sean618/MakerTiles/hardware/Boards/Extra/USBPower/v0.5/USBPower.kicad_pcb

## KiCad design hardware/Boards/Extra/USBPower/v0.5/USBPower.kicad_pcb (2026-06-21)

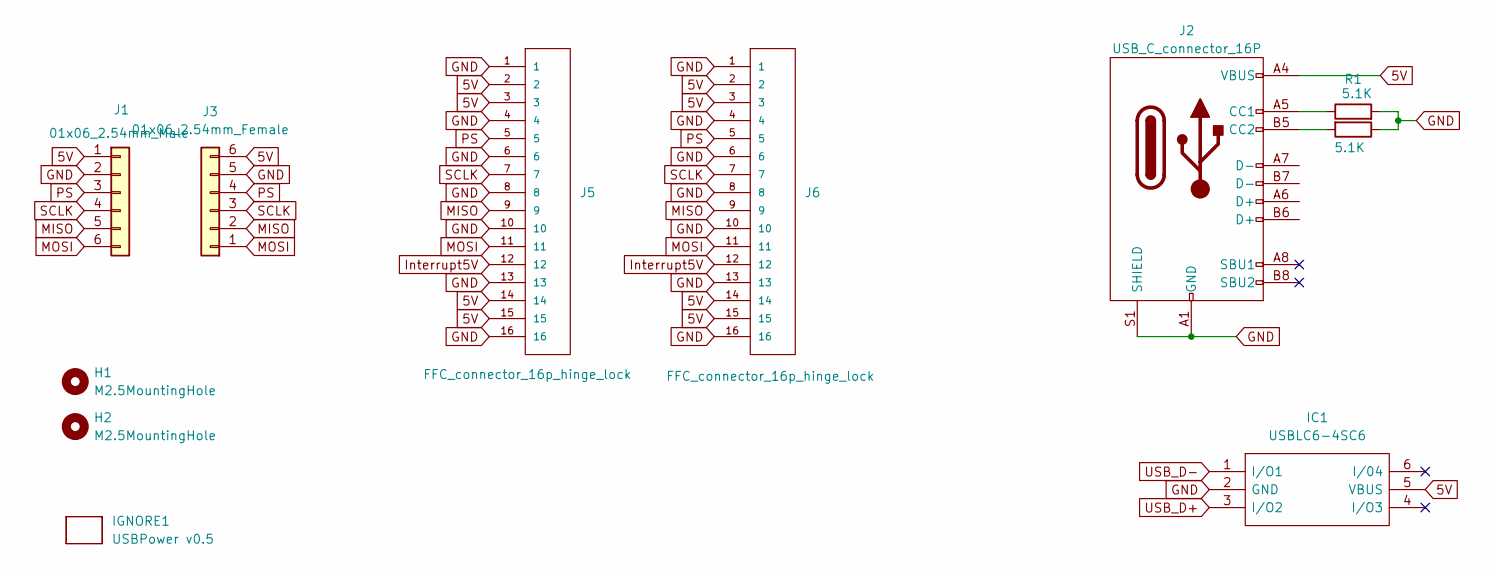
[picture p28: schematic USBPower.kicad_sch]

Parts:
H1, H2: M2.5MountingHole; MountingHole_2.7mm_M2.5_ISO7380
IC1: USBLC6-4SC6; SOT-23-6; Manufacturer_Part_Number USBLC6-2P6
IGNORE1: USBPower v0.5; BoardText
J1: 01x06_2.54mm_Male
J2: USB_C_connector_16P; USB_C_Receptacle_16P
J3: 01x06_2.54mm_Female
J5, J6: FFC_connector_16p_hinge_lock
R1, R2: 5.1K; R_0402_1005Metric

Connections:
5V: IC1.5 (VBUS), J1.1, J2.A4 (VBUS), J2.A9 (VBUS), J2.B4 (VBUS), J2.B9 (VBUS), J3.6, J5.2, J5.3, J5.14, J5.15, J6.2, J6.3, J6.14, J6.15
GND: IC1.2 (GND), J1.2, J2.A1 (GND), J2.A12 (GND), J2.B1 (GND), J2.B12 (GND), J2.S1 (SHIELD), J3.5, J5.1, J5.4, J5.6, J5.8, J5.10, J5.13, J5.16, J6.1, J6.4, J6.6, J6.8, J6.10, J6.13, J6.16, R1.2, R2.1
Interrupt5V: J5.12, J6.12
MISO: J1.5, J3.2, J5.9, J6.9
MOSI: J1.6, J3.1, J5.11, J6.11
unnamed: J2.A5 (CC1), R1.1
unnamed: J2.B5 (CC2), R2.2
PS: J1.3, J3.4, J5.5, J6.5
SCLK: J1.4, J3.3, J5.7, J6.7
USB_D+: IC1.3 (I/O2)
USB_D-: IC1.1 (I/O1)

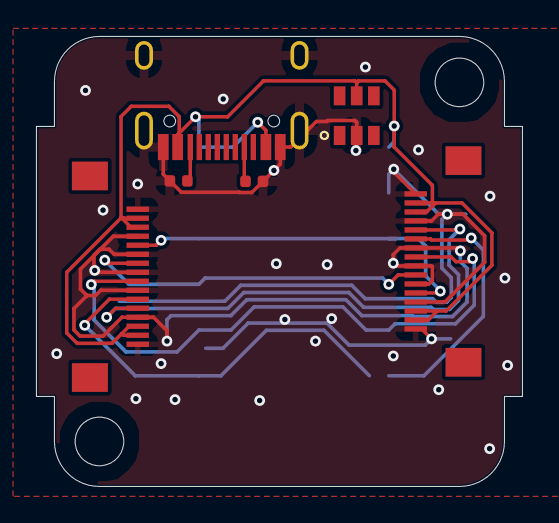
[picture p29: board USBPower.kicad_pcb from above]

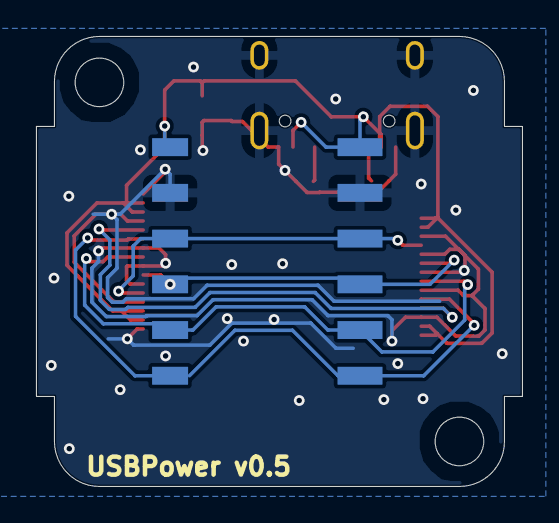
[picture p30: board USBPower.kicad_pcb from below]

Board: 4 copper layers, 27.0 x 25.0 mm, 11 parts (2 on the bottom side), 9 nets.
