sean618/MakerTiles/hardware/Boards/LedMatrix/v0.2/LedMatrix.kicad_pcb

## KiCad design hardware/Boards/LedMatrix/v0.2/LedMatrix.kicad_pcb (2026-06-21, an earlier design)

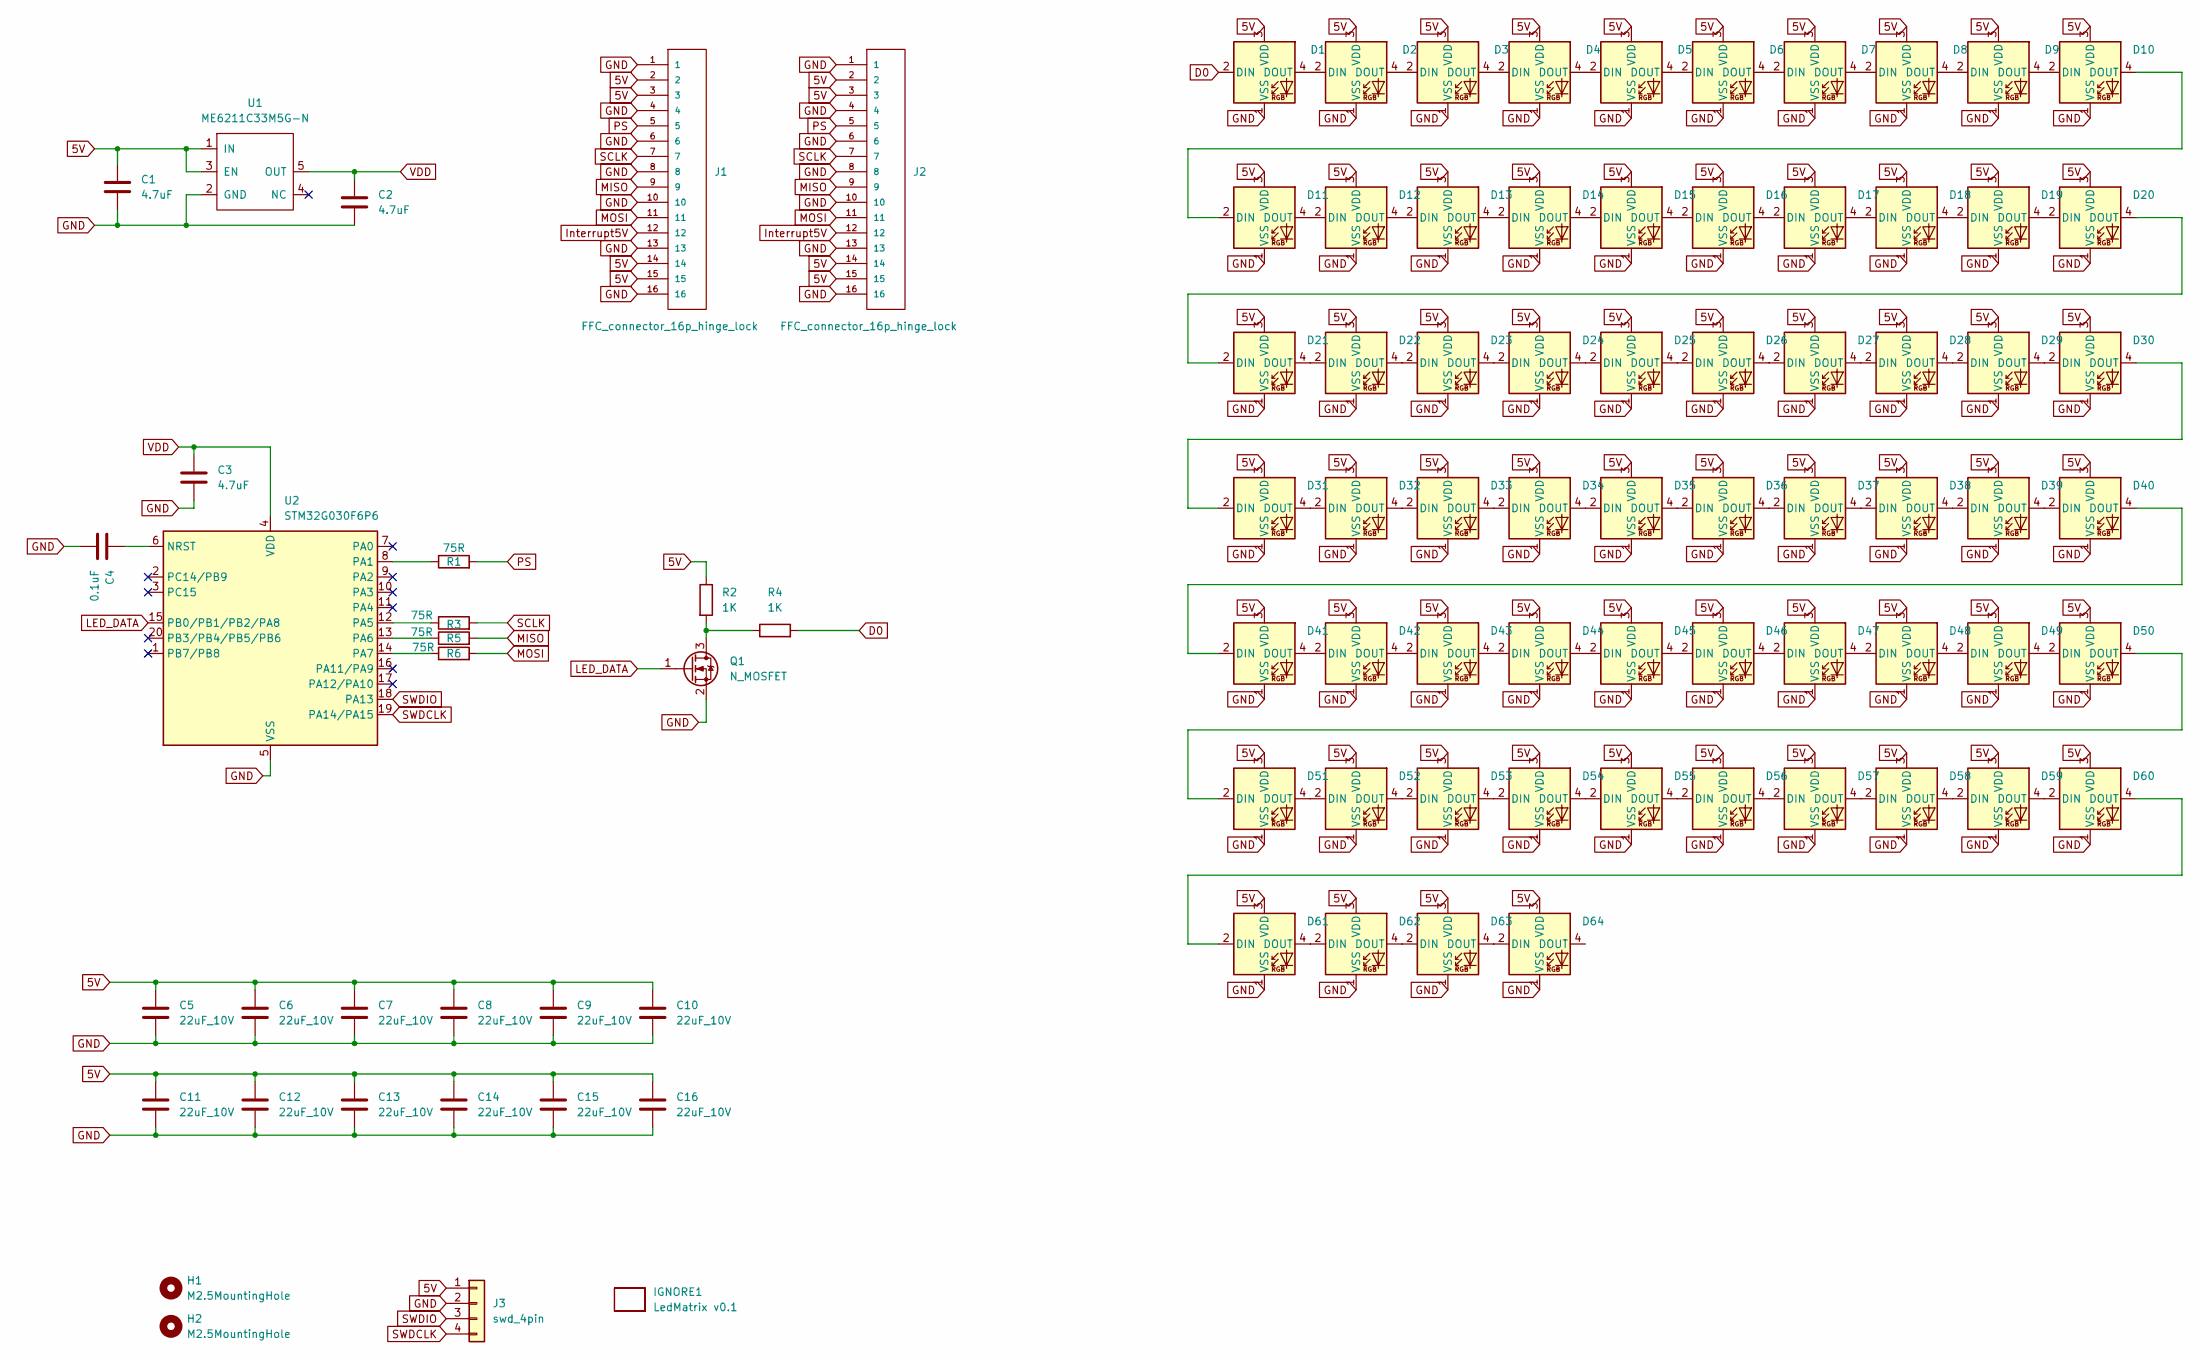
[picture p31: schematic LedMatrix.kicad_sch]

Parts:
C1, C2, C3: 4.7uF; C_0402_1005Metric
C4: 0.1uF; C_0402_1005Metric
C5, C6, C7, C8, C9, C10, C11, C12, C13, C14, C15, C16: 22uF_10V; C_0603_1608Metric
D1, D2, D3, D4, D5, D6, D7, D8, D9, D10, D11, D12, D13, D14, D15, D16, D17, D18, D19, D20, D21, D22, D23, D24, D25, D26, D27, D28, D29, D30, D31, D32, D33, D34, D35, D36, D37, D38, D39, D40, D41, D42, D43, D44, D45, D46, D47, D48, D49, D50, D51, D52, D53, D54, D55, D56, D57, D58, D59, D60, D61, D62, D63, D64: xl_ws2812b_small
H1, H2: M2.5MountingHole; MountingHole_2.7mm_M2.5_ISO7380
IGNORE1: LedMatrix v0.1; BoardText
J1, J2: FFC_connector_16p_hinge_lock
J3: swd_4pin; swd_header
Q1: N_MOSFET; SOT-23
R1, R3, R5, R6: 75R; R_0402_1005Metric
R2, R4: 1K; R_0402_1005Metric
U1: ME6211C33M5G-N; SOT-23-5
U2: STM32G030F6P6; TSSOP-20_4.4x6.5mm_P0.65mm

Connections:
5V: C1.1, C5.1, C6.1, C7.1, C8.1, C9.1, C10.1, C11.1, C12.1, C13.1, C14.1, C15.1, C16.1, D1.3 (VDD), D2.3 (VDD), D3.3 (VDD), D4.3 (VDD), D5.3 (VDD), D6.3 (VDD), D7.3 (VDD), D8.3 (VDD), D9.3 (VDD), D10.3 (VDD), D11.3 (VDD), D12.3 (VDD), D13.3 (VDD), D14.3 (VDD), D15.3 (VDD), D16.3 (VDD), D17.3 (VDD), D18.3 (VDD), D19.3 (VDD), D20.3 (VDD), D21.3 (VDD), D22.3 (VDD), D23.3 (VDD), D24.3 (VDD), D25.3 (VDD), D26.3 (VDD), D27.3 (VDD), D28.3 (VDD), D29.3 (VDD), D30.3 (VDD), D31.3 (VDD), D32.3 (VDD), D33.3 (VDD), D34.3 (VDD), D35.3 (VDD), D36.3 (VDD), D37.3 (VDD), D38.3 (VDD), D39.3 (VDD), D40.3 (VDD), D41.3 (VDD), D42.3 (VDD), D43.3 (VDD), D44.3 (VDD), D45.3 (VDD), D46.3 (VDD), D47.3 (VDD), D48.3 (VDD), D49.3 (VDD), D50.3 (VDD), D51.3 (VDD), D52.3 (VDD), D53.3 (VDD), D54.3 (VDD), D55.3 (VDD), D56.3 (VDD), D57.3 (VDD), D58.3 (VDD), D59.3 (VDD), D60.3 (VDD), D61.3 (VDD), D62.3 (VDD), D63.3 (VDD), D64.3 (VDD), J1.2, J1.3, J1.14, J1.15, J2.2, J2.3, J2.14, J2.15, J3.1, R2.1, U1.1 (IN), U1.3 (EN)
D0: D1.2 (DIN), R4.2
GND: C1.2, C2.2, C3.2, C4.2, C5.2, C6.2, C7.2, C8.2, C9.2, C10.2, C11.2, C12.2, C13.2, C14.2, C15.2, C16.2, D1.1 (VSS), D2.1 (VSS), D3.1 (VSS), D4.1 (VSS), D5.1 (VSS), D6.1 (VSS), D7.1 (VSS), D8.1 (VSS), D9.1 (VSS), D10.1 (VSS), D11.1 (VSS), D12.1 (VSS), D13.1 (VSS), D14.1 (VSS), D15.1 (VSS), D16.1 (VSS), D17.1 (VSS), D18.1 (VSS), D19.1 (VSS), D20.1 (VSS), D21.1 (VSS), D22.1 (VSS), D23.1 (VSS), D24.1 (VSS), D25.1 (VSS), D26.1 (VSS), D27.1 (VSS), D28.1 (VSS), D29.1 (VSS), D30.1 (VSS), D31.1 (VSS), D32.1 (VSS), D33.1 (VSS), D34.1 (VSS), D35.1 (VSS), D36.1 (VSS), D37.1 (VSS), D38.1 (VSS), D39.1 (VSS), D40.1 (VSS), D41.1 (VSS), D42.1 (VSS), D43.1 (VSS), D44.1 (VSS), D45.1 (VSS), D46.1 (VSS), D47.1 (VSS), D48.1 (VSS), D49.1 (VSS), D50.1 (VSS), D51.1 (VSS), D52.1 (VSS), D53.1 (VSS), D54.1 (VSS), D55.1 (VSS), D56.1 (VSS), D57.1 (VSS), D58.1 (VSS), D59.1 (VSS), D60.1 (VSS), D61.1 (VSS), D62.1 (VSS), D63.1 (VSS), D64.1 (VSS), J1.1, J1.4, J1.6, J1.8, J1.10, J1.13, J1.16, J2.1, J2.4, J2.6, J2.8, J2.10, J2.13, J2.16, J3.2, Q1.2 (S), U1.2 (GND), U2.5 (VSS)
Interrupt5V: J1.12, J2.12
LED_DATA: Q1.1 (G), U2.15 (PB0/PB1/PB2/PA8)
MISO: J1.9, J2.9, R5.2
MOSI: J1.11, J2.11, R6.2
unnamed: D1.4 (DOUT), D2.2 (DIN)
unnamed: D2.4 (DOUT), D3.2 (DIN)
unnamed: D3.4 (DOUT), D4.2 (DIN)
unnamed: D4.4 (DOUT), D5.2 (DIN)
unnamed: D5.4 (DOUT), D6.2 (DIN)
unnamed: D6.4 (DOUT), D7.2 (DIN)
unnamed: D7.4 (DOUT), D8.2 (DIN)
unnamed: D8.4 (DOUT), D9.2 (DIN)
unnamed: D9.4 (DOUT), D10.2 (DIN)
unnamed: D10.4 (DOUT), D11.2 (DIN)
unnamed: D11.4 (DOUT), D12.2 (DIN)
unnamed: D12.4 (DOUT), D13.2 (DIN)
unnamed: D13.4 (DOUT), D14.2 (DIN)
unnamed: D14.4 (DOUT), D15.2 (DIN)
unnamed: D15.4 (DOUT), D16.2 (DIN)
unnamed: D16.4 (DOUT), D17.2 (DIN)
unnamed: D17.4 (DOUT), D18.2 (DIN)
unnamed: D18.4 (DOUT), D19.2 (DIN)
unnamed: D19.4 (DOUT), D20.2 (DIN)
unnamed: D20.4 (DOUT), D21.2 (DIN)
unnamed: D21.4 (DOUT), D22.2 (DIN)
unnamed: D22.4 (DOUT), D23.2 (DIN)
unnamed: D23.4 (DOUT), D24.2 (DIN)
unnamed: D24.4 (DOUT), D25.2 (DIN)
unnamed: D25.4 (DOUT), D26.2 (DIN)
unnamed: D26.4 (DOUT), D27.2 (DIN)
unnamed: D27.4 (DOUT), D28.2 (DIN)
unnamed: D28.4 (DOUT), D29.2 (DIN)
unnamed: D29.4 (DOUT), D30.2 (DIN)
unnamed: D30.4 (DOUT), D31.2 (DIN)
unnamed: D31.4 (DOUT), D32.2 (DIN)
unnamed: D32.4 (DOUT), D33.2 (DIN)
unnamed: D33.4 (DOUT), D34.2 (DIN)
unnamed: D34.4 (DOUT), D35.2 (DIN)
unnamed: D35.4 (DOUT), D36.2 (DIN)
unnamed: D36.4 (DOUT), D37.2 (DIN)
unnamed: D37.4 (DOUT), D38.2 (DIN)
unnamed: D38.4 (DOUT), D39.2 (DIN)
unnamed: D39.4 (DOUT), D40.2 (DIN)
unnamed: D40.4 (DOUT), D41.2 (DIN)
unnamed: D41.4 (DOUT), D42.2 (DIN)
unnamed: D42.4 (DOUT), D43.2 (DIN)
unnamed: D43.4 (DOUT), D44.2 (DIN)
unnamed: D44.4 (DOUT), D45.2 (DIN)
unnamed: D45.4 (DOUT), D46.2 (DIN)
unnamed: D46.4 (DOUT), D47.2 (DIN)
unnamed: D47.4 (DOUT), D48.2 (DIN)
unnamed: D48.4 (DOUT), D49.2 (DIN)
unnamed: D49.4 (DOUT), D50.2 (DIN)
unnamed: D50.4 (DOUT), D51.2 (DIN)
unnamed: D51.4 (DOUT), D52.2 (DIN)
unnamed: D52.4 (DOUT), D53.2 (DIN)
unnamed: D53.4 (DOUT), D54.2 (DIN)
unnamed: D54.4 (DOUT), D55.2 (DIN)
unnamed: D55.4 (DOUT), D56.2 (DIN)
unnamed: D56.4 (DOUT), D57.2 (DIN)
unnamed: D57.4 (DOUT), D58.2 (DIN)
unnamed: D58.4 (DOUT), D59.2 (DIN)
unnamed: D59.4 (DOUT), D60.2 (DIN)
unnamed: D60.4 (DOUT), D61.2 (DIN)
unnamed: D61.4 (DOUT), D62.2 (DIN)
unnamed: D62.4 (DOUT), D63.2 (DIN)
unnamed: D63.4 (DOUT), D64.2 (DIN)
unnamed: Q1.3 (D), R2.2, R4.1
unnamed: C4.1, U2.6 (NRST)
unnamed: R1.1, U2.8 (PA1)
unnamed: R3.1, U2.12 (PA5)
unnamed: R5.1, U2.13 (PA6)
unnamed: R6.1, U2.14 (PA7)
PS: J1.5, J2.5, R1.2
SCLK: J1.7, J2.7, R3.2
SWDCLK: J3.4, U2.19 (PA14/PA15)
SWDIO: J3.3, U2.18 (PA13)
VDD: C2.1, C3.1, U1.5 (OUT), U2.4 (VDD)

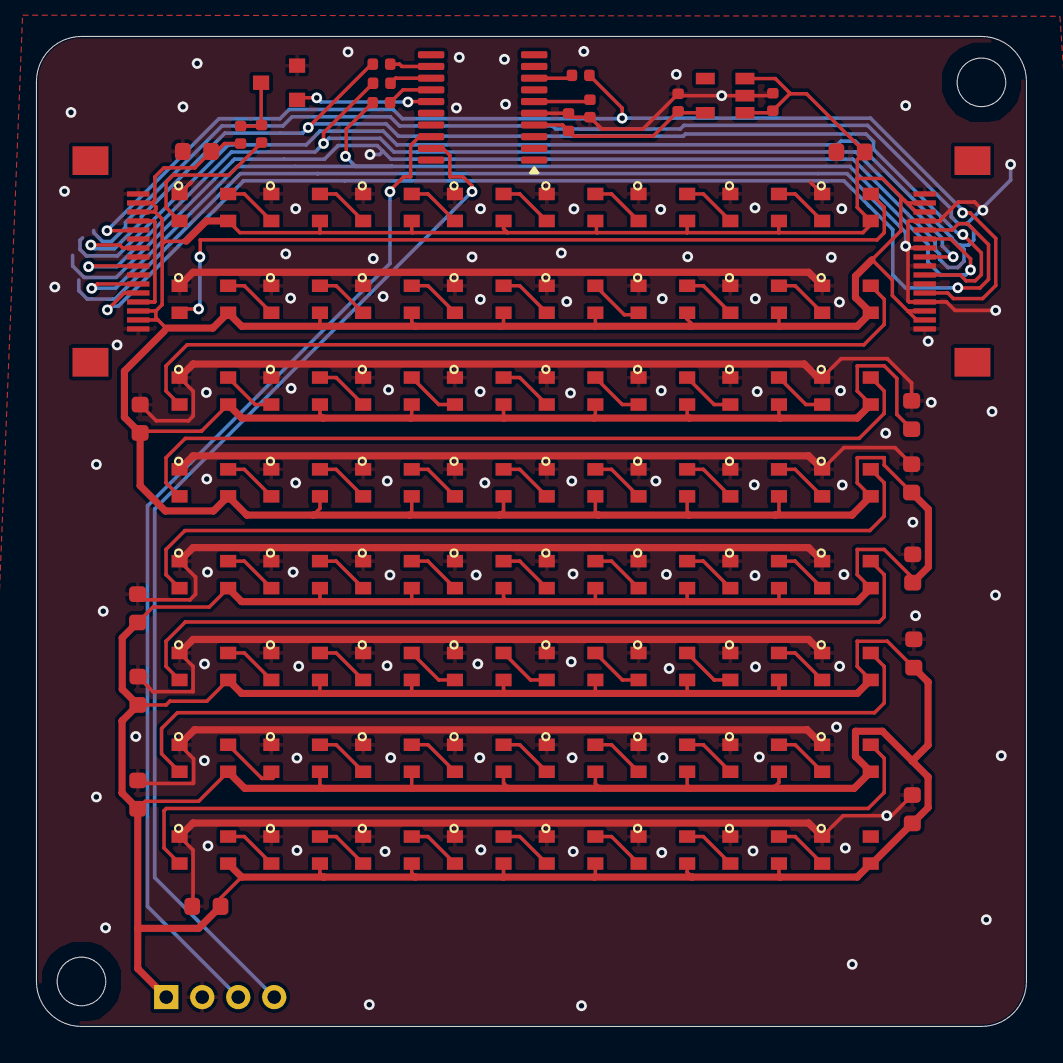
[picture p32: board hardware/Boards/LedMatrix/v0.2/LedMatrix.kicad_pcb from above]

Board: 4 copper layers, 55.0 x 55.0 mm, 95 parts (0 on the bottom side), 81 nets.
