sean618/MakerTiles/hardware/Boards/LedMatrix/v0.1/LedMatrix.kicad_pcb

## KiCad design hardware/Boards/LedMatrix/v0.1/LedMatrix.kicad_pcb (2026-06-21, an earlier design)

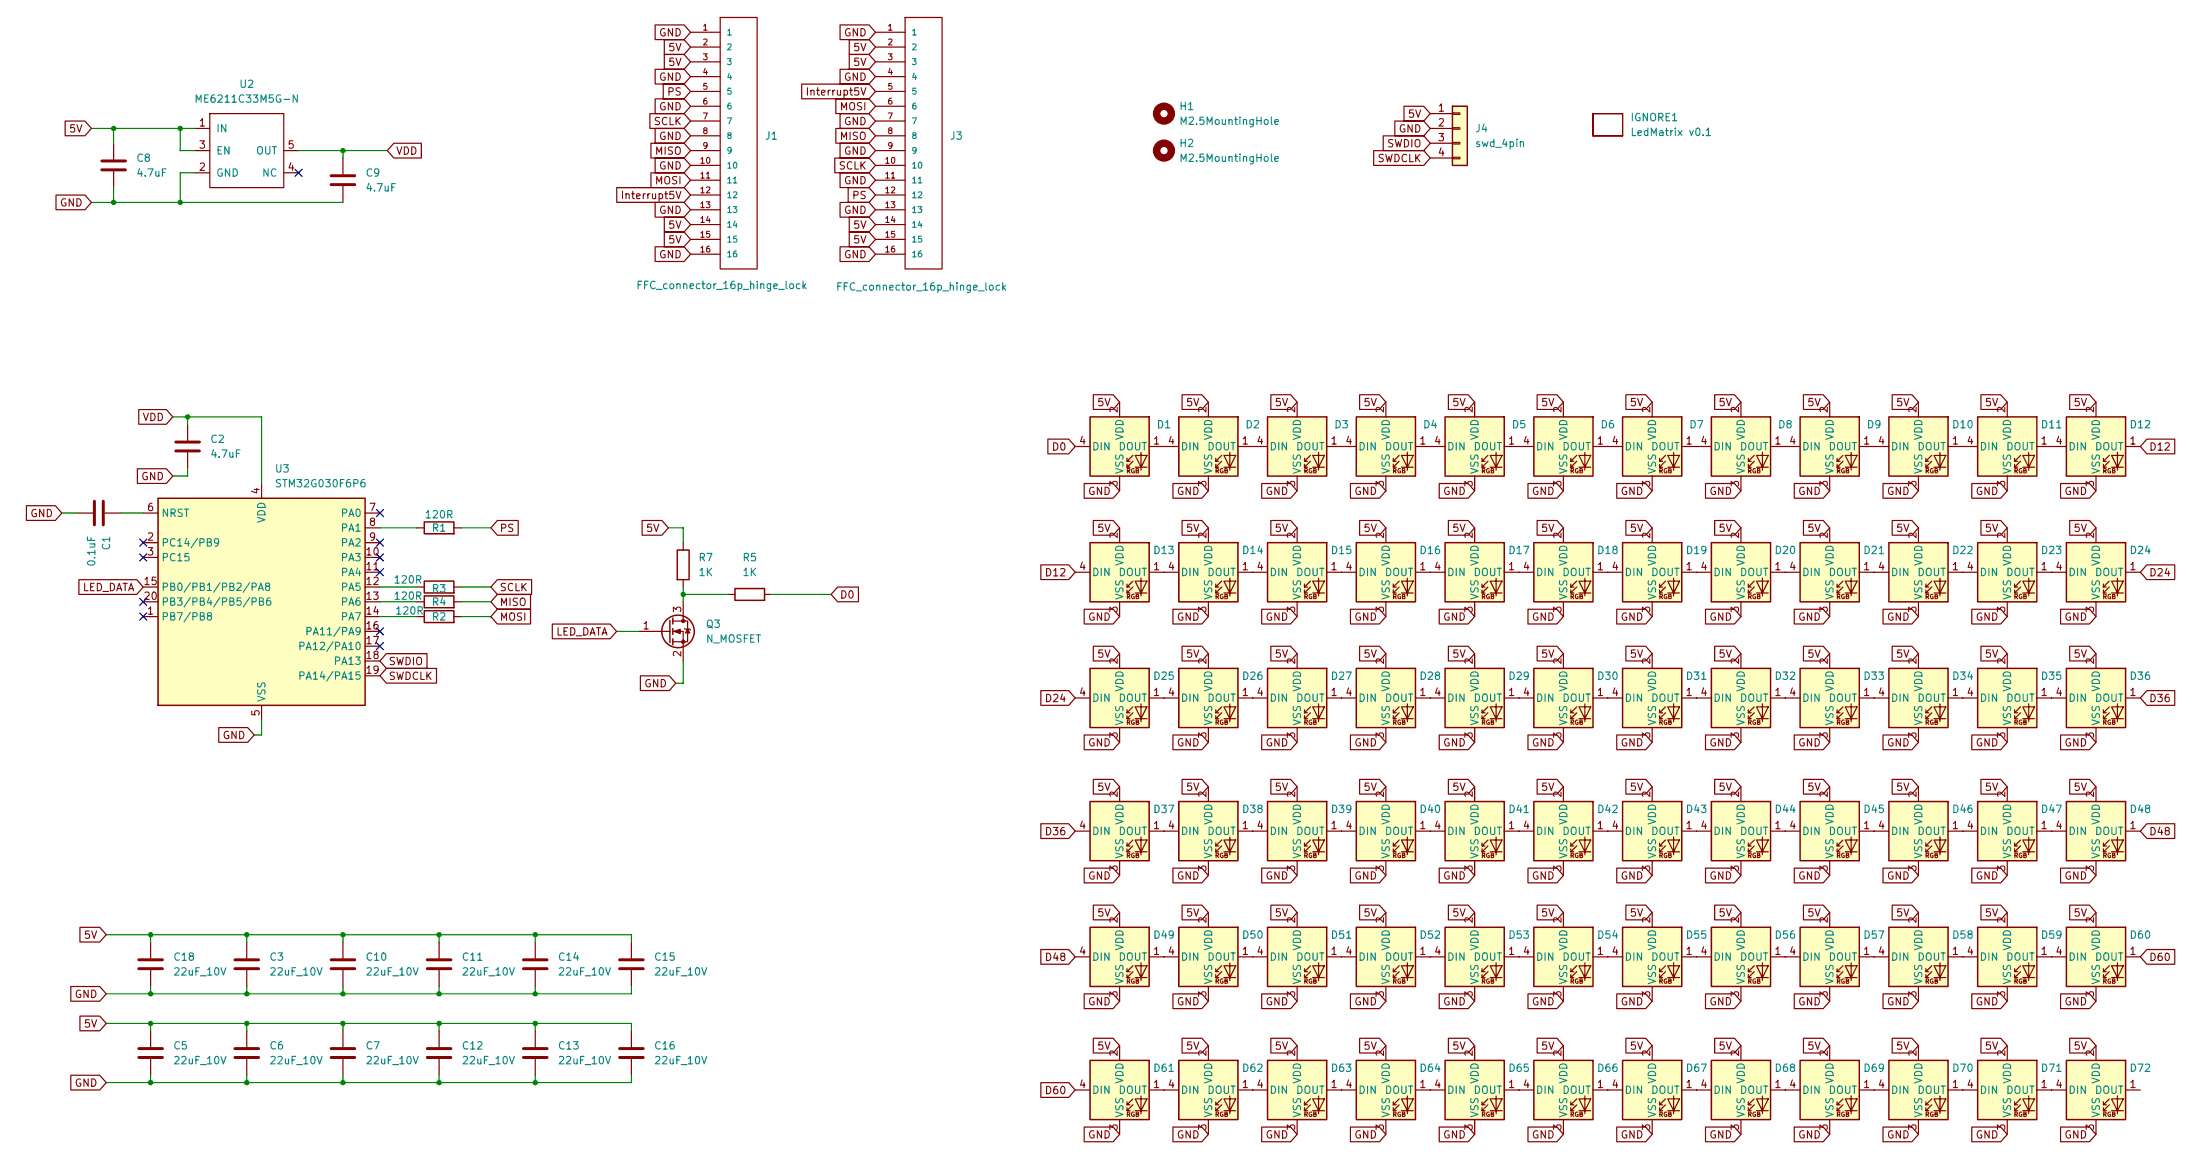
[picture p33: schematic LedMatrix.kicad_sch]

Parts:
C1: 0.1uF; C_0402_1005Metric
C2, C8, C9: 4.7uF; C_0402_1005Metric
C3, C5, C6, C7, C10, C11, C12, C13, C14, C15, C16, C18: 22uF_10V; C_0603_1608Metric
D1, D2, D3, D4, D5, D6, D7, D8, D9, D10, D11, D12, D13, D14, D15, D16, D17, D18, D19, D20, D21, D22, D23, D24, D25, D26, D27, D28, D29, D30, D31, D32, D33, D34, D35, D36, D37, D38, D39, D40, D41, D42, D43, D44, D45, D46, D47, D48, D49, D50, D51, D52, D53, D54, D55, D56, D57, D58, D59, D60, D61, D62, D63, D64, D65, D66, D67, D68, D69, D70, D71, D72: ws2812b_1615; WS2812B_1615
H1, H2: M2.5MountingHole; MountingHole_2.7mm_M2.5_ISO7380
IGNORE1: LedMatrix v0.1; BoardText
J1, J3: FFC_connector_16p_hinge_lock
J4: swd_4pin; swd_header
Q3: N_MOSFET; SOT-23
R1, R2, R3, R4: 120R; R_0402_1005Metric
R5, R7: 1K; R_0402_1005Metric
U2: ME6211C33M5G-N; SOT-23-5
U3: STM32G030F6P6; TSSOP-20_4.4x6.5mm_P0.65mm

Connections:
5V: C3.1, C5.1, C6.1, C7.1, C8.1, C10.1, C11.1, C12.1, C13.1, C14.1, C15.1, C16.1, C18.1, D1.2 (VDD), D2.2 (VDD), D3.2 (VDD), D4.2 (VDD), D5.2 (VDD), D6.2 (VDD), D7.2 (VDD), D8.2 (VDD), D9.2 (VDD), D10.2 (VDD), D11.2 (VDD), D12.2 (VDD), D13.2 (VDD), D14.2 (VDD), D15.2 (VDD), D16.2 (VDD), D17.2 (VDD), D18.2 (VDD), D19.2 (VDD), D20.2 (VDD), D21.2 (VDD), D22.2 (VDD), D23.2 (VDD), D24.2 (VDD), D25.2 (VDD), D26.2 (VDD), D27.2 (VDD), D28.2 (VDD), D29.2 (VDD), D30.2 (VDD), D31.2 (VDD), D32.2 (VDD), D33.2 (VDD), D34.2 (VDD), D35.2 (VDD), D36.2 (VDD), D37.2 (VDD), D38.2 (VDD), D39.2 (VDD), D40.2 (VDD), D41.2 (VDD), D42.2 (VDD), D43.2 (VDD), D44.2 (VDD), D45.2 (VDD), D46.2 (VDD), D47.2 (VDD), D48.2 (VDD), D49.2 (VDD), D50.2 (VDD), D51.2 (VDD), D52.2 (VDD), D53.2 (VDD), D54.2 (VDD), D55.2 (VDD), D56.2 (VDD), D57.2 (VDD), D58.2 (VDD), D59.2 (VDD), D60.2 (VDD), D61.2 (VDD), D62.2 (VDD), D63.2 (VDD), D64.2 (VDD), D65.2 (VDD), D66.2 (VDD), D67.2 (VDD), D68.2 (VDD), D69.2 (VDD), D70.2 (VDD), D71.2 (VDD), D72.2 (VDD), J1.2, J1.3, J1.14, J1.15, J3.2, J3.3, J3.14, J3.15, J4.1, R7.1, U2.1 (IN), U2.3 (EN)
D0: D1.4 (DIN), R5.2
D12: D12.1 (DOUT), D13.4 (DIN)
D24: D24.1 (DOUT), D25.4 (DIN)
D36: D36.1 (DOUT), D37.4 (DIN)
D48: D48.1 (DOUT), D49.4 (DIN)
D60: D60.1 (DOUT), D61.4 (DIN)
GND: C1.2, C2.2, C3.2, C5.2, C6.2, C7.2, C8.2, C9.2, C10.2, C11.2, C12.2, C13.2, C14.2, C15.2, C16.2, C18.2, D1.3 (VSS), D2.3 (VSS), D3.3 (VSS), D4.3 (VSS), D5.3 (VSS), D6.3 (VSS), D7.3 (VSS), D8.3 (VSS), D9.3 (VSS), D10.3 (VSS), D11.3 (VSS), D12.3 (VSS), D13.3 (VSS), D14.3 (VSS), D15.3 (VSS), D16.3 (VSS), D17.3 (VSS), D18.3 (VSS), D19.3 (VSS), D20.3 (VSS), D21.3 (VSS), D22.3 (VSS), D23.3 (VSS), D24.3 (VSS), D25.3 (VSS), D26.3 (VSS), D27.3 (VSS), D28.3 (VSS), D29.3 (VSS), D30.3 (VSS), D31.3 (VSS), D32.3 (VSS), D33.3 (VSS), D34.3 (VSS), D35.3 (VSS), D36.3 (VSS), D37.3 (VSS), D38.3 (VSS), D39.3 (VSS), D40.3 (VSS), D41.3 (VSS), D42.3 (VSS), D43.3 (VSS), D44.3 (VSS), D45.3 (VSS), D46.3 (VSS), D47.3 (VSS), D48.3 (VSS), D49.3 (VSS), D50.3 (VSS), D51.3 (VSS), D52.3 (VSS), D53.3 (VSS), D54.3 (VSS), D55.3 (VSS), D56.3 (VSS), D57.3 (VSS), D58.3 (VSS), D59.3 (VSS), D60.3 (VSS), D61.3 (VSS), D62.3 (VSS), D63.3 (VSS), D64.3 (VSS), D65.3 (VSS), D66.3 (VSS), D67.3 (VSS), D68.3 (VSS), D69.3 (VSS), D70.3 (VSS), D71.3 (VSS), D72.3 (VSS), J1.1, J1.4, J1.6, J1.8, J1.10, J1.13, J1.16, J3.1, J3.4, J3.7, J3.9, J3.11, J3.13, J3.16, J4.2, Q3.2 (S), U2.2 (GND), U3.5 (VSS)
Interrupt5V: J1.12, J3.5
LED_DATA: Q3.1 (G), U3.15 (PB0/PB1/PB2/PA8)
MISO: J1.9, J3.8, R4.2
MOSI: J1.11, J3.6, R2.2
unnamed: D1.1 (DOUT), D2.4 (DIN)
unnamed: D2.1 (DOUT), D3.4 (DIN)
unnamed: D3.1 (DOUT), D4.4 (DIN)
unnamed: D4.1 (DOUT), D5.4 (DIN)
unnamed: D5.1 (DOUT), D6.4 (DIN)
unnamed: D6.1 (DOUT), D7.4 (DIN)
unnamed: D7.1 (DOUT), D8.4 (DIN)
unnamed: D8.1 (DOUT), D9.4 (DIN)
unnamed: D9.1 (DOUT), D10.4 (DIN)
unnamed: D10.1 (DOUT), D11.4 (DIN)
unnamed: D11.1 (DOUT), D12.4 (DIN)
unnamed: D13.1 (DOUT), D14.4 (DIN)
unnamed: D14.1 (DOUT), D15.4 (DIN)
unnamed: D15.1 (DOUT), D16.4 (DIN)
unnamed: D16.1 (DOUT), D17.4 (DIN)
unnamed: D17.1 (DOUT), D18.4 (DIN)
unnamed: D18.1 (DOUT), D19.4 (DIN)
unnamed: D19.1 (DOUT), D20.4 (DIN)
unnamed: D20.1 (DOUT), D21.4 (DIN)
unnamed: D21.1 (DOUT), D22.4 (DIN)
unnamed: D22.1 (DOUT), D23.4 (DIN)
unnamed: D23.1 (DOUT), D24.4 (DIN)
unnamed: D25.1 (DOUT), D26.4 (DIN)
unnamed: D26.1 (DOUT), D27.4 (DIN)
unnamed: D27.1 (DOUT), D28.4 (DIN)
unnamed: D28.1 (DOUT), D29.4 (DIN)
unnamed: D29.1 (DOUT), D30.4 (DIN)
unnamed: D30.1 (DOUT), D31.4 (DIN)
unnamed: D31.1 (DOUT), D32.4 (DIN)
unnamed: D32.1 (DOUT), D33.4 (DIN)
unnamed: D33.1 (DOUT), D34.4 (DIN)
unnamed: D34.1 (DOUT), D35.4 (DIN)
unnamed: D35.1 (DOUT), D36.4 (DIN)
unnamed: D37.1 (DOUT), D38.4 (DIN)
unnamed: D38.1 (DOUT), D39.4 (DIN)
unnamed: D39.1 (DOUT), D40.4 (DIN)
unnamed: D40.1 (DOUT), D41.4 (DIN)
unnamed: D41.1 (DOUT), D42.4 (DIN)
unnamed: D42.1 (DOUT), D43.4 (DIN)
unnamed: D43.1 (DOUT), D44.4 (DIN)
unnamed: D44.1 (DOUT), D45.4 (DIN)
unnamed: D45.1 (DOUT), D46.4 (DIN)
unnamed: D46.1 (DOUT), D47.4 (DIN)
unnamed: D47.1 (DOUT), D48.4 (DIN)
unnamed: D49.1 (DOUT), D50.4 (DIN)
unnamed: D50.1 (DOUT), D51.4 (DIN)
unnamed: D51.1 (DOUT), D52.4 (DIN)
unnamed: D52.1 (DOUT), D53.4 (DIN)
unnamed: D53.1 (DOUT), D54.4 (DIN)
unnamed: D54.1 (DOUT), D55.4 (DIN)
unnamed: D55.1 (DOUT), D56.4 (DIN)
unnamed: D56.1 (DOUT), D57.4 (DIN)
unnamed: D57.1 (DOUT), D58.4 (DIN)
unnamed: D58.1 (DOUT), D59.4 (DIN)
unnamed: D59.1 (DOUT), D60.4 (DIN)
unnamed: D61.1 (DOUT), D62.4 (DIN)
unnamed: D62.1 (DOUT), D63.4 (DIN)
unnamed: D63.1 (DOUT), D64.4 (DIN)
unnamed: D64.1 (DOUT), D65.4 (DIN)
unnamed: D65.1 (DOUT), D66.4 (DIN)
unnamed: D66.1 (DOUT), D67.4 (DIN)
unnamed: D67.1 (DOUT), D68.4 (DIN)
unnamed: D68.1 (DOUT), D69.4 (DIN)
unnamed: D69.1 (DOUT), D70.4 (DIN)
unnamed: D70.1 (DOUT), D71.4 (DIN)
unnamed: D71.1 (DOUT), D72.4 (DIN)
unnamed: Q3.3 (D), R5.1, R7.2
unnamed: C1.1, U3.6 (NRST)
unnamed: R1.1, U3.8 (PA1)
unnamed: R3.1, U3.12 (PA5)
unnamed: R4.1, U3.13 (PA6)
unnamed: R2.1, U3.14 (PA7)
PS: J1.5, J3.12, R1.2
SCLK: J1.7, J3.10, R3.2
SWDCLK: J4.4, U3.19 (PA14/PA15)
SWDIO: J4.3, U3.18 (PA13)
VDD: C2.1, C9.1, U2.5 (OUT), U3.4 (VDD)

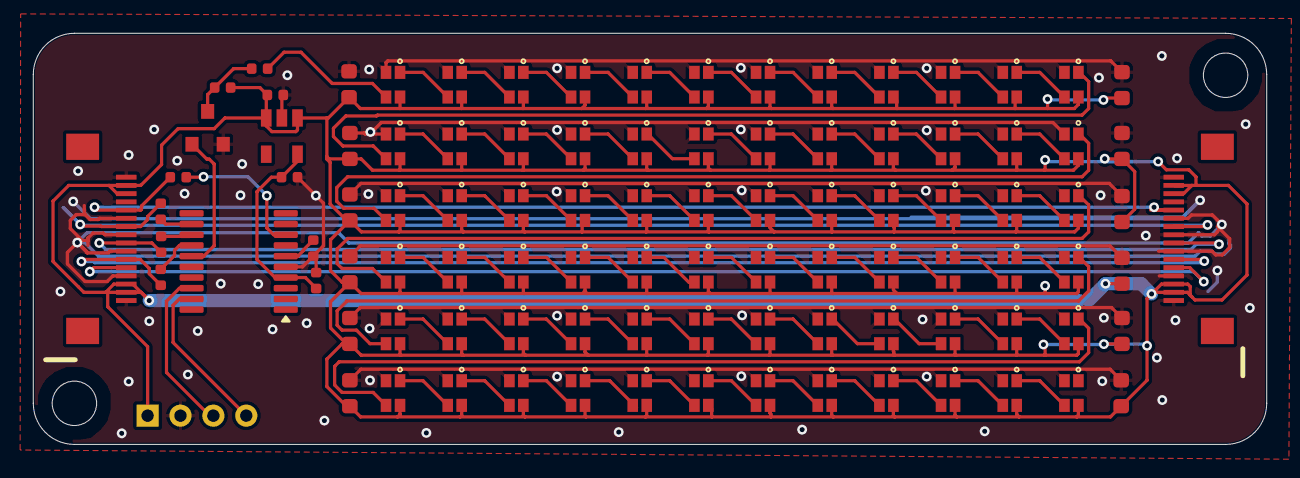
[picture p34: board hardware/Boards/LedMatrix/v0.1/LedMatrix.kicad_pcb from above]

Board: 4 copper layers, 75.0 x 25.0 mm, 103 parts (0 on the bottom side), 89 nets.
