sean618/MakerTiles/hardware/Boards/Motor/v0.7/Motor.kicad_pcb

## KiCad design hardware/Boards/Motor/v0.7/Motor.kicad_pcb (2026-06-21, an earlier design)

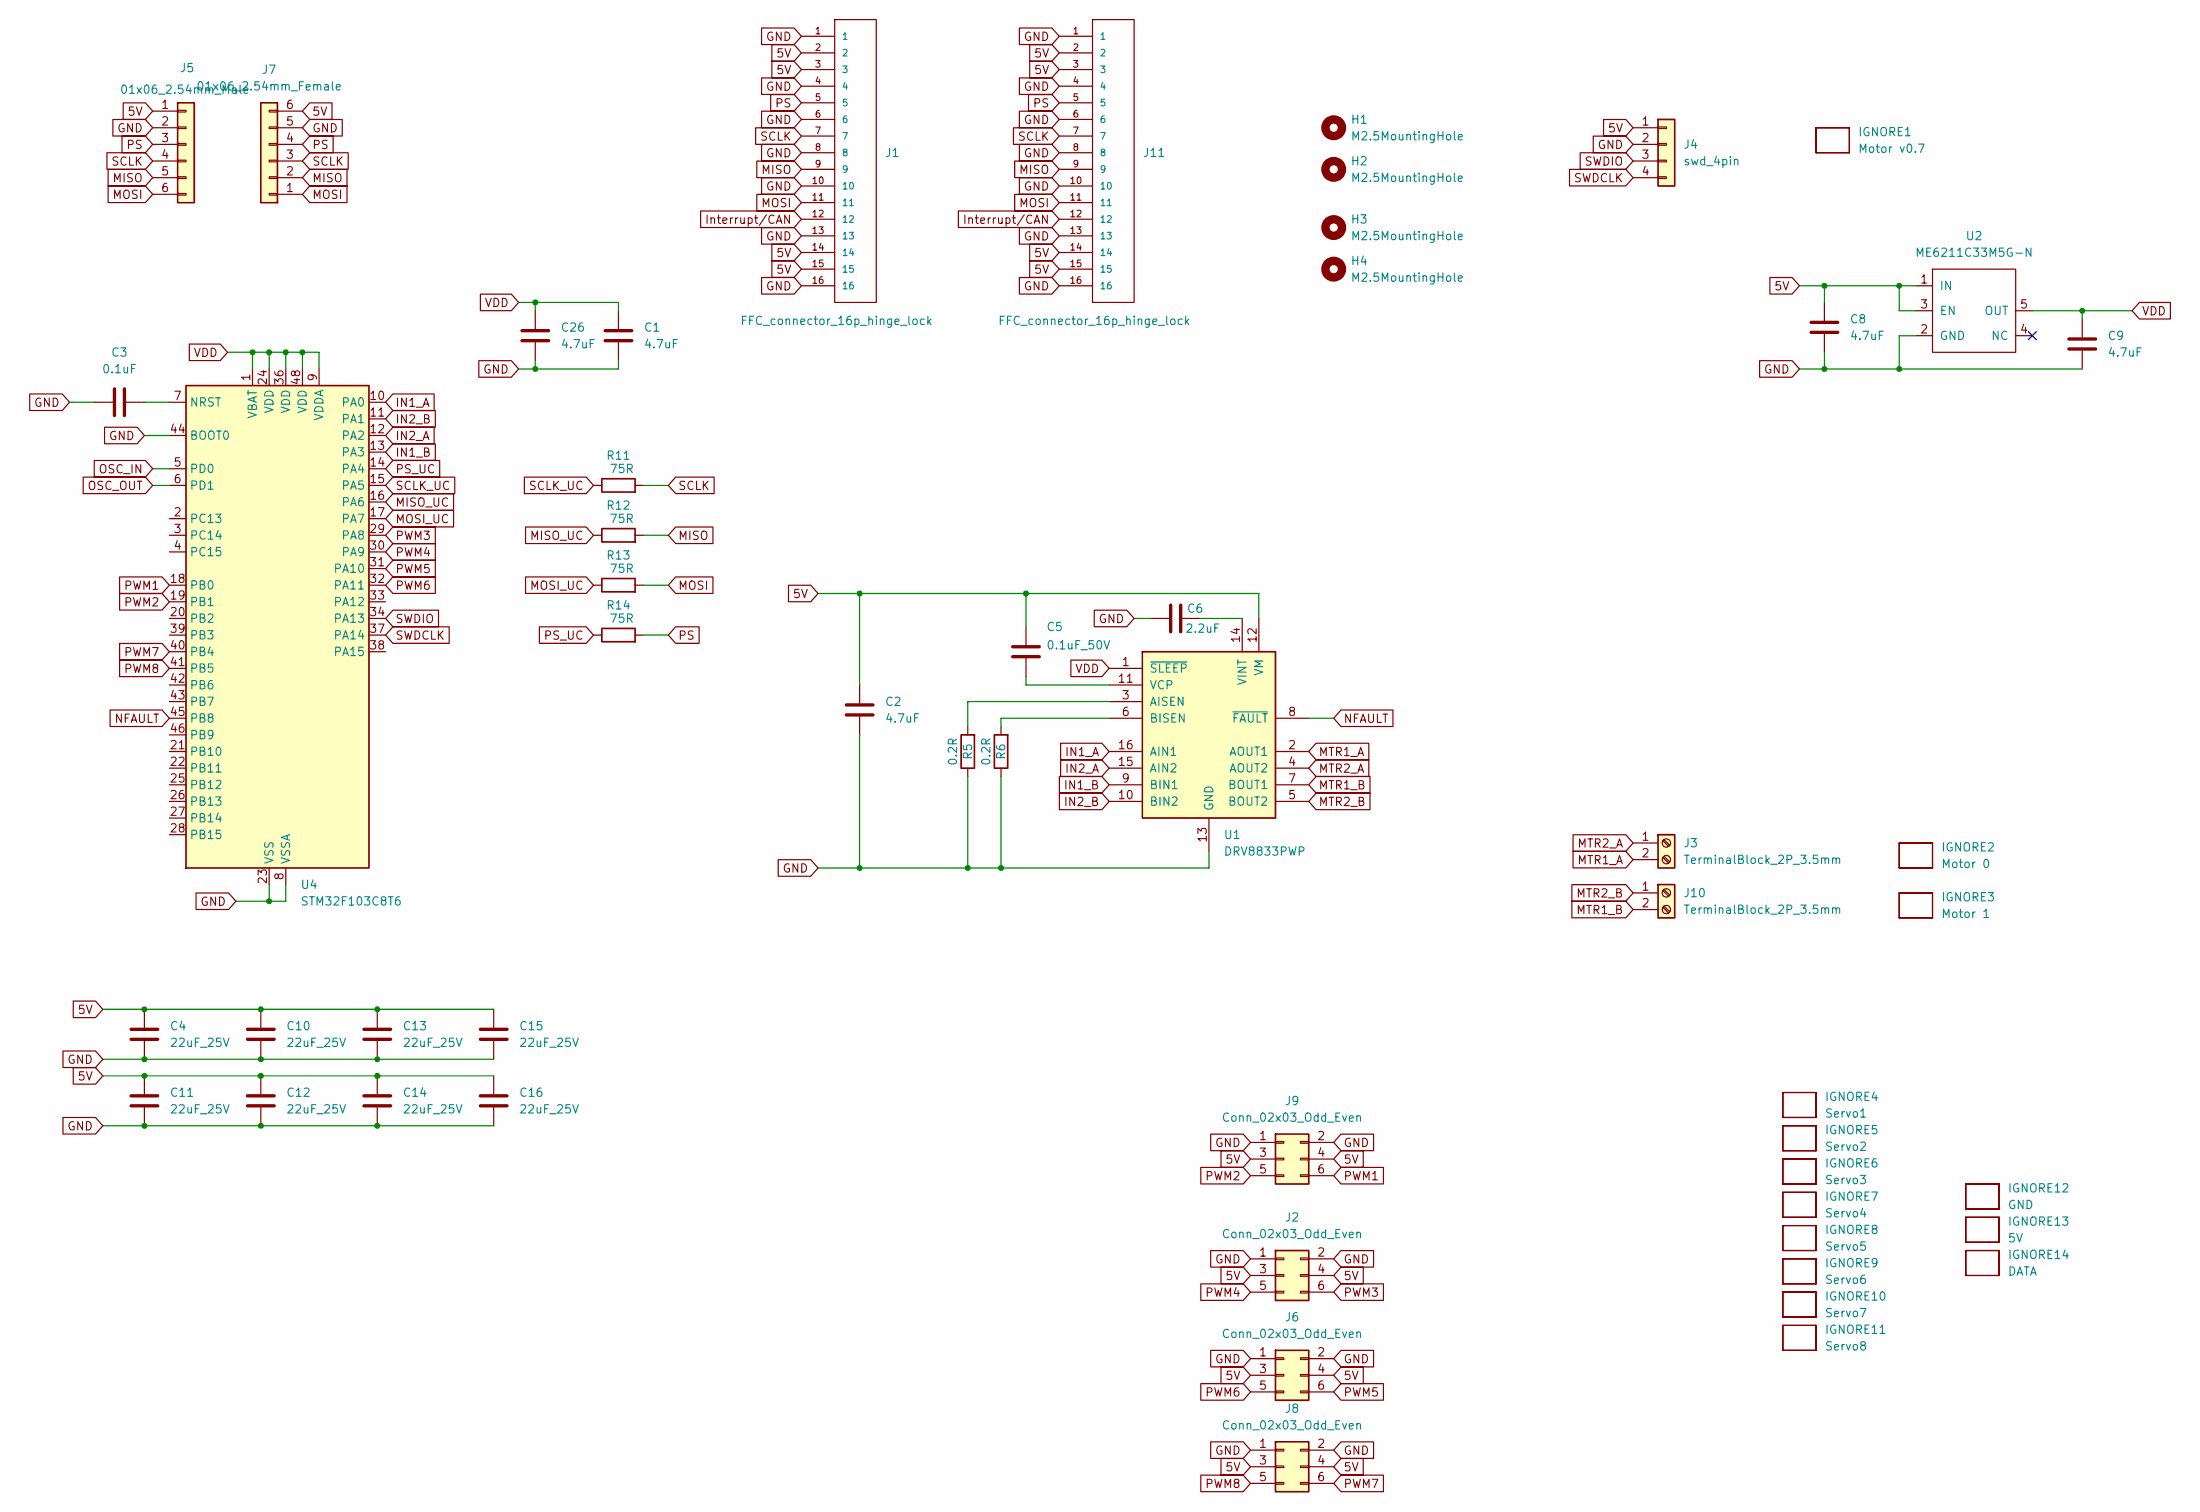
[picture p35: schematic Motor.kicad_sch]

Parts:
C1, C2, C8, C9, C26: 4.7uF; C_0402_1005Metric
C3: 0.1uF; C_0402_1005Metric
C4, C10, C11, C12, C13, C14, C15, C16: 22uF_25V; C_0805_2012Metric
C5: 0.1uF_50V; C_0402_1005Metric
C6: 2.2uF; C_0402_1005Metric
H1, H2, H3, H4: M2.5MountingHole; MountingHole_2.7mm_M2.5_ISO7380
IGNORE1: Motor v0.7; BoardText
IGNORE2: Motor 0; BoardText
IGNORE3: Motor 1; BoardText
IGNORE4: Servo1; BoardText
IGNORE5: Servo2; BoardText
IGNORE6: Servo3; BoardText
IGNORE7: Servo4; BoardText
IGNORE8: Servo5; BoardText
IGNORE9: Servo6; BoardText
IGNORE10: Servo7; BoardText
IGNORE11: Servo8; BoardText
IGNORE12: GND; BoardText
IGNORE13: 5V; BoardText
IGNORE14: DATA; BoardText
J1, J11: FFC_connector_16p_hinge_lock
J2, J6, J8, J9: Conn_02x03_Odd_Even; PinHeader_2x03_P2.54mm_Vertical_SMD
J3, J10: TerminalBlock_2P_3.5mm
J4: swd_4pin; swd_header
J5: 01x06_2.54mm_Male
J7: 01x06_2.54mm_Female
R5, R6: 0.2R; R_1210_3225Metric
R11, R12, R13, R14: 75R; R_0402_1005Metric
U1: DRV8833PWP; HTSSOP-16-1EP_4.4x5mm_P0.65mm_EP3.4x5mm_Mask2.46x2.31mm_The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
U2: ME6211C33M5G-N; SOT-23-5
U4: STM32F103C8T6; LQFP-48_7x7mm_P0.5mm

Connections:
5V: C2.1, C4.1, C5.1, C8.1, C10.1, C11.1, C12.1, C13.1, C14.1, C15.1, C16.1, J1.2, J1.3, J1.14, J1.15, J2.3, J2.4, J4.1, J5.1, J6.3, J6.4, J7.6, J8.3, J8.4, J9.3, J9.4, J11.2, J11.3, J11.14, J11.15, U1.12 (VM), U2.1 (IN), U2.3 (EN)
GND: C1.2, C2.2, C3.1, C4.2, C6.1, C8.2, C9.2, C10.2, C11.2, C12.2, C13.2, C14.2, C15.2, C16.2, C26.2, J1.1, J1.4, J1.6, J1.8, J1.10, J1.13, J1.16, J2.1, J2.2, J4.2, J5.2, J6.1, J6.2, J7.5, J8.1, J8.2, J9.1, J9.2, J11.1, J11.4, J11.6, J11.8, J11.10, J11.13, J11.16, R5.1, R6.1, U1.13 (GND), U1.17 (GND), U2.2 (GND), U4.8 (VSSA), U4.23 (VSS), U4.35 (VSS), U4.44 (BOOT0), U4.47 (VSS)
IN1_A: U1.16 (AIN1), U4.10 (PA0)
IN1_B: U1.9 (BIN1), U4.13 (PA3)
IN2_A: U1.15 (AIN2), U4.12 (PA2)
IN2_B: U1.10 (BIN2), U4.11 (PA1)
Interrupt/CAN: J1.12, J11.12
MISO: J1.9, J5.5, J7.2, J11.9, R12.2
MISO_UC: R12.1, U4.16 (PA6)
MOSI: J1.11, J5.6, J7.1, J11.11, R13.2
MOSI_UC: R13.1, U4.17 (PA7)
MTR1_A: J3.2, U1.2 (AOUT1)
MTR1_B: J10.2, U1.7 (BOUT1)
MTR2_A: J3.1, U1.4 (AOUT2)
MTR2_B: J10.1, U1.5 (BOUT2)
NFAULT: U1.8 (~FAULT), U4.45 (PB8)
unnamed: R5.2, U1.3 (AISEN)
unnamed: R6.2, U1.6 (BISEN)
unnamed: C5.2, U1.11 (VCP)
unnamed: C6.2, U1.14 (VINT)
unnamed: C3.2, U4.7 (NRST)
OSC_IN: U4.5 (PD0)
OSC_OUT: U4.6 (PD1)
PS: J1.5, J5.3, J7.4, J11.5, R14.2
PS_UC: R14.1, U4.14 (PA4)
PWM1: J9.6, U4.18 (PB0)
PWM2: J9.5, U4.19 (PB1)
PWM3: J2.6, U4.29 (PA8)
PWM4: J2.5, U4.30 (PA9)
PWM5: J6.6, U4.31 (PA10)
PWM6: J6.5, U4.32 (PA11)
PWM7: J8.6, U4.40 (PB4)
PWM8: J8.5, U4.41 (PB5)
SCLK: J1.7, J5.4, J7.3, J11.7, R11.2
SCLK_UC: R11.1, U4.15 (PA5)
SWDCLK: J4.4, U4.37 (PA14)
SWDIO: J4.3, U4.34 (PA13)
VDD: C1.1, C9.1, C26.1, U1.1 (~SLEEP), U2.5 (OUT), U4.1 (VBAT), U4.9 (VDDA), U4.24 (VDD), U4.36 (VDD), U4.48 (VDD)

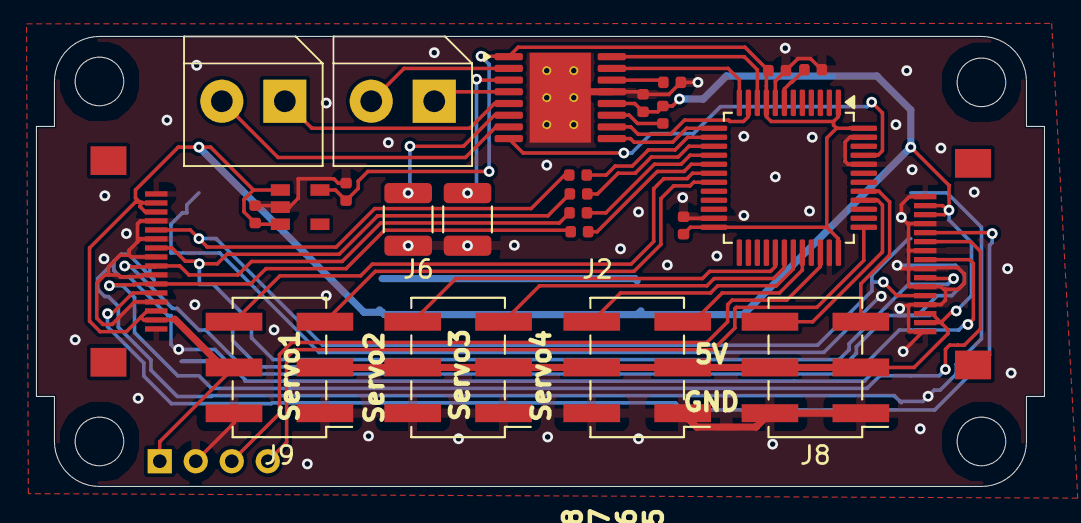
[picture p36: board Motor.kicad_pcb from above]

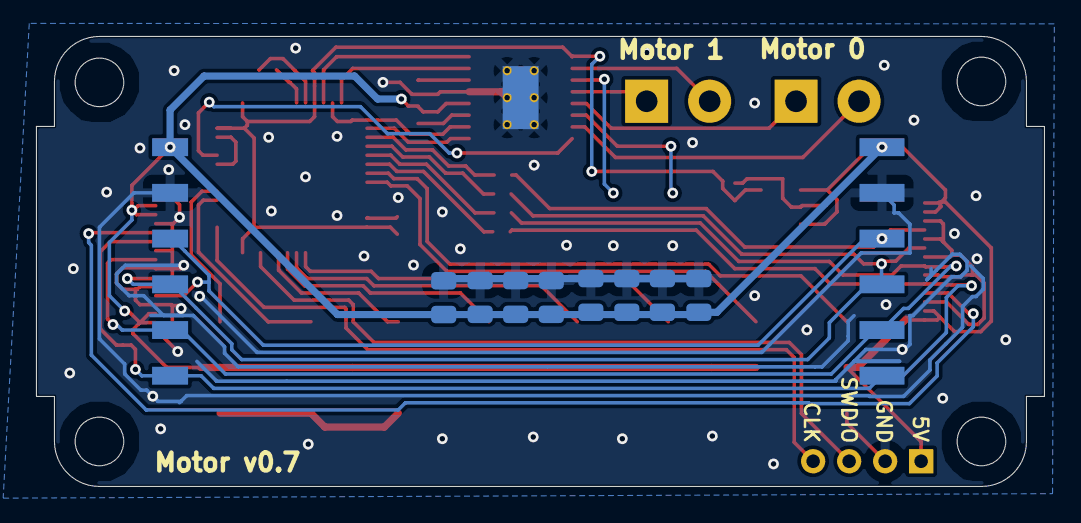
[picture p37: board Motor.kicad_pcb from below]

Board: 2 copper layers, 56.0 x 25.0 mm, 54 parts (21 on the bottom side), 36 nets.
