sean618/MakerTiles/hardware/Boards/Sense/v0.7/LightSound.kicad_pcb

## KiCad design hardware/Boards/Sense/v0.7/LightSound.kicad_pcb (2026-06-21, an earlier design)

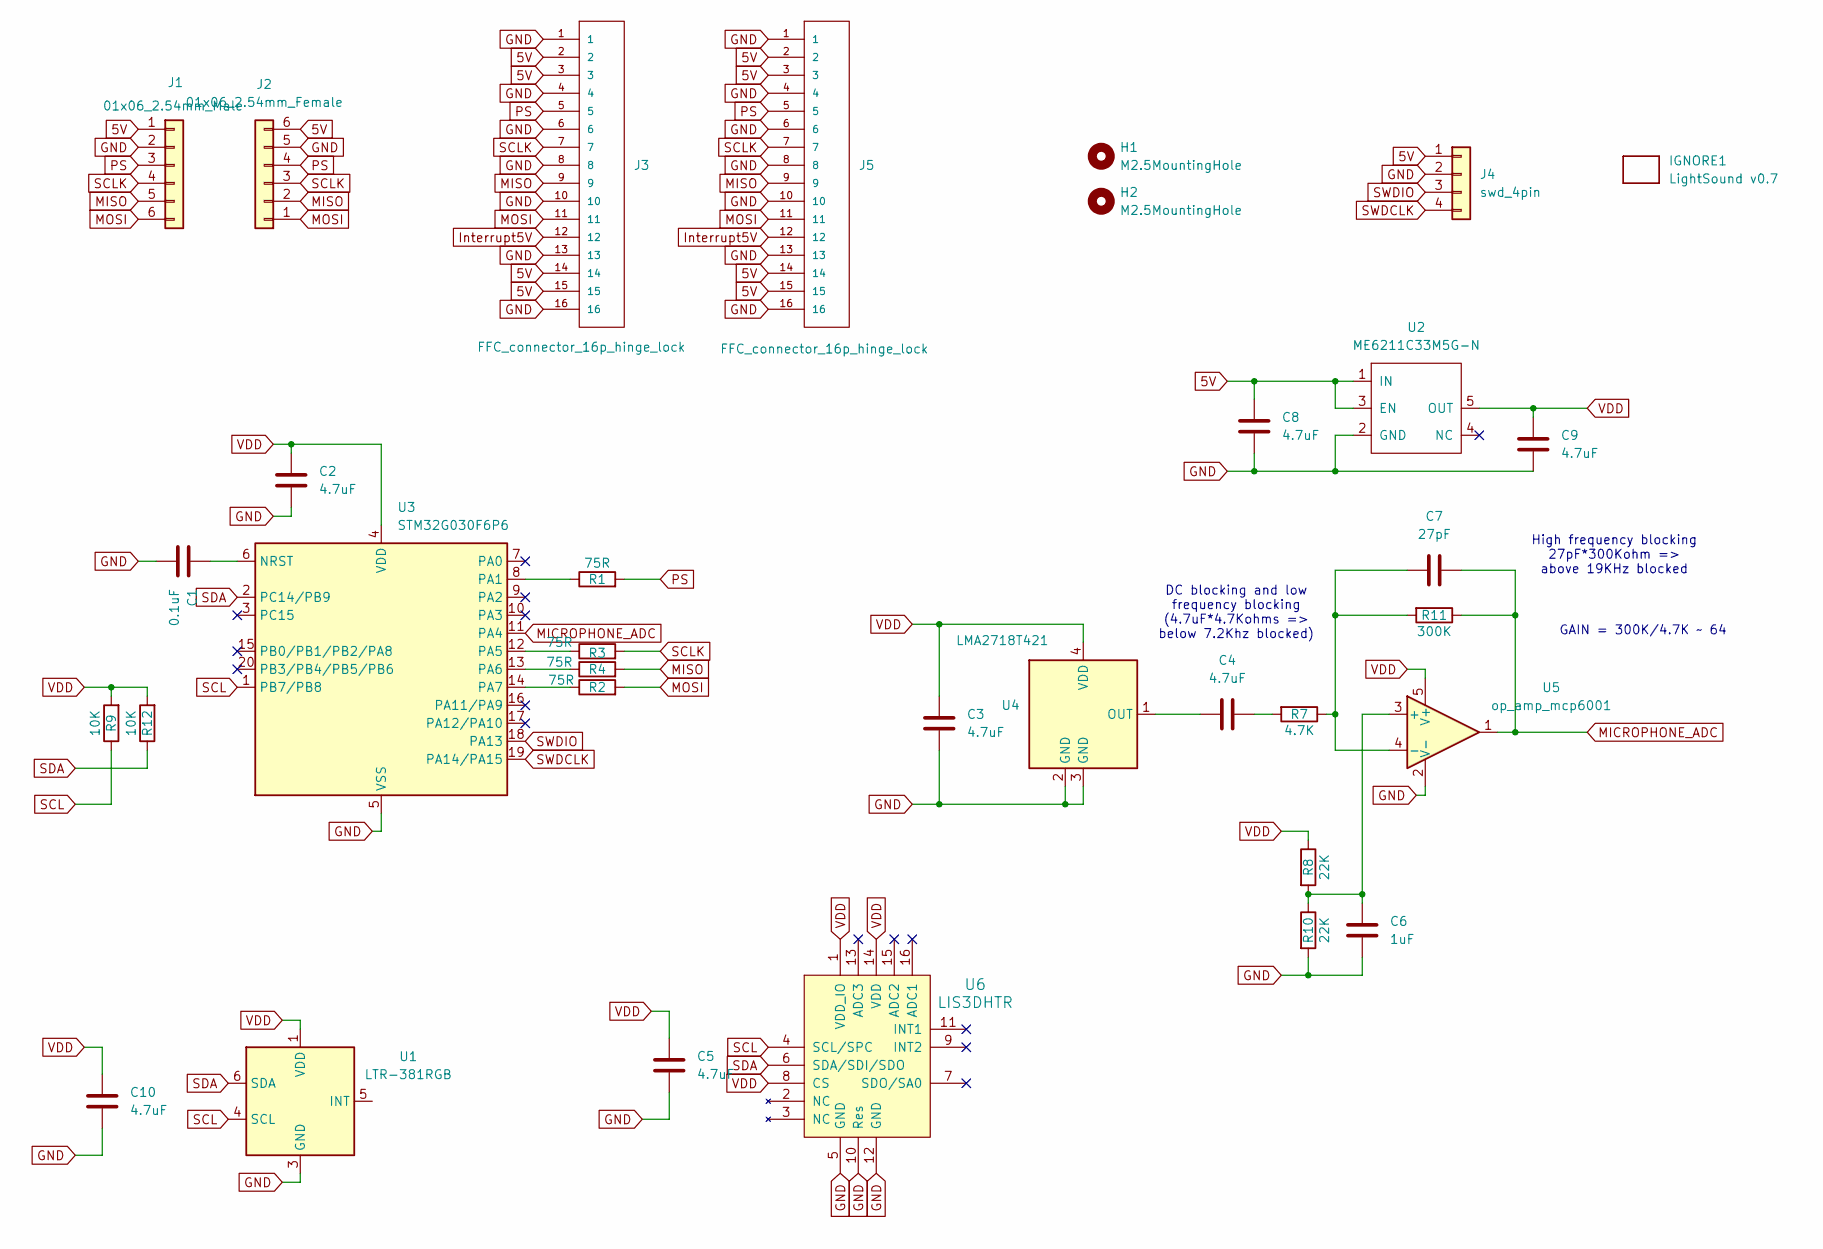
[picture p38: schematic LightSound.kicad_sch]

Parts:
C1: 0.1uF; C_0402_1005Metric
C2, C3, C4, C5, C8, C9, C10: 4.7uF; C_0402_1005Metric
C6: 1uF; C_0402_1005Metric
C7: 27pF; C_0402_1005Metric
H1, H2: M2.5MountingHole; MountingHole_2.7mm_M2.5_ISO7380
IGNORE1: LightSound v0.7; BoardText
J1: 01x06_2.54mm_Male
J2: 01x06_2.54mm_Female
J3, J5: FFC_connector_16p_hinge_lock
J4: swd_4pin; swd_header
R1, R2, R3, R4: 75R; R_0402_1005Metric
R7: 4.7K; R_0402_1005Metric
R8, R10: 22K; R_0402_1005Metric
R9, R12: 10K; R_0402_1005Metric
R11: 300K; R_0402_1005Metric
U1: LTR-381RGB
U2: ME6211C33M5G-N; SOT-23-5
U3: STM32G030F6P6; TSSOP-20_4.4x6.5mm_P0.65mm
U4: LMA2718T421; SMD-4P-2.8x1.9mm
U5: op_amp_mcp6001; SOT-23-5
U6: LIS3DHTR; LGA-16_3x3mm_P0.5mm_LayoutBorder3x5y; Manufacturer_Part_Number LIS3DHTR

Connections:
5V: C8.1, J1.1, J2.6, J3.2, J3.3, J3.14, J3.15, J4.1, J5.2, J5.3, J5.14, J5.15, U2.1 (IN), U2.3 (EN)
GND: C1.2, C2.2, C3.2, C5.2, C6.1, C8.2, C9.2, C10.2, J1.2, J2.5, J3.1, J3.4, J3.6, J3.8, J3.10, J3.13, J3.16, J4.2, J5.1, J5.4, J5.6, J5.8, J5.10, J5.13, J5.16, R10.2, U1.3 (GND), U2.2 (GND), U3.5 (VSS), U4.2 (GND), U4.3 (GND), U5.2 (V-), U6.5 (GND), U6.10 (Res), U6.12 (GND)
Interrupt5V: J3.12, J5.12
MICROPHONE_ADC: C7.2, R11.1, U3.11 (PA4), U5.1
MISO: J1.5, J2.2, J3.9, J5.9, R4.2
MOSI: J1.6, J2.1, J3.11, J5.11, R2.2
unnamed: C4.2, R7.2
unnamed: C1.1, U3.6 (NRST)
unnamed: R1.1, U3.8 (PA1)
unnamed: R3.1, U3.12 (PA5)
unnamed: R4.1, U3.13 (PA6)
unnamed: R2.1, U3.14 (PA7)
unnamed: C4.1, U4.1 (OUT)
unnamed: C6.2, R8.2, R10.1, U5.3 (+)
unnamed: C7.1, R7.1, R11.2, U5.4 (-)
PS: J1.3, J2.4, J3.5, J5.5, R1.2
SCL: R9.1, U1.4 (SCL), U3.1 (PB7/PB8), U6.4 (SCL/SPC)
SCLK: J1.4, J2.3, J3.7, J5.7, R3.2
SDA: R12.1, U1.6 (SDA), U3.2 (PC14/PB9), U6.6 (SDA/SDI/SDO)
SWDCLK: J4.4, U3.19 (PA14/PA15)
SWDIO: J4.3, U3.18 (PA13)
VDD: C2.1, C3.1, C5.1, C9.1, C10.1, R8.1, R9.2, R12.2, U1.1 (VDD), U2.5 (OUT), U3.4 (VDD), U4.4 (VDD), U5.5 (V+), U6.1 (VDD_IO), U6.8 (CS), U6.14 (VDD)

Notes on the sheet:
GAIN = 300K/4.7K ~ 64
High frequency blocking 27pF*300Kohm => above 19KHz blocked
DC blocking and low frequency blocking (4.7uF*4.7Kohms => below 7.2Khz blocked)

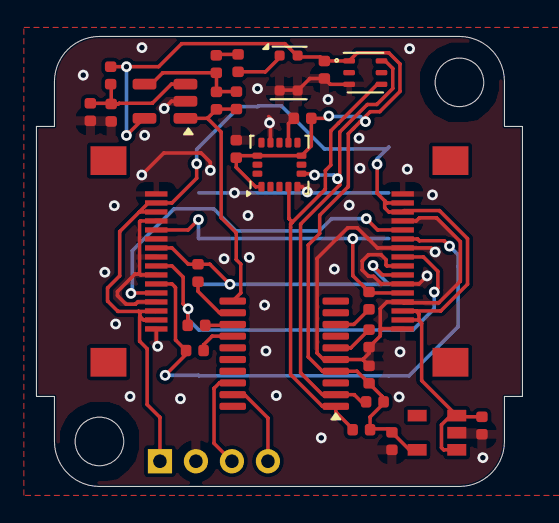
[picture p39: board LightSound.kicad_pcb from above]

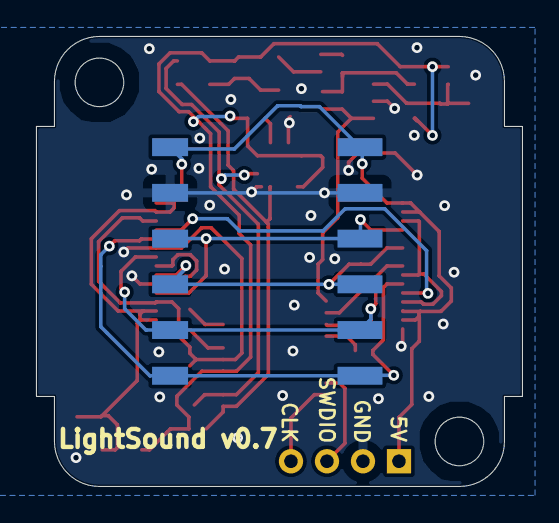
[picture p40: board LightSound.kicad_pcb from below]

Board: 2 copper layers, 27.0 x 25.0 mm, 34 parts (2 on the bottom side), 22 nets.
