sean618/MakerTiles/hardware/Boards/Extra/Wireless/v0.2 (Copy)/Wireless.kicad_pcb

## KiCad design hardware/Boards/Extra/Wireless/v0.2 (Copy)/Wireless.kicad_pcb (2026-06-21)

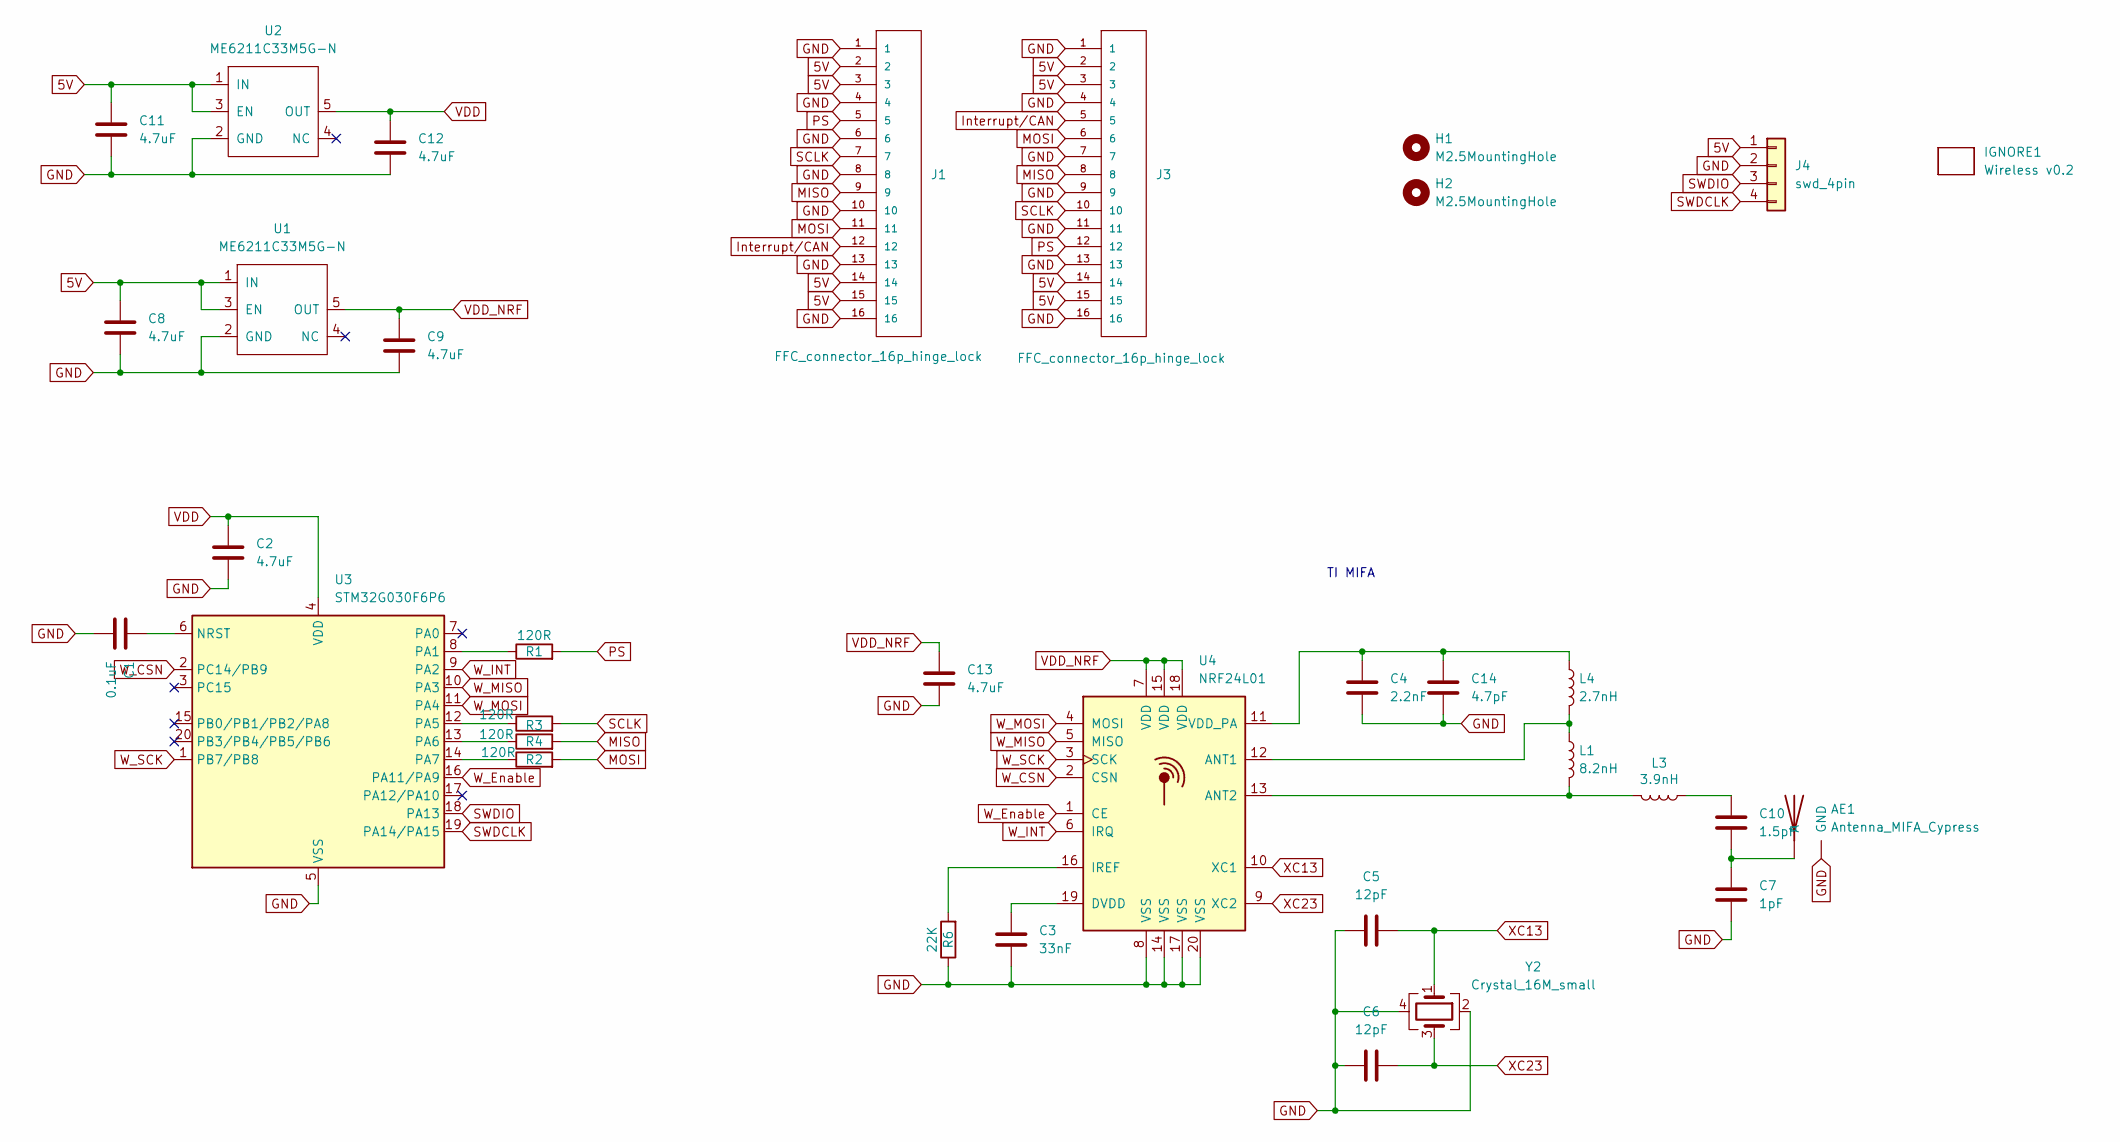
[picture p41: schematic Wireless.kicad_sch]

Parts:
AE1: Antenna_MIFA_Cypress; Antenna_cypress_MIFA
C1: 0.1uF; C_0402_1005Metric
C2, C8, C9, C11, C12, C13: 4.7uF; C_0402_1005Metric
C3: 33nF; C_0402_1005Metric
C4: 2.2nF; C_0402_1005Metric
C5, C6: 12pF; C_0402_1005Metric
C7: 1pF; C_0402_1005Metric
C10: 1.5pF; C_0402_1005Metric
C14: 4.7pF; C_0402_1005Metric
H1, H2: M2.5MountingHole; MountingHole_2.7mm_M2.5_ISO7380
IGNORE1: Wireless v0.2; BoardText
J1, J3: FFC_connector_16p_hinge_lock
J4: swd_4pin; swd_header
L1: 8.2nH; C_0402_1005Metric
L3: 3.9nH; C_0402_1005Metric
L4: 2.7nH; C_0402_1005Metric
R1, R2, R3, R4: 120R; R_0402_1005Metric
R6: 22K; R_0402_1005Metric
U1, U2: ME6211C33M5G-N; SOT-23-5
U3: STM32G030F6P6; TSSOP-20_4.4x6.5mm_P0.65mm
U4: NRF24L01; QFN-20-1EP_4x4mm_P0.5mm_EP2.5x2.5mm
Y2: Crystal_16M_small; Crystal_SMD_2016-4Pin_2.0x1.6mm

Connections:
5V: C8.1, C11.1, J1.2, J1.3, J1.14, J1.15, J3.2, J3.3, J3.14, J3.15, J4.1, U1.1 (IN), U1.3 (EN), U2.1 (IN), U2.3 (EN)
GND: AE1.2 (GND), C1.2, C2.2, C3.2, C4.2, C5.2, C6.2, C7.2, C8.2, C9.2, C11.2, C12.2, C13.2, C14.2, J1.1, J1.4, J1.6, J1.8, J1.10, J1.13, J1.16, J3.1, J3.4, J3.7, J3.9, J3.11, J3.13, J3.16, J4.2, R6.1, U1.2 (GND), U2.2 (GND), U3.5 (VSS), U4.8 (VSS), U4.14 (VSS), U4.17 (VSS), U4.20 (VSS), U4.21 (VSS), Y2.2 (GND), Y2.4 (GND)
MISO: J1.9, J3.8, R4.2
MOSI: J1.11, J3.6, R2.2
unnamed: AE1.1 (A), C7.1, C10.2
unnamed: C10.1, L3.1
unnamed: J1.12, J3.5
unnamed: C1.1, U3.6 (NRST)
unnamed: R1.1, U3.8 (PA1)
unnamed: R3.1, U3.12 (PA5)
unnamed: R4.1, U3.13 (PA6)
unnamed: R2.1, U3.14 (PA7)
unnamed: L1.1, L4.2, U4.12 (ANT1)
unnamed: L1.2, L3.2, U4.13 (ANT2)
unnamed: C3.1, U4.19 (DVDD)
unnamed: R6.2, U4.16 (IREF)
unnamed: C4.1, C14.1, L4.1, U4.11 (VDD_PA)
PS: J1.5, J3.12, R1.2
SCLK: J1.7, J3.10, R3.2
SWDCLK: J4.4, U3.19 (PA14/PA15)
SWDIO: J4.3, U3.18 (PA13)
VDD: C2.1, C12.1, U2.5 (OUT), U3.4 (VDD)
VDD_NRF: C9.1, C13.1, U1.5 (OUT), U4.7 (VDD), U4.15 (VDD), U4.18 (VDD)
W_CSN: U3.2 (PC14/PB9), U4.2 (CSN)
W_Enable: U3.16 (PA11/PA9), U4.1 (CE)
W_INT: U3.9 (PA2), U4.6 (IRQ)
W_MISO: U3.10 (PA3), U4.5 (MISO)
W_MOSI: U3.11 (PA4), U4.4 (MOSI)
W_SCK: U3.1 (PB7/PB8), U4.3 (SCK)
XC13: C5.1, U4.10 (XC1), Y2.1
XC23: C6.1, U4.9 (XC2), Y2.3

Notes on the sheet:
TI MIFA

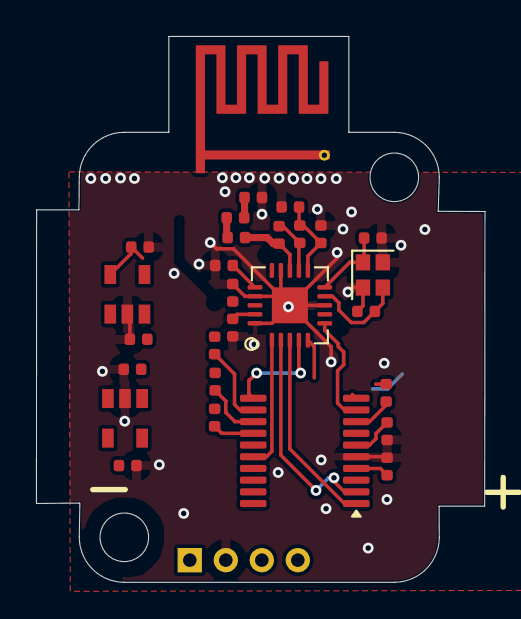
[picture p42: board Wireless.kicad_pcb from above]

Board: 4 copper layers, 24.9 x 30.3 mm, 32 parts (0 on the bottom side), 26 nets.
