sean618/MakerTiles/hardware/Boards/Battery/v0.10/Battery.kicad_pcb

## KiCad design hardware/Boards/Battery/v0.10/Battery.kicad_pcb (2026-06-21)

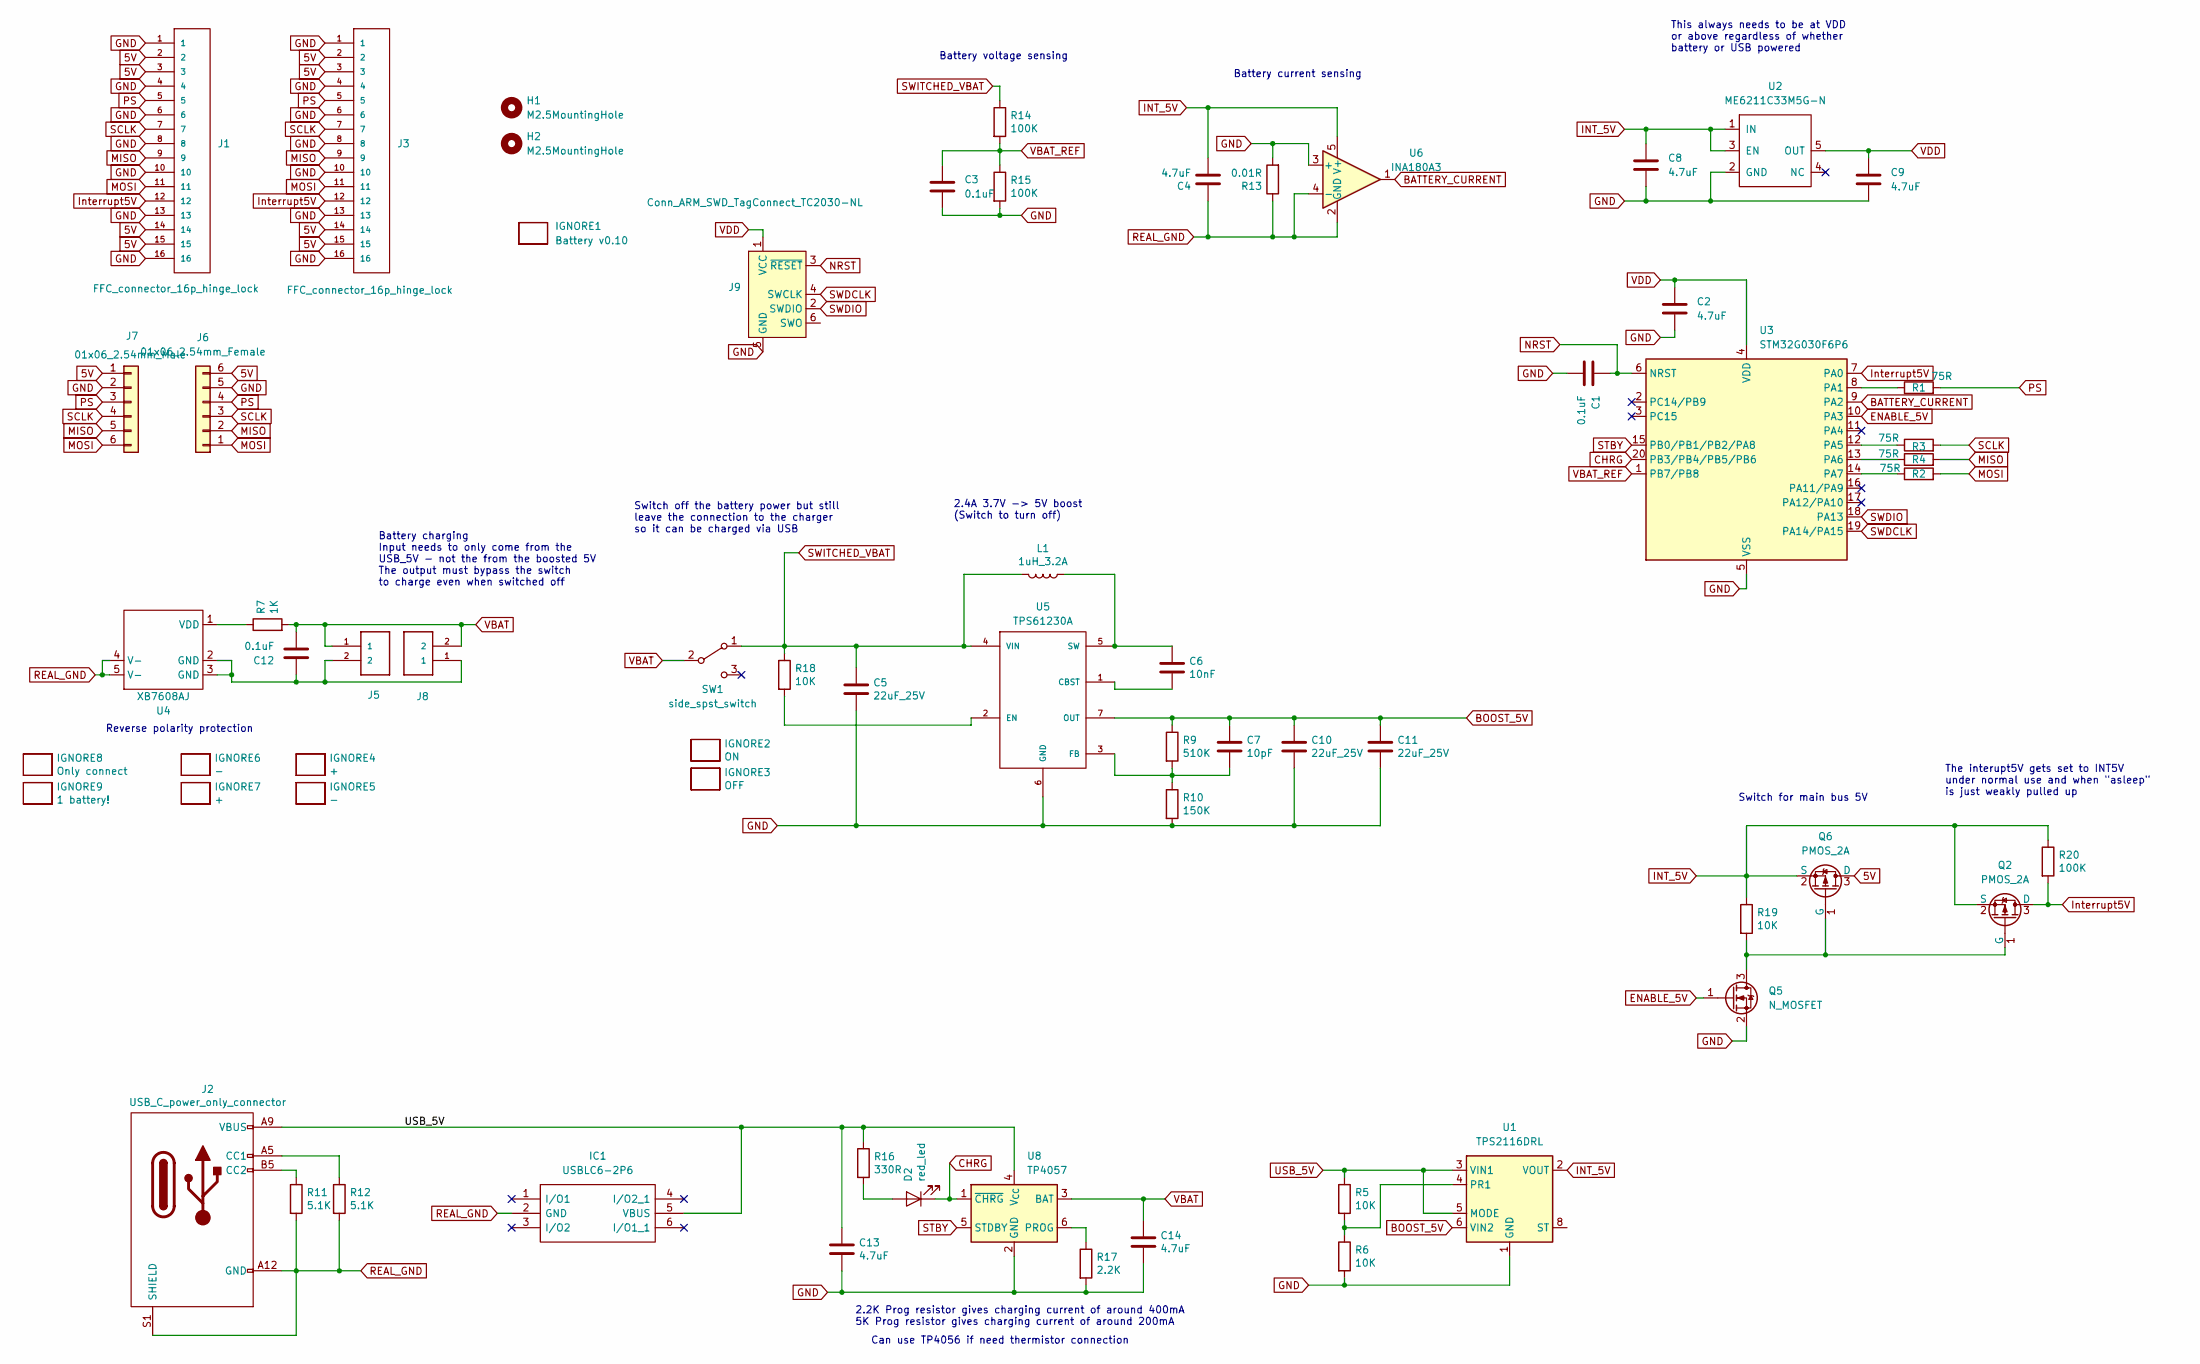
[picture p43: schematic Battery.kicad_sch]

Parts:
C1, C3, C12: 0.1uF; C_0402_1005Metric
C2, C4, C8, C9, C13, C14: 4.7uF; C_0402_1005Metric
C5, C10, C11: 22uF_25V; C_0805_2012Metric
C6: 10nF; C_0402_1005Metric
C7: 10pF; C_0402_1005Metric
D2: red_led; LED_SML-D12D1WT86; Manufacturer_Part_Number SML-D12D1WT86
H1, H2: M2.5MountingHole; MountingHole_2.7mm_M2.5_ISO7380
IC1: USBLC6-2P6; Manufacturer_Part_Number USBLC6-2P6
IGNORE1: Battery v0.10; BoardText
IGNORE2: ON; BoardText
IGNORE3: OFF; BoardText
IGNORE4, IGNORE7: +; BoardText
IGNORE5, IGNORE6: -; BoardText
IGNORE8: Only connect; BoardText
IGNORE9: 1 battery!; BoardText
J1, J3: FFC_connector_16p_hinge_lock
J2: USB_C_power_only_connector; USB_C_Receptacle_power_only_6P
J5, J8: ConnBattery_JST_S2B-PH-K-S; JST_PH_S2B-PH-K_1x02_P2.00mm_Horizontal; Manufacturer_Part_Number S2B-PH-K-S
J6: 01x06_2.54mm_Female
J7: 01x06_2.54mm_Male
J9: Conn_ARM_SWD_TagConnect_TC2030-NL; Tag-Connect_TC2030-IDC-NL_2x03_P1.27mm_Vertical
L1: 1uH_3.2A; L_1008_2520Metric
Q2, Q6: PMOS_2A; SOT-23
Q5: N_MOSFET; SOT-23
R1, R2, R3, R4: 75R; R_0402_1005Metric
R5, R6, R18, R19: 10K; R_0402_1005Metric
R7: 1K; R_0402_1005Metric
R9: 510K; R_0402_1005Metric
R10: 150K; R_0402_1005Metric
R11, R12: 5.1K; R_0402_1005Metric
R13: 0.01R; R_0805_2012Metric
R14, R15, R20: 100K; R_0402_1005Metric
R16: 330R; R_0402_1005Metric
R17: 2.2K; R_0402_1005Metric
SW1: side_spst_switch
U1: TPS2116DRL; SOT-583-8
U2: ME6211C33M5G-N; SOT-23-5
U3: STM32G030F6P6; TSSOP-20_4.4x6.5mm_P0.65mm
U4: XB7608AJ
U5: TPS61230A
U6: INA180A3; SOT-23-5
U8: TP4057; SOT-23-6

Connections:
5V: J1.2, J1.3, J1.14, J1.15, J3.2, J3.3, J3.14, J3.15, J6.6, J7.1, Q6.3 (D)
BATTERY_CURRENT: U3.9 (PA2), U6.1
BOOST_5V: C7.1, C10.1, C11.1, R9.1, U1.6 (VIN2), U5.7 (OUT)
CHRG: D2.1 (K), U3.20 (PB3/PB4/PB5/PB6), U8.1 (~CHRG)
ENABLE_5V: Q5.1 (G), U3.10 (PA3)
GND: C1.2, C2.2, C3.2, C5.2, C8.2, C9.2, C10.2, C11.2, C13.2, C14.2, J1.1, J1.4, J1.6, J1.8, J1.10, J1.13, J1.16, J3.1, J3.4, J3.6, J3.8, J3.10, J3.13, J3.16, J6.5, J7.2, J9.5 (GND), Q5.2 (S), R6.2, R10.2, R13.2, R15.2, R17.2, U1.1 (GND), U2.2 (GND), U3.5 (VSS), U5.6 (GND), U6.3 (+), U8.2 (GND); also elsewhere on the board
INT_5V: C4.2, C8.1, Q2.2 (S), Q6.2 (S), R19.1, R20.1, U1.2 (VOUT), U1.7 (VOUT), U2.1 (IN), U2.3 (EN), U6.5 (V+); also elsewhere on the board
Interrupt5V: J1.12, J3.12, Q2.3 (D), R20.2, U3.7 (PA0)
MISO: J1.9, J3.9, J6.2, J7.5, R4.2
MOSI: J1.11, J3.11, J6.1, J7.6, R2.2
unnamed: C12.1, J5.2, J8.1, U4.2 (GND), U4.3 (GND)
unnamed: D2.2 (A), R16.2
unnamed: J2.A5 (CC1), R12.1
unnamed: J2.B5 (CC2), R11.1
unnamed: Q2.1 (G), Q5.3 (D), Q6.1 (G), R19.2
unnamed: R5.2, R6.1, U1.4 (PR1)
unnamed: C1.1, J9.3 (~RESET), U3.6 (NRST)
unnamed: R1.1, U3.8 (PA1)
unnamed: R3.1, U3.12 (PA5)
unnamed: R4.1, U3.13 (PA6)
unnamed: R2.1, U3.14 (PA7)
unnamed: R7.1, U4.1 (VDD)
unnamed: C6.2, U5.1 (CBST)
unnamed: R18.2, U5.2 (EN)
unnamed: C7.2, R9.2, R10.1, U5.3 (FB)
unnamed: C6.1, L1.1, U5.5 (SW)
unnamed: R17.1, U8.6 (PROG)
PS: J1.5, J3.5, J6.4, J7.3, R1.2
REAL_GND: C4.1, IC1.2 (GND), J2.A12 (GND), J2.B12 (GND), J2.S1 (SHIELD), R11.2, R12.2, R13.1, U4.4 (V-), U4.5 (V-), U6.2 (GND), U6.4 (-)
SCLK: J1.7, J3.7, J6.3, J7.4, R3.2
STBY: U3.15 (PB0/PB1/PB2/PA8), U8.5 (STDBY)
SWDCLK: J9.4 (SWCLK), U3.19 (PA14/PA15); also elsewhere on the board
SWDIO: J9.2 (SWDIO), U3.18 (PA13); also elsewhere on the board
SWITCHED_VBAT: C5.1, L1.2, R14.1, R18.1, SW1.1 (A), U5.4 (VIN)
USB_5V: C13.1, IC1.5 (VBUS), J2.A9 (VBUS), J2.B9 (VBUS), R5.1, R16.1, U1.3 (VIN1), U1.5 (MODE), U8.4 (V_{CC})
VBAT: C12.2, C14.1, J5.1, J8.2, R7.2, SW1.2 (B), U8.3 (BAT)
VBAT_REF: C3.1, R14.2, R15.1, U3.1 (PB7/PB8)
VDD: C2.1, C9.1, J9.1 (VCC), U2.5 (OUT), U3.4 (VDD)

Notes on the sheet:
Battery current sensing
This always needs to be at VDD or above regardless of whether battery or USB powered
Switch for main bus 5V
Can use TP4056 if need thermistor connection
Battery charging Input needs to only come from the USB_5V - not the from the boosted 5V The output must bypass the switch to charge even when switched off
Switch off the battery power but still leave the connection to the charger so it can be charged via USB
Battery voltage sensing
The interupt5V gets set to INT5V under normal use and when "asleep" is just weakly pulled up
2.2K Prog resistor gives charging current of around 400mA 5K Prog resistor gives charging current of around 200mA
Reverse polarity protection
2.4A 3.7V -> 5V boost (Switch to turn off)

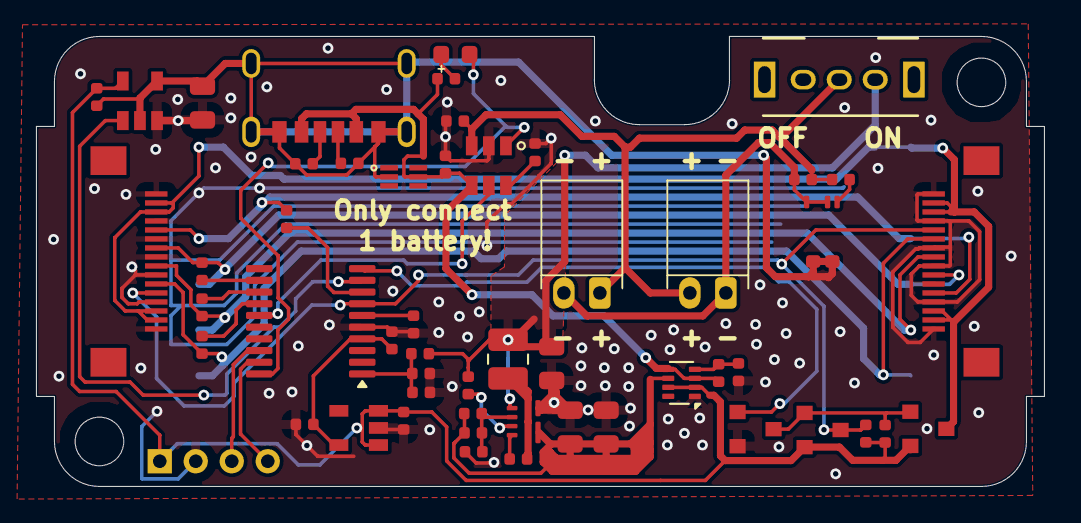
[picture p44: board Battery.kicad_pcb from above]

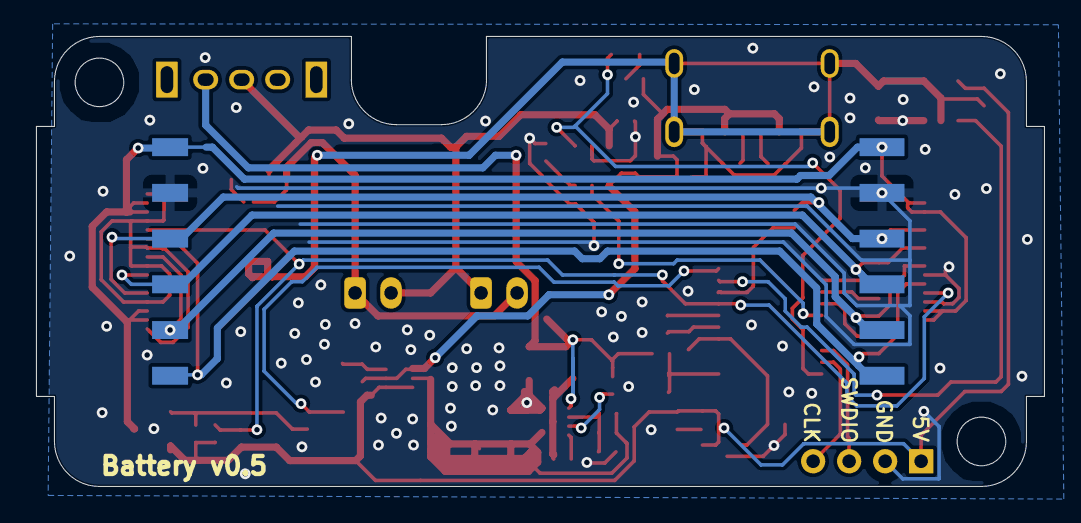
[picture p45: board Battery.kicad_pcb from below]

Board: 2 copper layers, 56.0 x 25.0 mm, 71 parts (15 on the bottom side), 38 nets.

Other parts of the board:
IGNORE4#2, IGNORE7#2: +; BoardText
IGNORE5#2, IGNORE5#3, IGNORE6#2: -; BoardText
J4: swd_4pin; swd_header

Their connections:
GND: J4.2; also elsewhere on the board
INT_5V: J4.1; also elsewhere on the board
SWDCLK: J4.4; also elsewhere on the board
SWDIO: J4.3; also elsewhere on the board
