sean618/MakerTiles/hardware/Boards/Extra/ButtonExpansion/v0.5/ButtonExpansion.kicad_pcb

## KiCad design hardware/Boards/Extra/ButtonExpansion/v0.5/ButtonExpansion.kicad_pcb (2026-06-21)

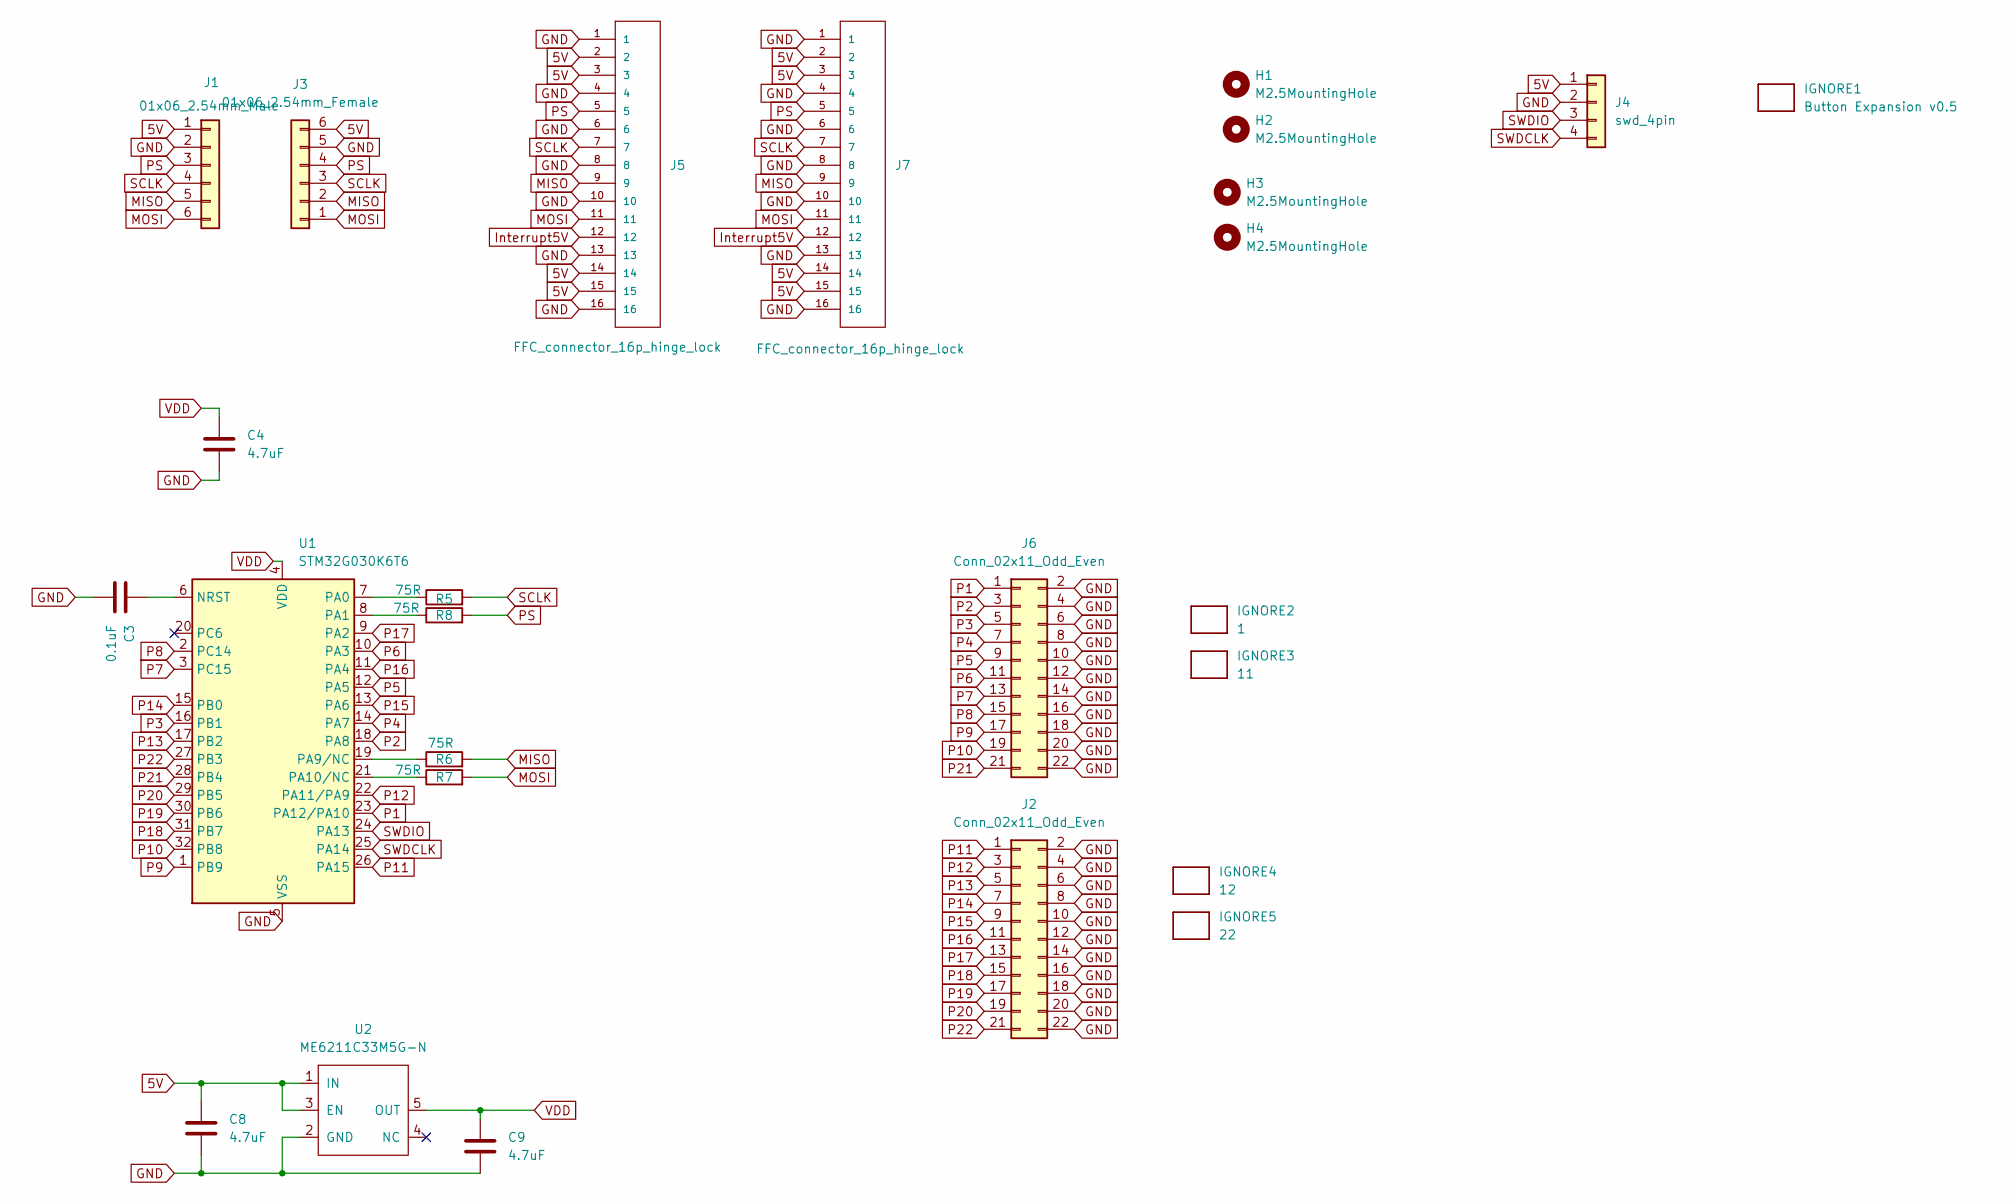
[picture p46: schematic ButtonExpansion.kicad_sch]

Parts:
C3: 0.1uF; C_0402_1005Metric
C4, C8, C9: 4.7uF; C_0402_1005Metric
H1, H2, H3, H4: M2.5MountingHole; MountingHole_2.7mm_M2.5_ISO7380
IGNORE1: Button Expansion v0.5; BoardText
IGNORE2: 1; BoardText
IGNORE3: 11; BoardText
IGNORE4: 12; BoardText
IGNORE5: 22; BoardText
J1: 01x06_2.54mm_Male
J2, J6: Conn_02x11_Odd_Even; PinHeader_2x11_P2.54mm_Vertical
J3: 01x06_2.54mm_Female
J4: swd_4pin; swd_header
J5, J7: FFC_connector_16p_hinge_lock
R5, R6, R7, R8: 75R; R_0402_1005Metric
U1: STM32G030K6T6; LQFP-32_7x7mm_P0.8mm
U2: ME6211C33M5G-N; SOT-23-5

Connections:
5V: C8.1, J1.1, J3.6, J4.1, J5.2, J5.3, J5.14, J5.15, J7.2, J7.3, J7.14, J7.15, U2.1 (IN), U2.3 (EN)
GND: C3.2, C4.2, C8.2, C9.2, J1.2, J2.2, J2.4, J2.6, J2.8, J2.10, J2.12, J2.14, J2.16, J2.18, J2.20, J2.22, J3.5, J4.2, J5.1, J5.4, J5.6, J5.8, J5.10, J5.13, J5.16, J6.2, J6.4, J6.6, J6.8, J6.10, J6.12, J6.14, J6.16, J6.18, J6.20, J6.22, J7.1, J7.4, J7.6, J7.8, J7.10, J7.13, J7.16, U1.5 (VSS), U2.2 (GND)
Interrupt5V: J5.12, J7.12
MISO: J1.5, J3.2, J5.9, J7.9, R6.2
MOSI: J1.6, J3.1, J5.11, J7.11, R7.2
unnamed: C3.1, U1.6 (NRST)
unnamed: R5.1, U1.7 (PA0)
unnamed: R8.1, U1.8 (PA1)
unnamed: R6.1, U1.19 (PA9/NC)
unnamed: R7.1, U1.21 (PA10/NC)
P1: J6.1, U1.23 (PA12/PA10)
P2: J6.3, U1.18 (PA8)
P3: J6.5, U1.16 (PB1)
P4: J6.7, U1.14 (PA7)
P5: J6.9, U1.12 (PA5)
P6: J6.11, U1.10 (PA3)
P7: J6.13, U1.3 (PC15)
P8: J6.15, U1.2 (PC14)
P9: J6.17, U1.1 (PB9)
P10: J6.19, U1.32 (PB8)
P11: J2.1, U1.26 (PA15)
P12: J2.3, U1.22 (PA11/PA9)
P13: J2.5, U1.17 (PB2)
P14: J2.7, U1.15 (PB0)
P15: J2.9, U1.13 (PA6)
P16: J2.11, U1.11 (PA4)
P17: J2.13, U1.9 (PA2)
P18: J2.15, U1.31 (PB7)
P19: J2.17, U1.30 (PB6)
P20: J2.19, U1.29 (PB5)
P21: J6.21, U1.28 (PB4)
P22: J2.21, U1.27 (PB3)
PS: J1.3, J3.4, J5.5, J7.5, R8.2
SCLK: J1.4, J3.3, J5.7, J7.7, R5.2
SWDCLK: J4.4, U1.25 (PA14)
SWDIO: J4.3, U1.24 (PA13)
VDD: C4.1, C9.1, U1.4 (VDD), U2.5 (OUT)

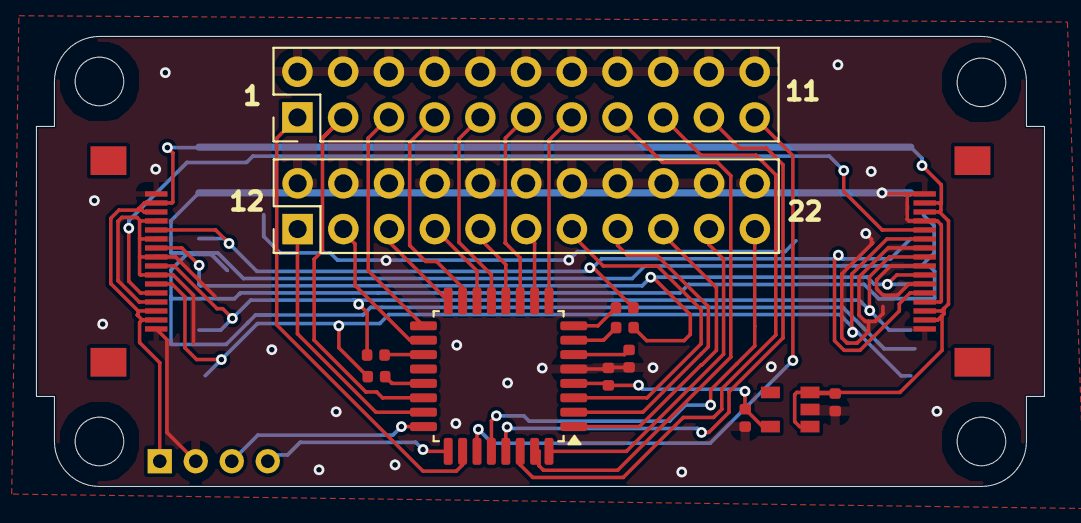
[picture p47: board ButtonExpansion.kicad_pcb from above]

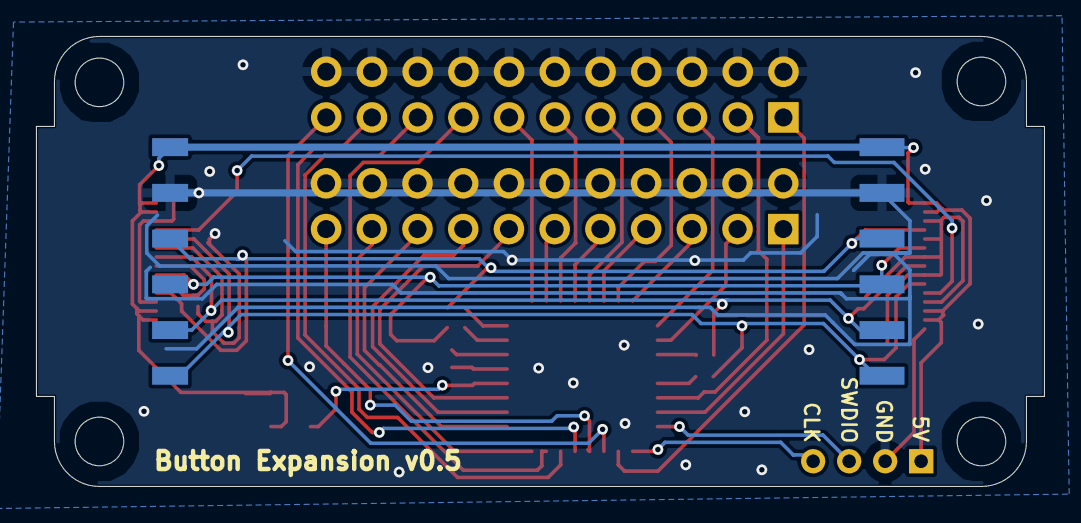
[picture p48: board ButtonExpansion.kicad_pcb from below]

Board: 2 copper layers, 56.0 x 25.0 mm, 26 parts (6 on the bottom side), 37 nets.
