sean618/MakerTiles/hardware/Boards/Joystick/v0.1/Joystick.kicad_pcb

## KiCad design hardware/Boards/Joystick/v0.1/Joystick.kicad_pcb (2026-06-21, an earlier design)

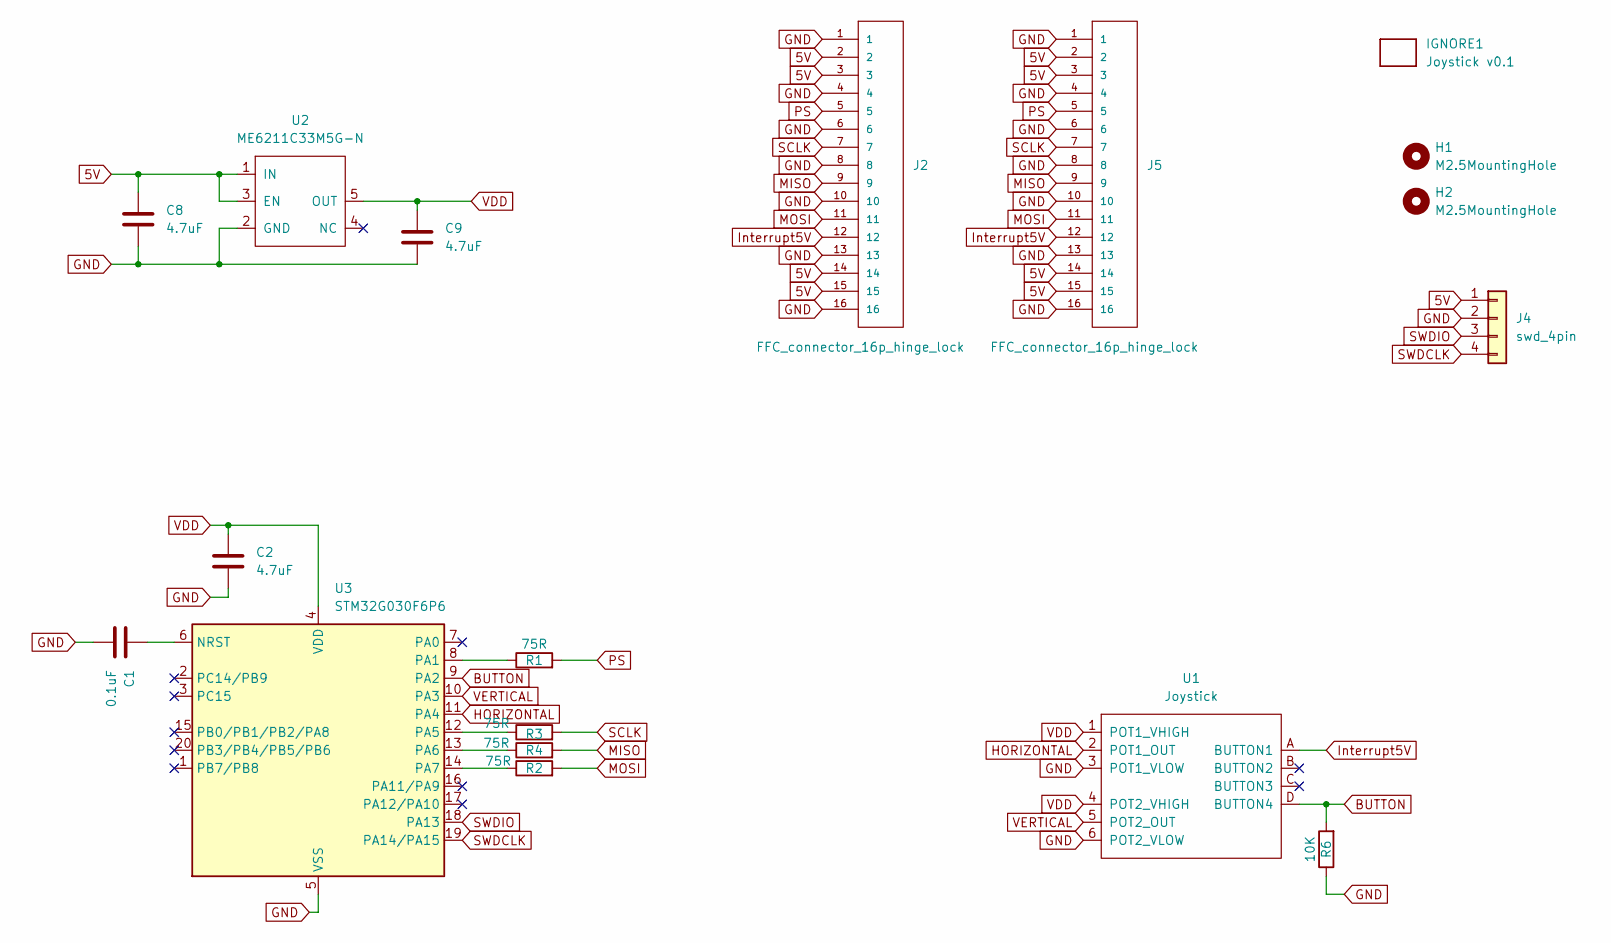
[picture p49: schematic Joystick.kicad_sch]

Parts:
C1: 0.1uF; C_0402_1005Metric
C2, C8, C9: 4.7uF; C_0402_1005Metric
H1, H2: M2.5MountingHole; MountingHole_2.7mm_M2.5_ISO7380
IGNORE1: Joystick v0.1; BoardText
J2, J5: FFC_connector_16p_hinge_lock
J4: swd_4pin; swd_header
R1, R2, R3, R4: 75R; R_0402_1005Metric
R6: 10K; R_0402_1005Metric
U1: Joystick
U2: ME6211C33M5G-N; SOT-23-5
U3: STM32G030F6P6; TSSOP-20_4.4x6.5mm_P0.65mm

Connections:
5V: C8.1, J2.2, J2.3, J2.14, J2.15, J4.1, J5.2, J5.3, J5.14, J5.15, U2.1 (IN), U2.3 (EN)
BUTTON: R6.2, U1.D (BUTTON4), U3.9 (PA2)
GND: C1.2, C2.2, C8.2, C9.2, J2.1, J2.4, J2.6, J2.8, J2.10, J2.13, J2.16, J4.2, J5.1, J5.4, J5.6, J5.8, J5.10, J5.13, J5.16, R6.1, U1.3 (POT1_VLOW), U1.6 (POT2_VLOW), U2.2 (GND), U3.5 (VSS)
HORIZONTAL: U1.2 (POT1_OUT), U3.11 (PA4)
Interrupt5V: J2.12, J5.12, U1.A (BUTTON1)
MISO: J2.9, J5.9, R4.2
MOSI: J2.11, J5.11, R2.2
unnamed: C1.1, U3.6 (NRST)
unnamed: R1.1, U3.8 (PA1)
unnamed: R3.1, U3.12 (PA5)
unnamed: R4.1, U3.13 (PA6)
unnamed: R2.1, U3.14 (PA7)
PS: J2.5, J5.5, R1.2
SCLK: J2.7, J5.7, R3.2
SWDCLK: J4.4, U3.19 (PA14/PA15)
SWDIO: J4.3, U3.18 (PA13)
VDD: C2.1, C9.1, U1.1 (POT1_VHIGH), U1.4 (POT2_VHIGH), U2.5 (OUT), U3.4 (VDD)
VERTICAL: U1.5 (POT2_OUT), U3.10 (PA3)

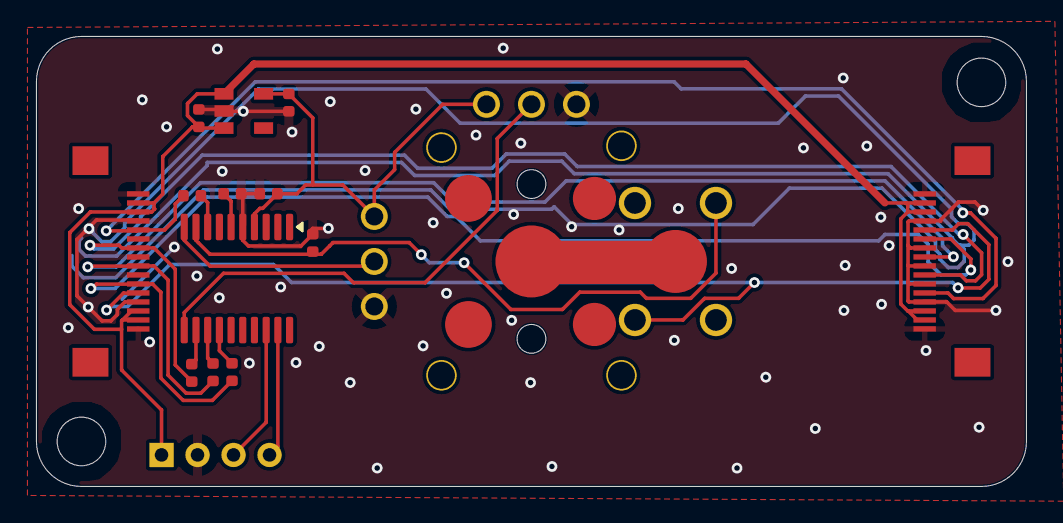
[picture p50: board Joystick.kicad_pcb from above]

Board: 2 copper layers, 55.0 x 25.0 mm, 18 parts (0 on the bottom side), 18 nets.
