sean618/MakerTiles/hardware/Boards/Extra/Servo/v0.5/Servo.kicad_pcb

## KiCad design hardware/Boards/Extra/Servo/v0.5/Servo.kicad_pcb (2026-06-21)

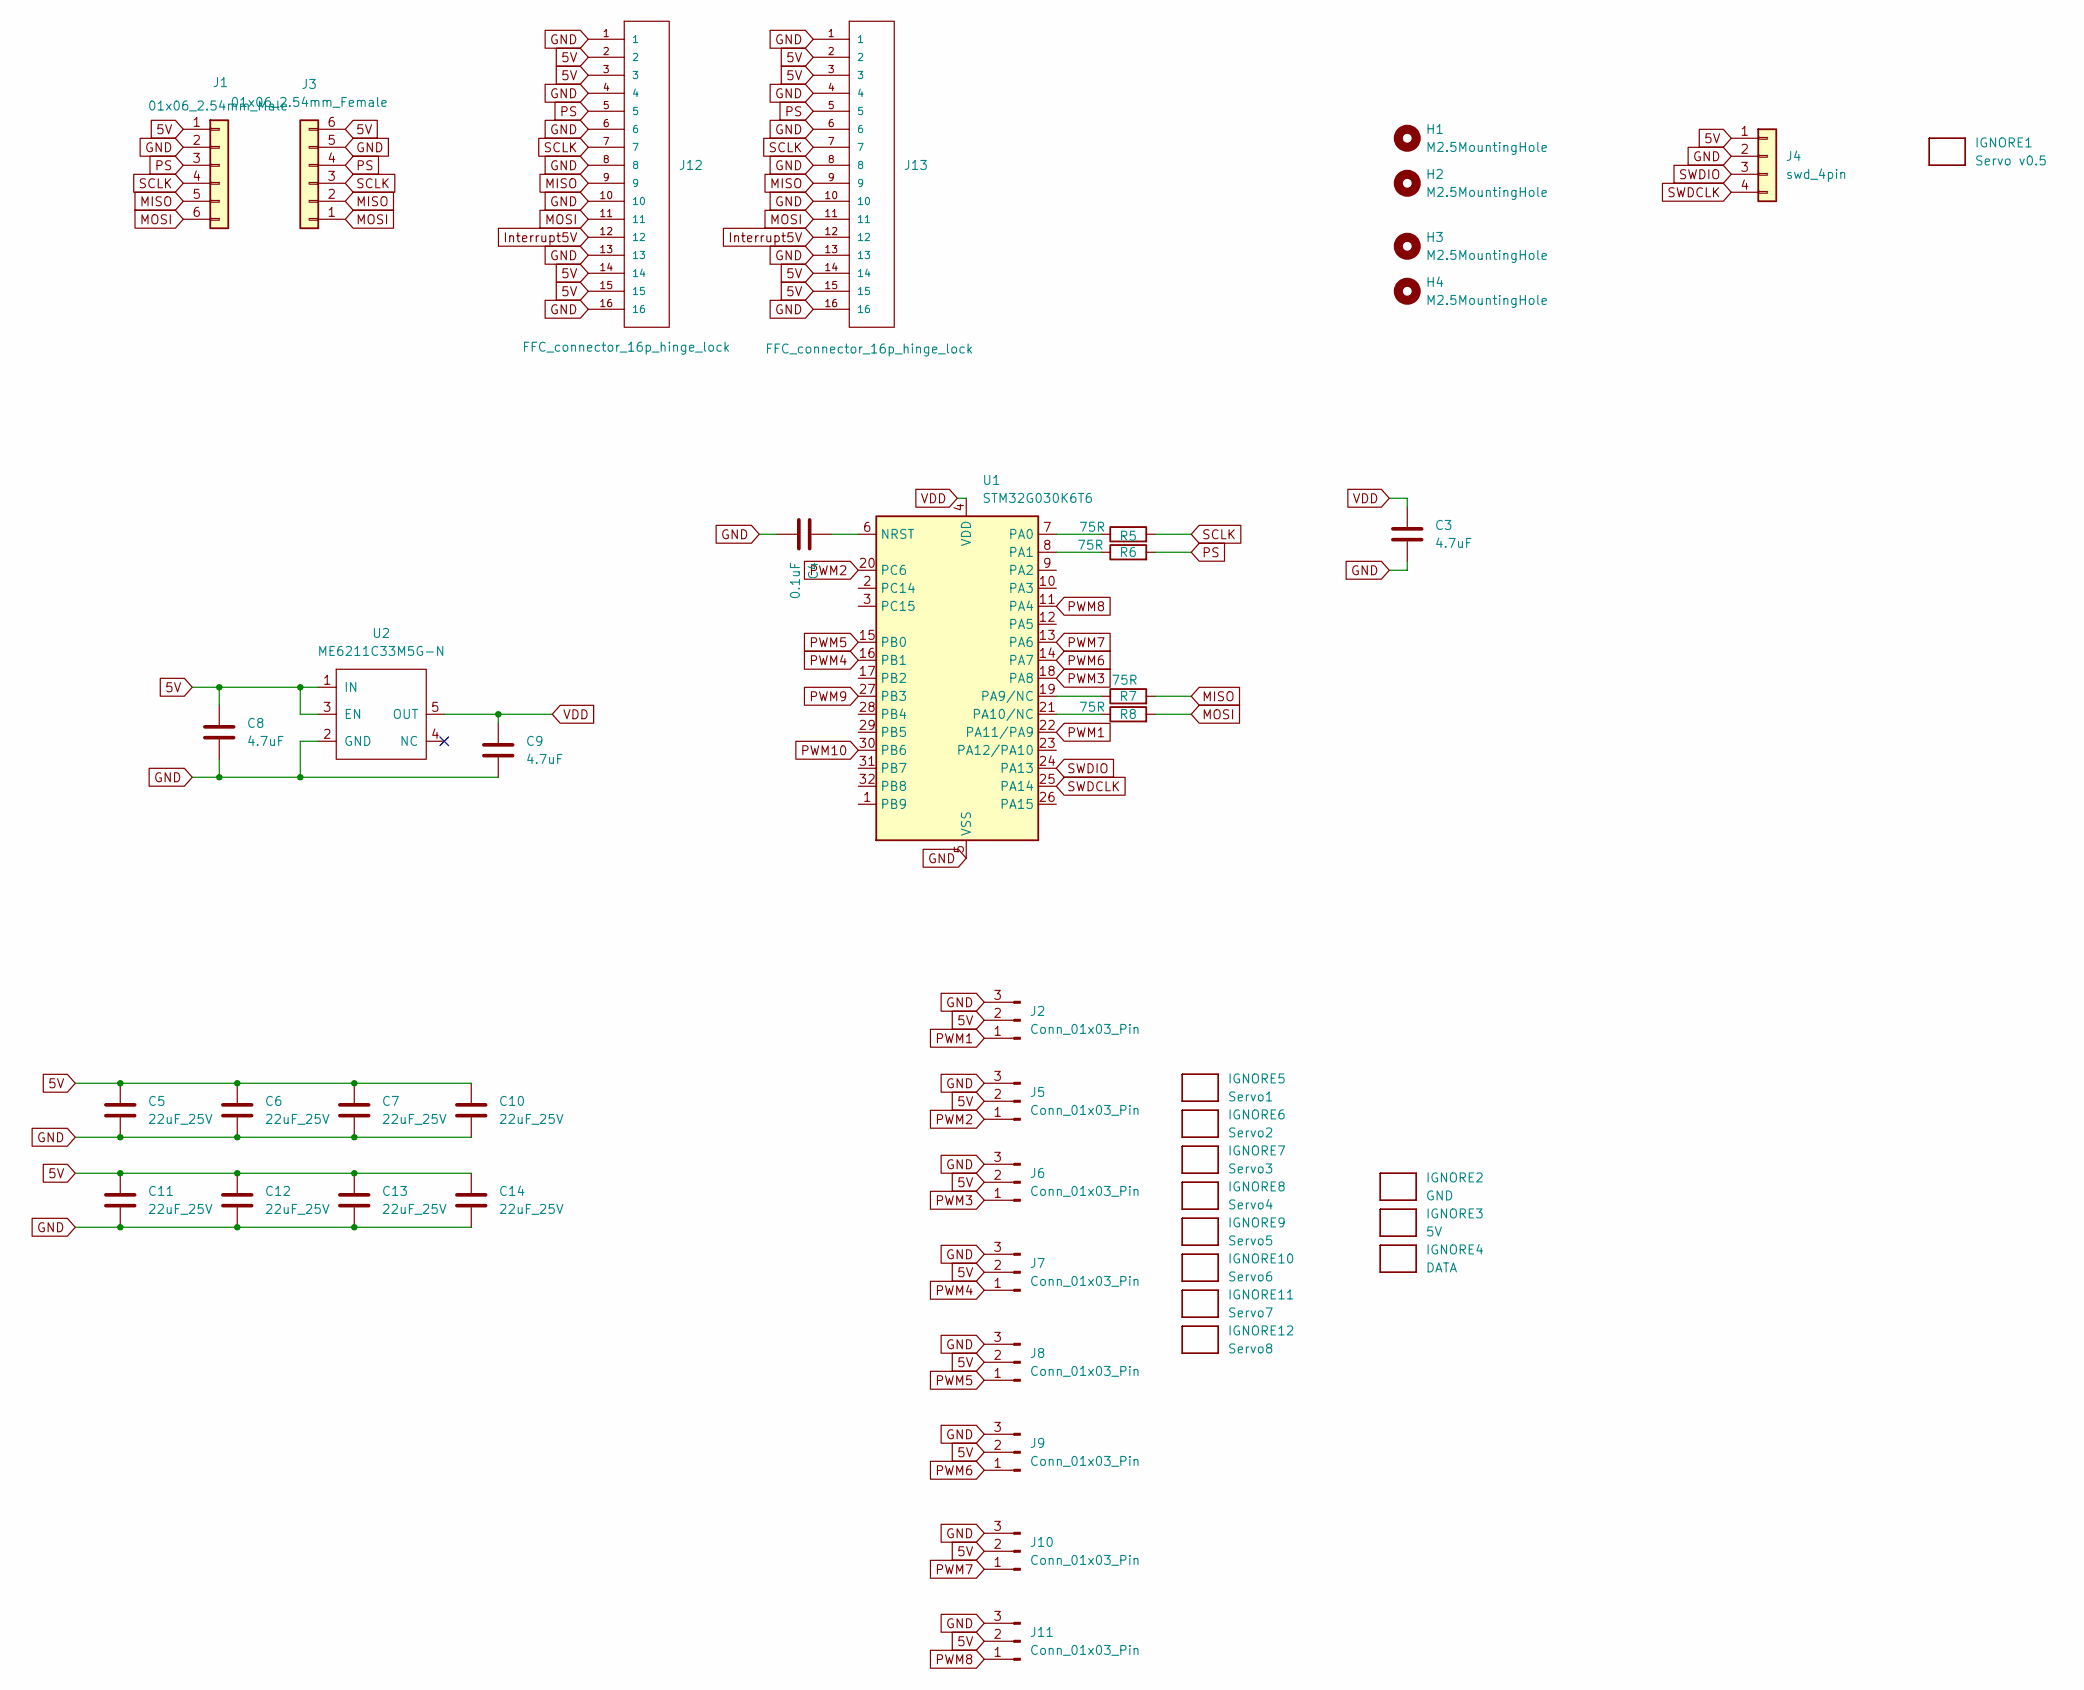
[picture p51: schematic Servo.kicad_sch]

Parts:
C3, C8, C9: 4.7uF; C_0402_1005Metric
C4: 0.1uF; C_0402_1005Metric
C5, C6, C7, C10, C11, C12, C13, C14: 22uF_25V; C_0805_2012Metric
H1, H2, H3, H4: M2.5MountingHole; MountingHole_2.7mm_M2.5_ISO7380
IGNORE1: Servo v0.5; BoardText
IGNORE2: GND; BoardText
IGNORE3: 5V; BoardText
IGNORE4: DATA; BoardText
IGNORE5: Servo1; BoardText
IGNORE6: Servo2; BoardText
IGNORE7: Servo3; BoardText
IGNORE8: Servo4; BoardText
IGNORE9: Servo5; BoardText
IGNORE10: Servo6; BoardText
IGNORE11: Servo7; BoardText
IGNORE12: Servo8; BoardText
J1: 01x06_2.54mm_Male
J2, J5, J6, J7, J8, J9, J10, J11: Conn_01x03_Pin; PinHeader_1x03_P2.54mm_Vertical
J3: 01x06_2.54mm_Female
J4: swd_4pin; swd_header
J12, J13: FFC_connector_16p_hinge_lock
R5, R6, R7, R8: 75R; R_0402_1005Metric
U1: STM32G030K6T6; LQFP-32_7x7mm_P0.8mm
U2: ME6211C33M5G-N; SOT-23-5

Connections:
5V: C5.1, C6.1, C7.1, C8.1, C10.1, C11.1, C12.1, C13.1, C14.1, J1.1, J2.2, J3.6, J4.1, J5.2, J6.2, J7.2, J8.2, J9.2, J10.2, J11.2, J12.2, J12.3, J12.14, J12.15, J13.2, J13.3, J13.14, J13.15, U2.1 (IN), U2.3 (EN)
GND: C3.2, C4.2, C5.2, C6.2, C7.2, C8.2, C9.2, C10.2, C11.2, C12.2, C13.2, C14.2, J1.2, J2.3, J3.5, J4.2, J5.3, J6.3, J7.3, J8.3, J9.3, J10.3, J11.3, J12.1, J12.4, J12.6, J12.8, J12.10, J12.13, J12.16, J13.1, J13.4, J13.6, J13.8, J13.10, J13.13, J13.16, U1.5 (VSS), U2.2 (GND)
Interrupt5V: J12.12, J13.12
MISO: J1.5, J3.2, J12.9, J13.9, R7.2
MOSI: J1.6, J3.1, J12.11, J13.11, R8.2
unnamed: C4.1, U1.6 (NRST)
unnamed: R5.1, U1.7 (PA0)
unnamed: R6.1, U1.8 (PA1)
unnamed: R7.1, U1.19 (PA9/NC)
unnamed: R8.1, U1.21 (PA10/NC)
PS: J1.3, J3.4, J12.5, J13.5, R6.2
PWM1: J2.1, U1.22 (PA11/PA9)
PWM2: J5.1, U1.20 (PC6)
PWM3: J6.1, U1.18 (PA8)
PWM4: J7.1, U1.16 (PB1)
PWM5: J8.1, U1.15 (PB0)
PWM6: J9.1, U1.14 (PA7)
PWM7: J10.1, U1.13 (PA6)
PWM8: J11.1, U1.11 (PA4)
PWM9: U1.27 (PB3)
PWM10: U1.30 (PB6)
SCLK: J1.4, J3.3, J12.7, J13.7, R5.2
SWDCLK: J4.4, U1.25 (PA14)
SWDIO: J4.3, U1.24 (PA13)
VDD: C3.1, C9.1, U1.4 (VDD), U2.5 (OUT)

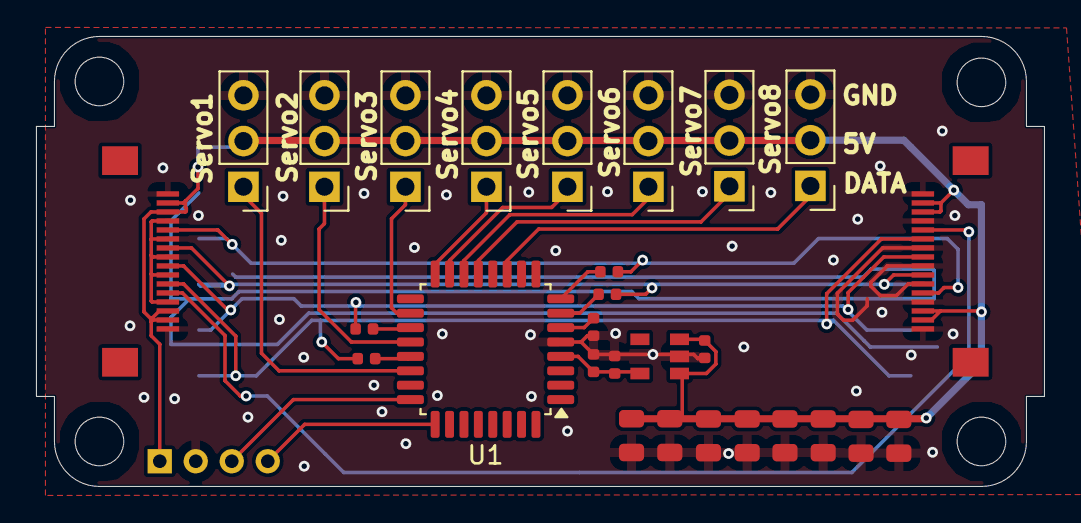
[picture p52: board Servo.kicad_pcb from above]

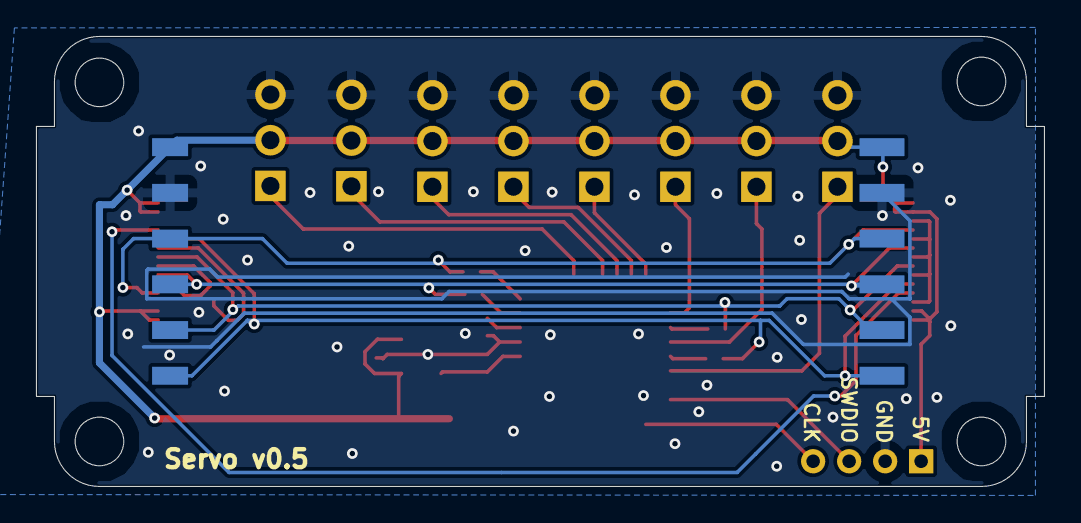
[picture p53: board Servo.kicad_pcb from below]

Board: 2 copper layers, 56.0 x 25.0 mm, 47 parts (13 on the bottom side), 23 nets.
