sean618/MakerTiles/hardware/Boards/Distance/v0.2/Distance.kicad_pcb

## KiCad design hardware/Boards/Distance/v0.2/Distance.kicad_pcb (2026-06-21, an earlier design)

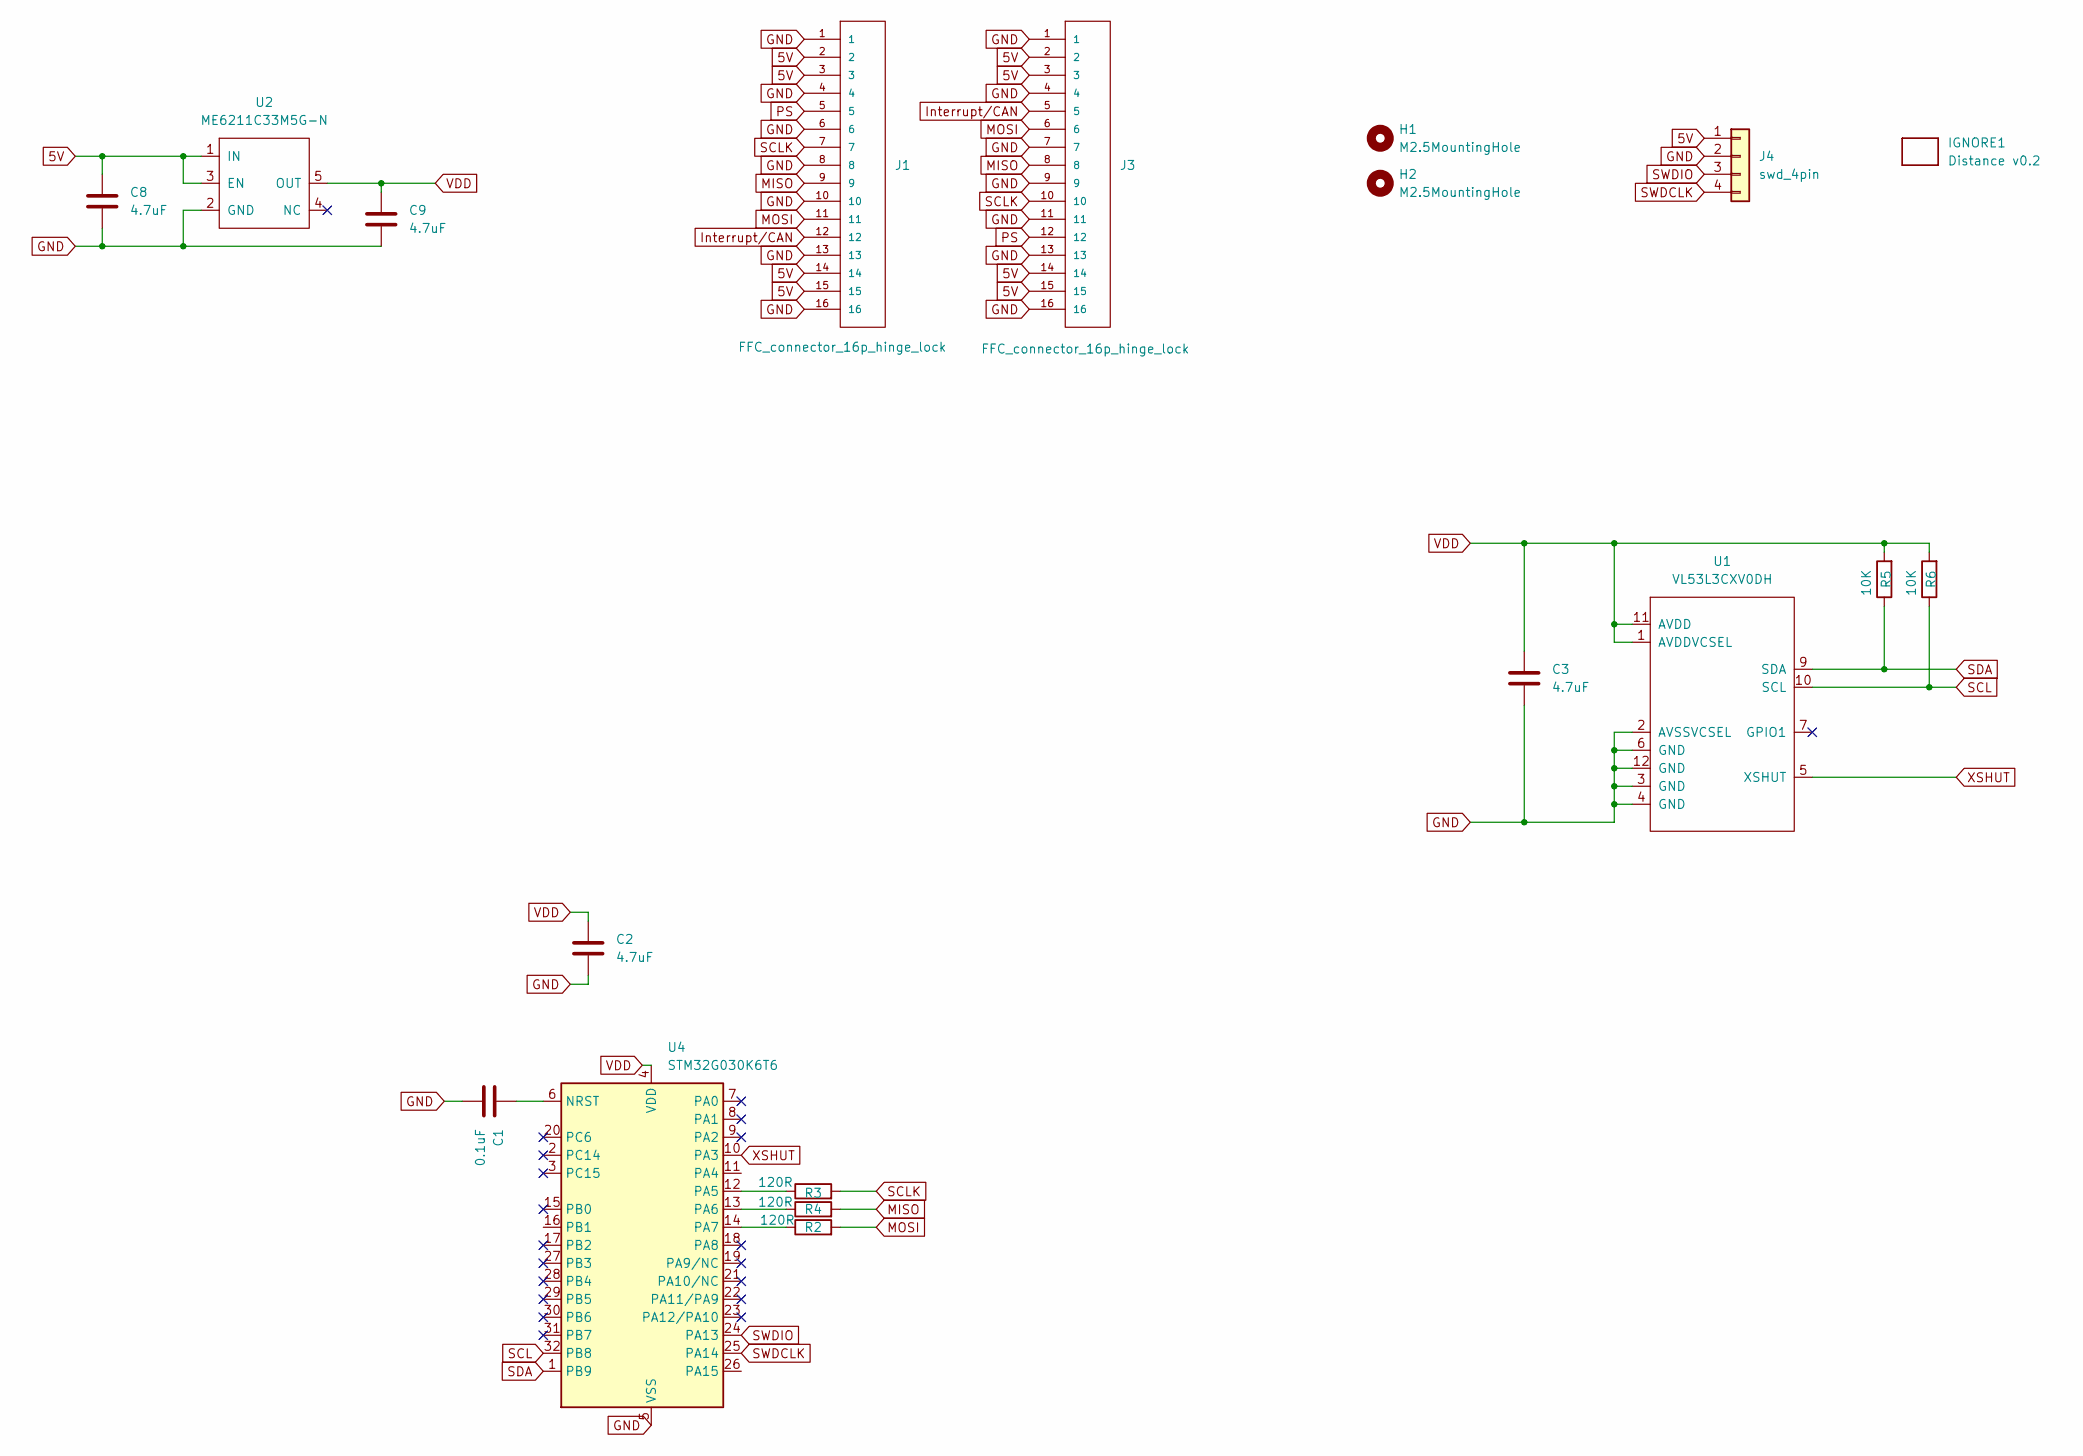
[picture p54: schematic Distance.kicad_sch]

Parts:
C1: 0.1uF; C_0402_1005Metric
C2, C3, C8, C9: 4.7uF; C_0402_1005Metric
H1, H2: M2.5MountingHole; MountingHole_2.7mm_M2.5_ISO7380
IGNORE1: Distance v0.2; BoardText
J1, J3: FFC_connector_16p_hinge_lock
J4: swd_4pin; swd_header
R2, R3, R4: 120R; R_0402_1005Metric
R5, R6: 10K; R_0402_1005Metric
U1: VL53L3CXV0DH
U2: ME6211C33M5G-N; SOT-23-5
U4: STM32G030K6T6; LQFP-32_7x7mm_P0.8mm

Connections:
5V: C8.1, J1.2, J1.3, J1.14, J1.15, J3.2, J3.3, J3.14, J3.15, J4.1, U2.1 (IN), U2.3 (EN)
GND: C1.2, C2.2, C3.2, C8.2, C9.2, J1.1, J1.4, J1.6, J1.8, J1.10, J1.13, J1.16, J3.1, J3.4, J3.7, J3.9, J3.11, J3.13, J3.16, J4.2, U1.2 (AVSSVCSEL), U1.3 (GND), U1.4 (GND), U1.6 (GND), U1.12 (GND), U2.2 (GND), U4.5 (VSS)
Interrupt/CAN: J1.12, J3.5
MISO: J1.9, J3.8, R4.2
MOSI: J1.11, J3.6, R2.2
unnamed: C1.1, U4.6 (NRST)
unnamed: R3.1, U4.12 (PA5)
unnamed: R4.1, U4.13 (PA6)
unnamed: R2.1, U4.14 (PA7)
PS: J1.5, J3.12
SCL: R6.1, U1.10 (SCL), U4.32 (PB8)
SCLK: J1.7, J3.10, R3.2
SDA: R5.1, U1.9 (SDA), U4.1 (PB9)
SWDCLK: J4.4, U4.25 (PA14)
SWDIO: J4.3, U4.24 (PA13)
VDD: C2.1, C3.1, C9.1, R5.2, R6.2, U1.1 (AVDDVCSEL), U1.11 (AVDD), U2.5 (OUT), U4.4 (VDD)
XSHUT: U1.5 (XSHUT), U4.10 (PA3)

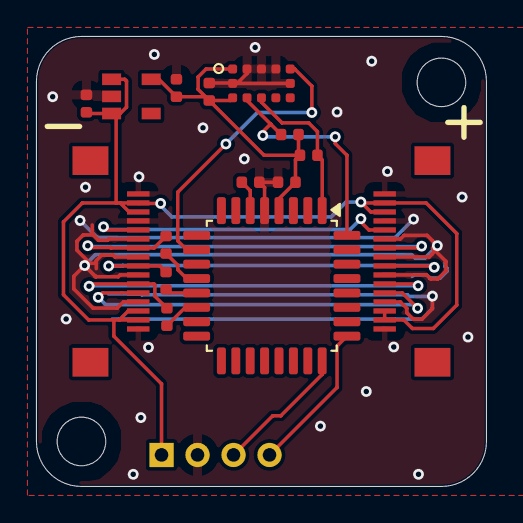
[picture p55: board Distance.kicad_pcb from above]

Board: 4 copper layers, 25.0 x 25.0 mm, 19 parts (0 on the bottom side), 17 nets.
