sean618/MakerTiles/hardware/Boards/Speaker/v0.8/Speaker.kicad_pcb

## KiCad design hardware/Boards/Speaker/v0.8/Speaker.kicad_pcb (2026-06-21, an earlier design)

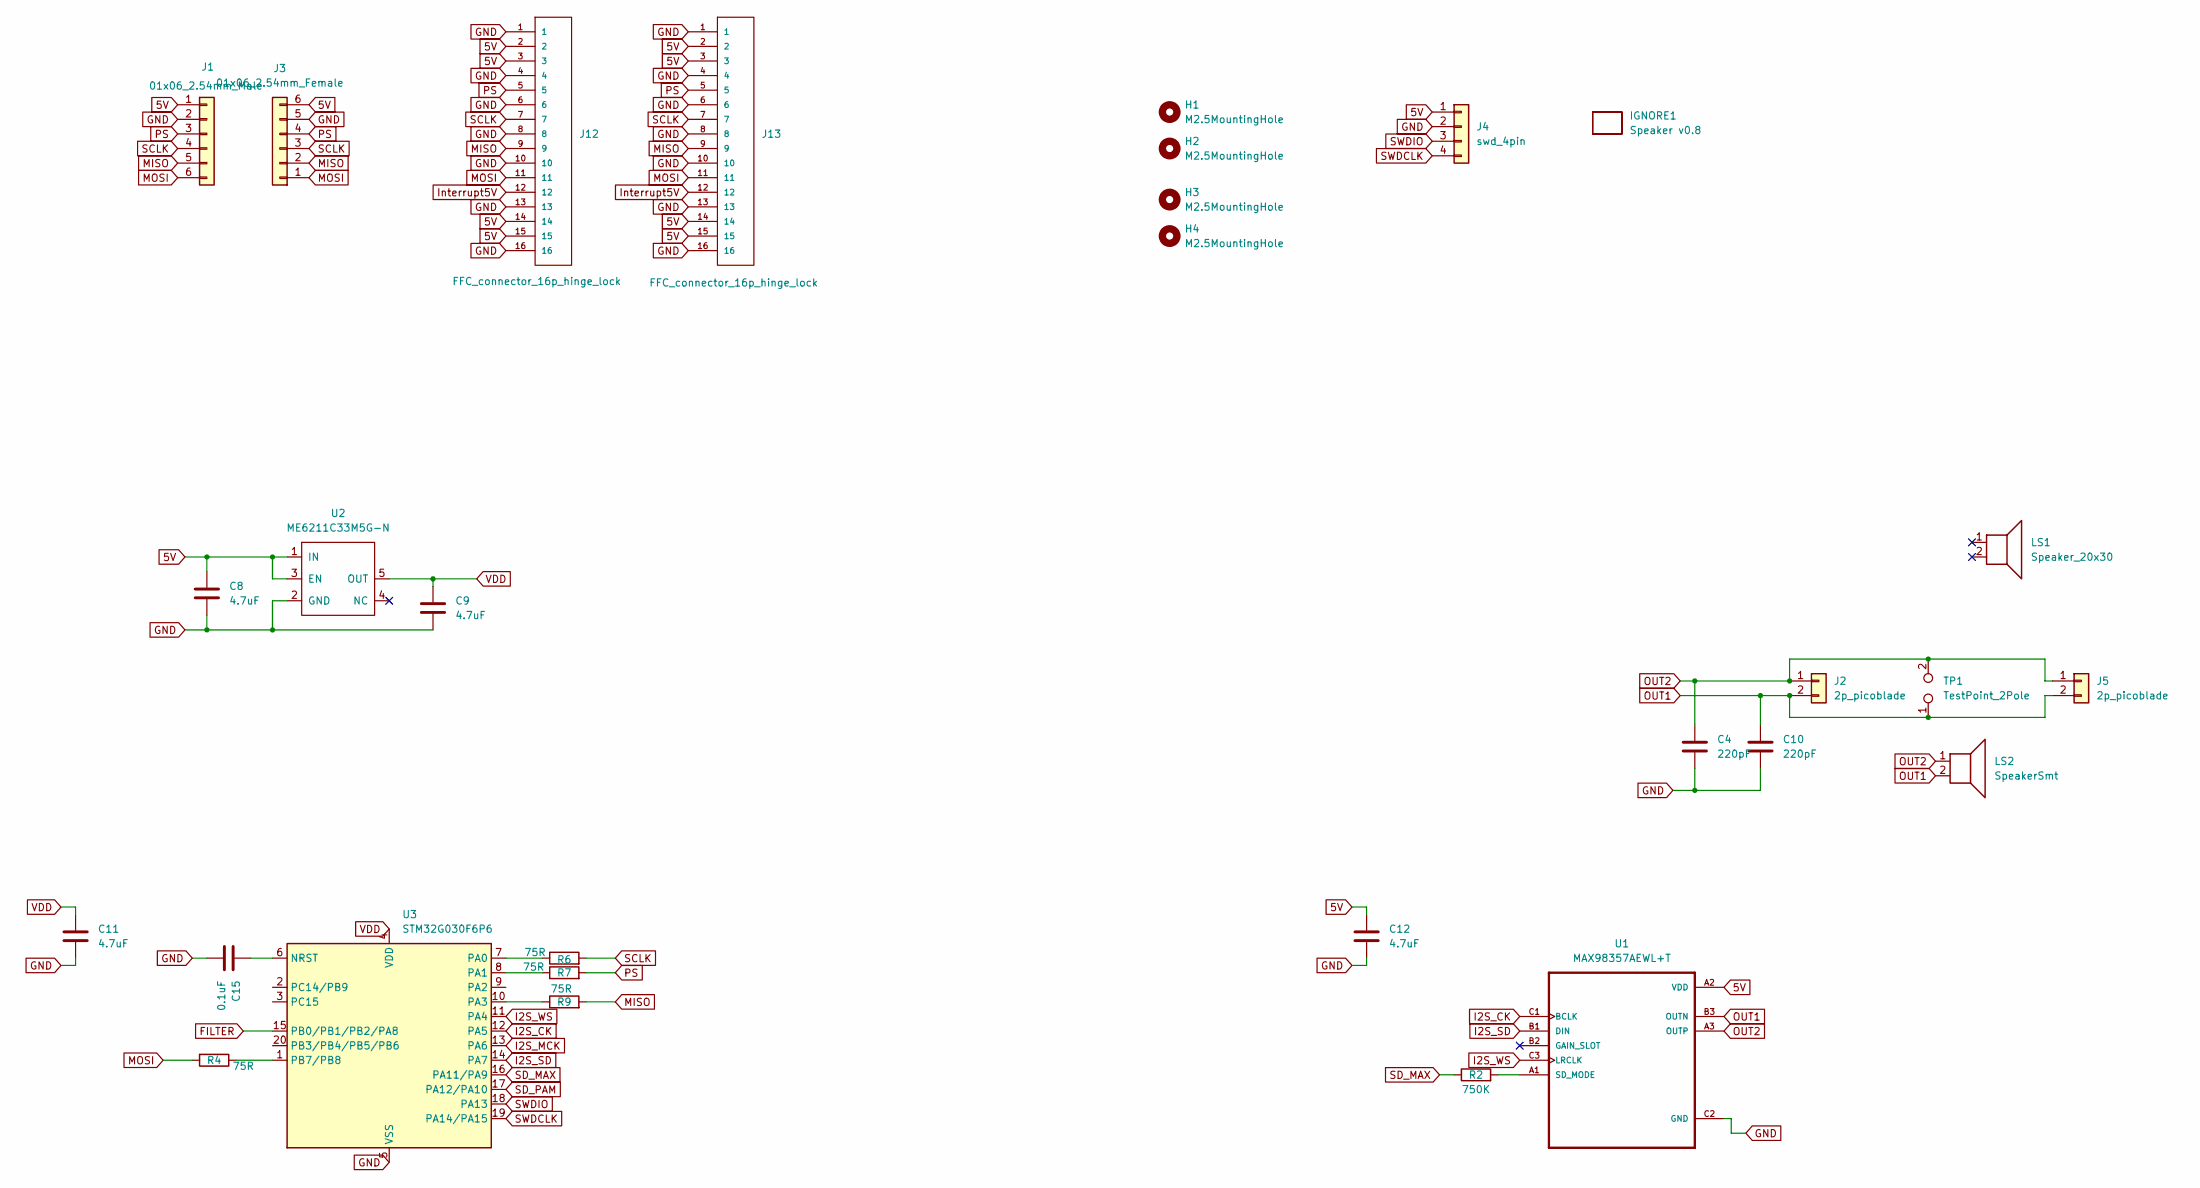
[picture p56: schematic Speaker.kicad_sch]

Parts:
C4, C10: 220pF; C_0402_1005Metric
C8, C9, C11, C12: 4.7uF; C_0402_1005Metric
C15: 0.1uF; C_0402_1005Metric
H1, H2, H3, H4: M2.5MountingHole; MountingHole_2.7mm_M2.5_ISO7380
IGNORE1: Speaker v0.8; BoardText
J1: 01x06_2.54mm_Male
J2, J5: 2p_picoblade; Molex_PicoBlade_53261-0271_1x02-1MP_P1.25mm_Horizontal
J3: 01x06_2.54mm_Female
J4: swd_4pin; swd_header
J12, J13: FFC_connector_16p_hinge_lock
LS1: Speaker_20x30
LS2: SpeakerSmt; Speaker1.8x1.8
R2: 750K; R_0402_1005Metric
R4, R6, R7, R9: 75R; R_0402_1005Metric
TP1: TestPoint_2Pole; TestPoint_2Pads_Pitch2.54mm_Drill0.8mm
U1: MAX98357AEWL+T; WLP-9_1.448x1.468mm_Layout3x3_P0.4mm_Ball0.27mm_Pad0.25mm
U2: ME6211C33M5G-N; SOT-23-5
U3: STM32G030F6P6; TSSOP-20_4.4x6.5mm_P0.65mm

Connections:
5V: C8.1, C12.1, J1.1, J3.6, J4.1, J12.2, J12.3, J12.14, J12.15, J13.2, J13.3, J13.14, J13.15, U1.A2 (VDD), U2.1 (IN), U2.3 (EN)
FILTER: U3.15 (PB0/PB1/PB2/PA8)
GND: C4.2, C8.2, C9.2, C10.2, C11.2, C12.2, C15.2, J1.2, J3.5, J4.2, J12.1, J12.4, J12.6, J12.8, J12.10, J12.13, J12.16, J13.1, J13.4, J13.6, J13.8, J13.10, J13.13, J13.16, U1.C2 (GND), U2.2 (GND), U3.5 (VSS)
I2S_CK: U1.C1 (BCLK), U3.12 (PA5)
I2S_MCK: U3.13 (PA6)
I2S_SD: U1.B1 (DIN), U3.14 (PA7)
I2S_WS: U1.C3 (LRCLK), U3.11 (PA4)
Interrupt5V: J12.12, J13.12
MISO: J1.5, J3.2, J12.9, J13.9, R9.2
MOSI: J1.6, J3.1, J12.11, J13.11, R4.2
unnamed: R2.2, U1.A1 (SD_MODE)
unnamed: C15.1, U3.6 (NRST)
unnamed: R6.1, U3.7 (PA0)
unnamed: R7.1, U3.8 (PA1)
unnamed: R9.1, U3.10 (PA3)
unnamed: R4.1, U3.1 (PB7/PB8)
OUT1: C10.1, J2.2, J5.2, LS2.2, TP1.1, U1.B3 (OUTN)
OUT2: C4.1, J2.1, J5.1, LS2.1, TP1.2, U1.A3 (OUTP)
PS: J1.3, J3.4, J12.5, J13.5, R7.2
SCLK: J1.4, J3.3, J12.7, J13.7, R6.2
SD_MAX: R2.1, U3.16 (PA11/PA9)
SD_PAM: U3.17 (PA12/PA10)
SWDCLK: J4.4, U3.19 (PA14/PA15)
SWDIO: J4.3, U3.18 (PA13)
VDD: C9.1, C11.1, U2.5 (OUT), U3.4 (VDD)

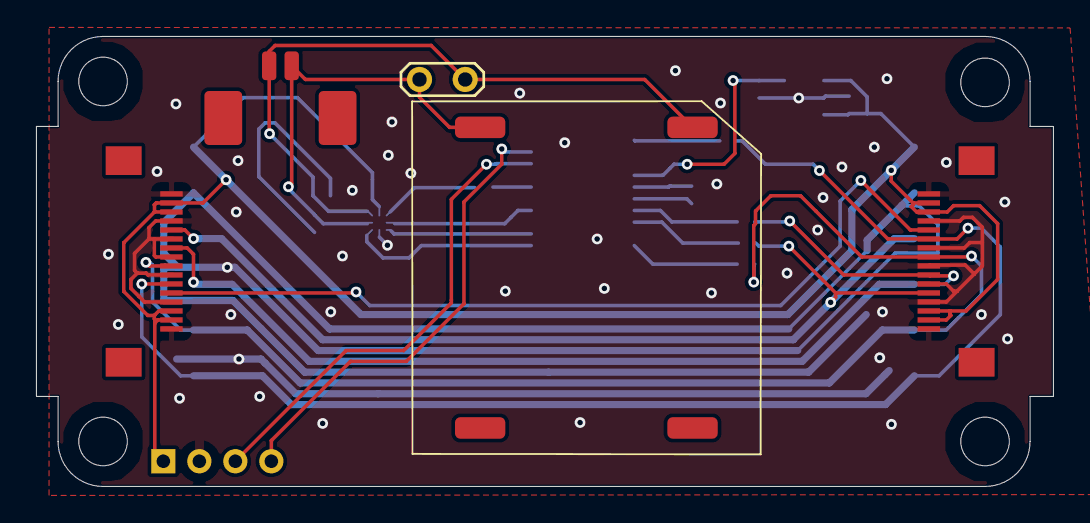
[picture p57: board hardware/Boards/Speaker/v0.8/Speaker.kicad_pcb from above]

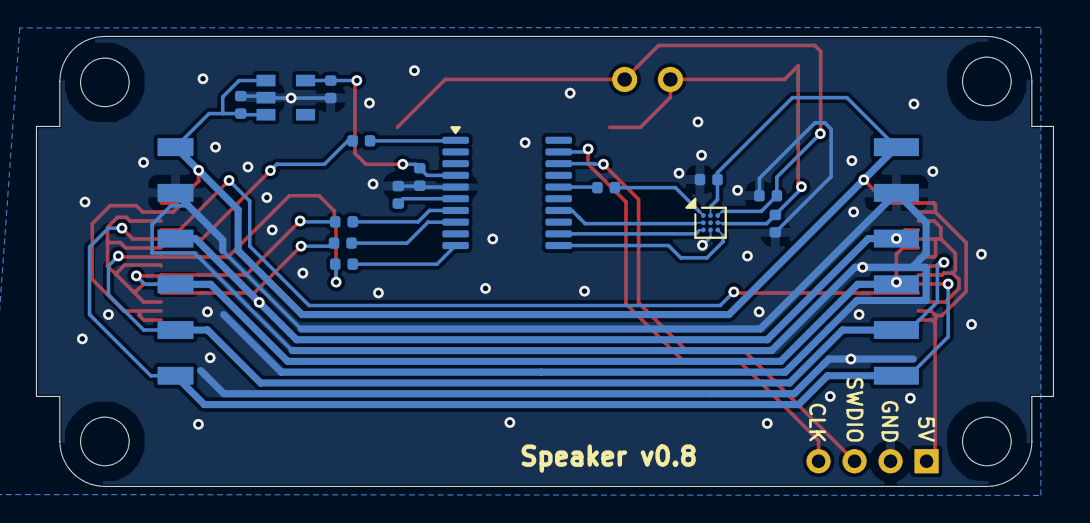
[picture p58: board hardware/Boards/Speaker/v0.8/Speaker.kicad_pcb from below]

Board: 2 copper layers, 56.5 x 25.0 mm, 28 parts (17 on the bottom side), 22 nets.
