sean618/MakerTiles/hardware/Boards/Extra/Magnet/v0.1/Magnet.kicad_sch

## KiCad design hardware/Boards/Extra/Magnet/v0.1/Magnet.kicad_sch (2026-06-21)

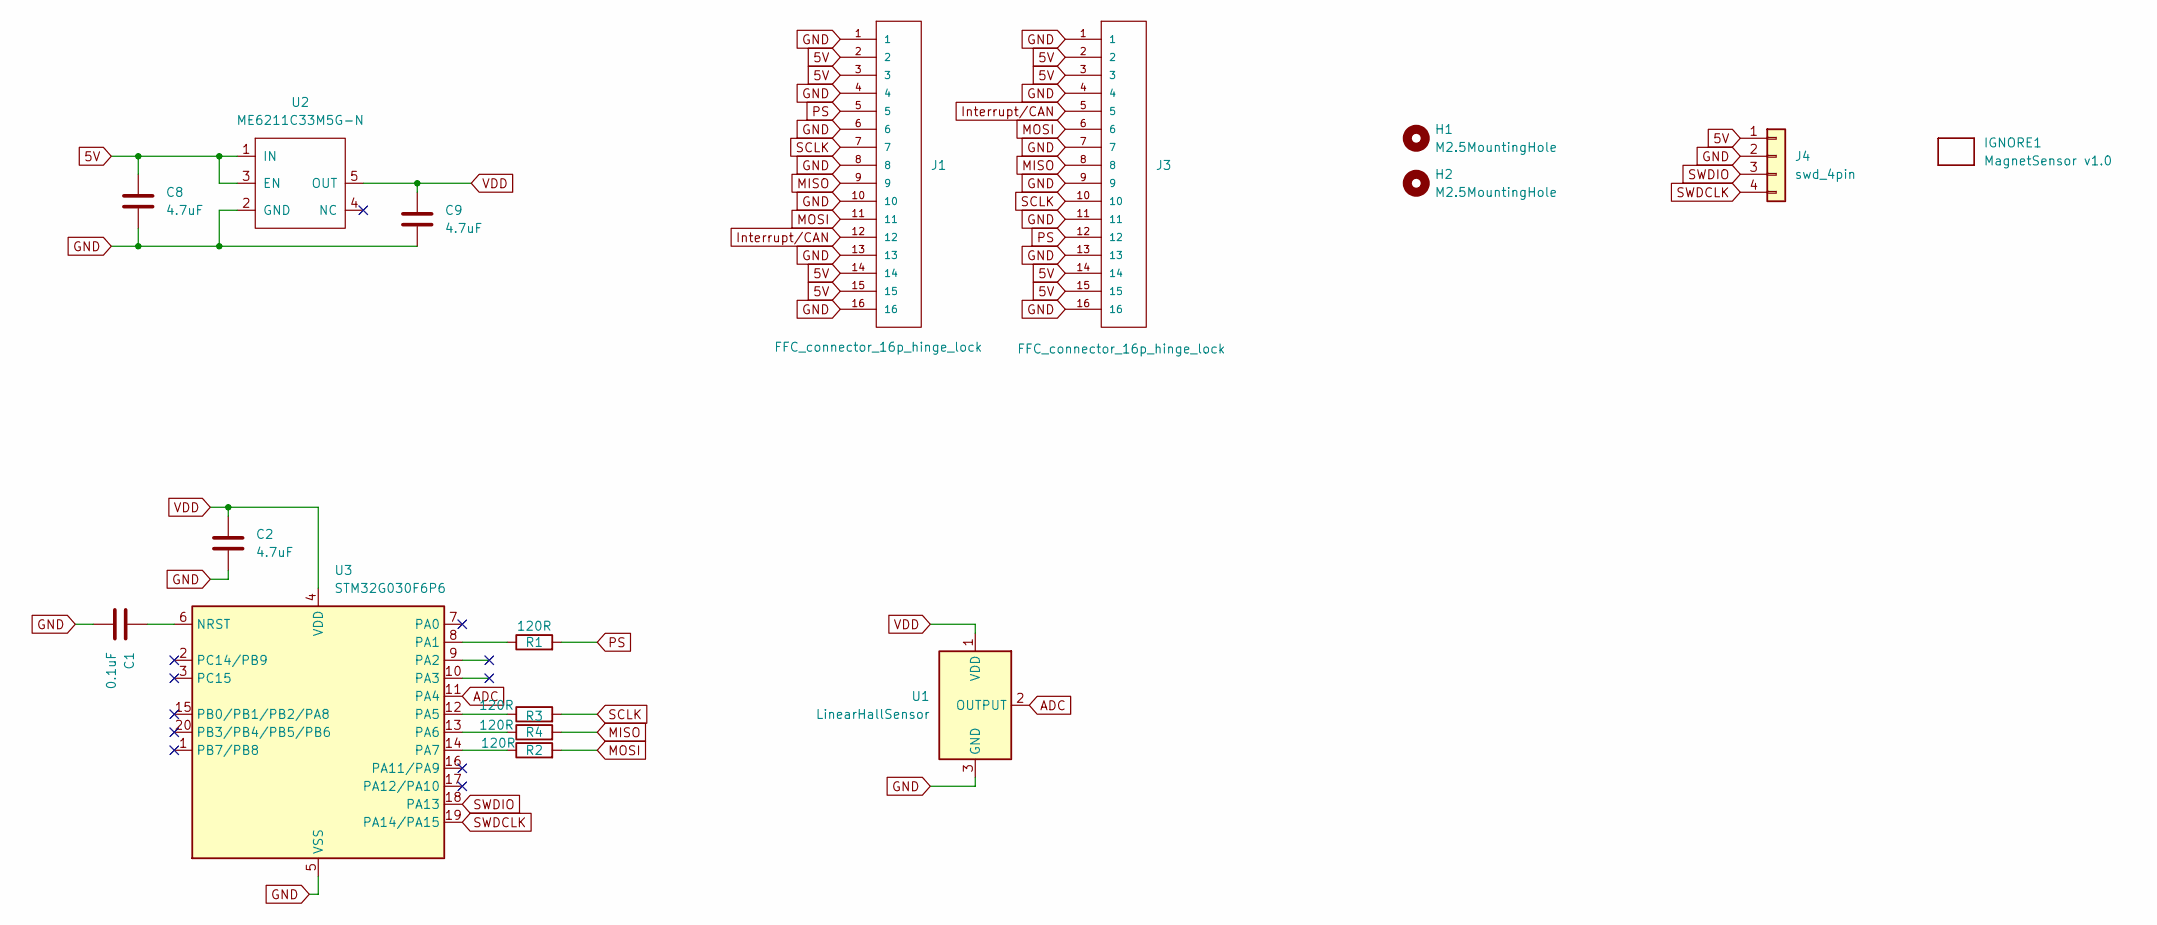
[picture p59: schematic Magnet.kicad_sch]

Parts:
C1: 0.1uF; C_0402_1005Metric
C2, C8, C9: 4.7uF; C_0402_1005Metric
H1, H2: M2.5MountingHole; MountingHole_2.7mm_M2.5_ISO7380
IGNORE1: MagnetSensor v1.0; BoardText
J1, J3: FFC_connector_16p_hinge_lock
J4: swd_4pin; swd_header
R1, R2, R3, R4: 120R; R_0402_1005Metric
U1: LinearHallSensor; SOT-23
U2: ME6211C33M5G-N; SOT-23-5
U3: STM32G030F6P6; TSSOP-20_4.4x6.5mm_P0.65mm

Connections:
5V: C8.1, J1.2, J1.3, J1.14, J1.15, J3.2, J3.3, J3.14, J3.15, J4.1, U2.1 (IN), U2.3 (EN)
ADC: U1.2 (OUTPUT), U3.11 (PA4)
GND: C1.2, C2.2, C8.2, C9.2, J1.1, J1.4, J1.6, J1.8, J1.10, J1.13, J1.16, J3.1, J3.4, J3.7, J3.9, J3.11, J3.13, J3.16, J4.2, U1.3 (GND), U2.2 (GND), U3.5 (VSS)
Interrupt/CAN: J1.12, J3.5
MISO: J1.9, J3.8, R4.2
MOSI: J1.11, J3.6, R2.2
unnamed: C1.1, U3.6 (NRST)
unnamed: R1.1, U3.8 (PA1)
unnamed: R2.1, U3.14 (PA7)
unnamed: R3.1, U3.12 (PA5)
unnamed: R4.1, U3.13 (PA6)
PS: J1.5, J3.12, R1.2
SCLK: J1.7, J3.10, R3.2
SWDCLK: J4.4, U3.19 (PA14/PA15)
SWDIO: J4.3, U3.18 (PA13)
VDD: C2.1, C9.1, U1.1 (VDD), U2.5 (OUT), U3.4 (VDD)
