sean618/MakerTiles/hardware/Boards/Extra/NFC/v0.1/NFC.kicad_sch

## KiCad design hardware/Boards/Extra/NFC/v0.1/NFC.kicad_sch (2026-06-21)

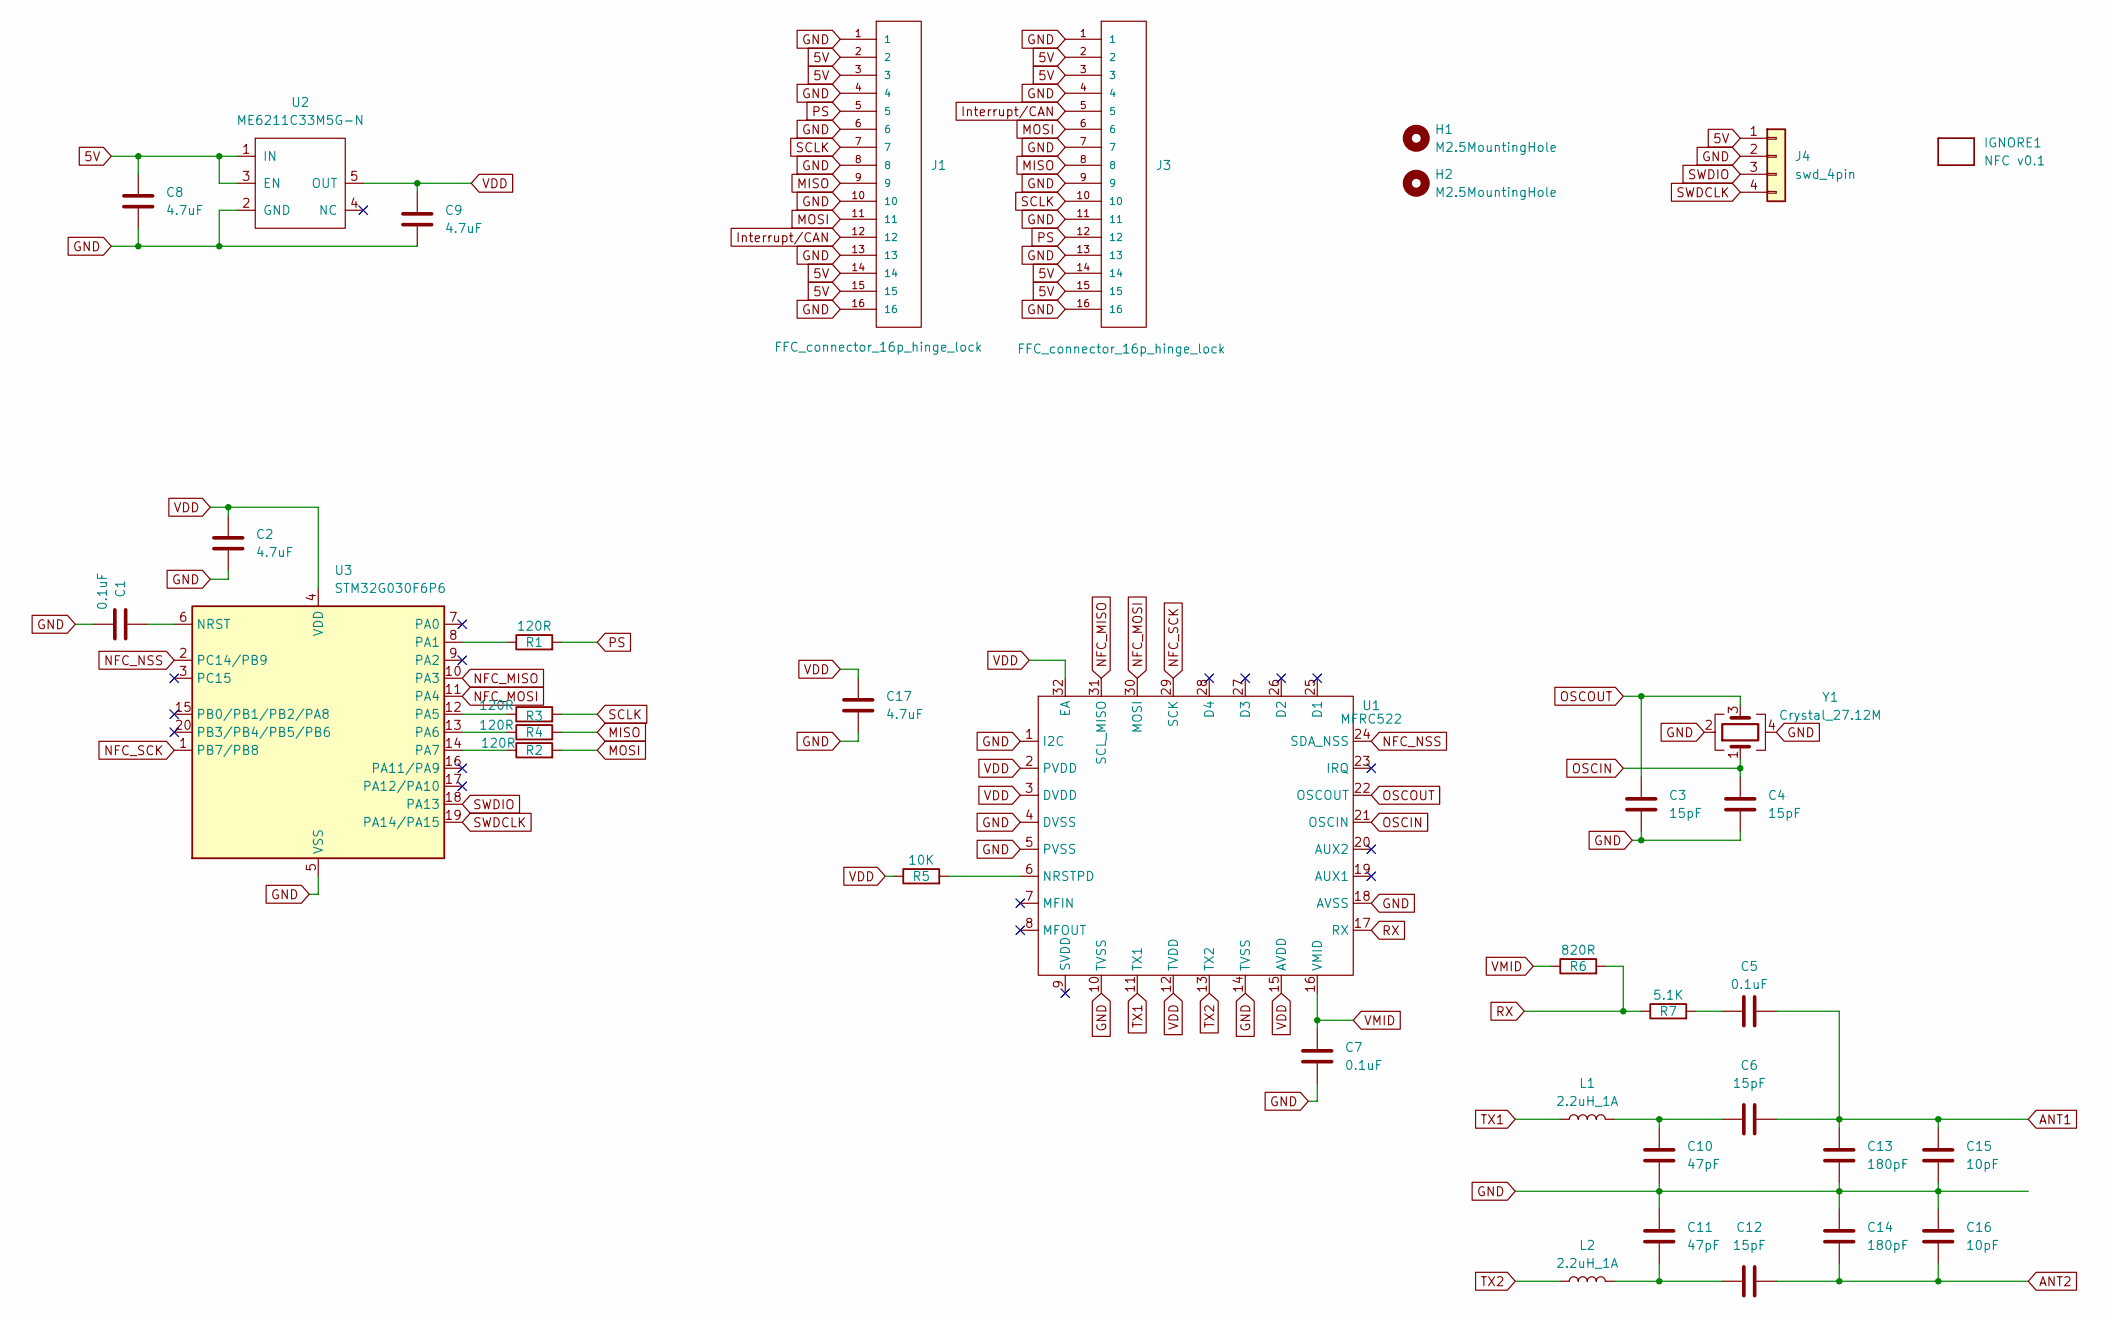
[picture p60: schematic NFC.kicad_sch]

Parts:
C1, C5, C7: 0.1uF; C_0402_1005Metric
C2, C8, C9, C17: 4.7uF; C_0402_1005Metric
C3, C4, C6, C12: 15pF; C_0402_1005Metric
C10, C11: 47pF; C_0402_1005Metric
C13, C14: 180pF; C_0402_1005Metric
C15, C16: 10pF; C_0402_1005Metric
H1, H2: M2.5MountingHole; MountingHole_2.7mm_M2.5_ISO7380
IGNORE1: NFC v0.1; BoardText
J1, J3: FFC_connector_16p_hinge_lock
J4: swd_4pin; swd_header
L1, L2: 2.2uH_1A; R_0603_1608Metric_Pad0.98x0.95mm_HandSolder
R1, R2, R3, R4: 120R; R_0402_1005Metric
R5: 10K; R_0402_1005Metric
R6: 820R; R_0402_1005Metric
R7: 5.1K; R_0402_1005Metric
U1: MFRC522; HVQFN-32-1EP_5x5mm_P0.5mm_EP3.1x3.1mm
U2: ME6211C33M5G-N; SOT-23-5
U3: STM32G030F6P6; TSSOP-20_4.4x6.5mm_P0.65mm
Y1: Crystal_27.12M; Crystal_SMD_3225-4Pin_3.2x2.5mm

Connections:
5V: C8.1, J1.2, J1.3, J1.14, J1.15, J3.2, J3.3, J3.14, J3.15, J4.1, U2.1 (IN), U2.3 (EN)
ANT1: C5.2, C6.2, C13.2, C15.2
ANT2: C12.2, C14.1, C16.1
GND: C1.2, C2.2, C3.2, C4.2, C7.1, C8.2, C9.2, C10.1, C11.2, C13.1, C14.2, C15.1, C16.2, C17.2, J1.1, J1.4, J1.6, J1.8, J1.10, J1.13, J1.16, J3.1, J3.4, J3.7, J3.9, J3.11, J3.13, J3.16, J4.2, U1.1 (I2C), U1.4 (DVSS), U1.5 (PVSS), U1.10 (TVSS), U1.14 (TVSS), U1.18 (AVSS), U1.33 (PVSS), U2.2 (GND), U3.5 (VSS), Y1.2, Y1.4
Interrupt/CAN: J1.12, J3.5
MISO: J1.9, J3.8, R4.2
MOSI: J1.11, J3.6, R2.2
NFC_MISO: U1.31 (SCL_MISO), U3.10 (PA3)
NFC_MOSI: U1.30 (MOSI), U3.11 (PA4)
NFC_NSS: U1.24 (SDA_NSS), U3.2 (PC14/PB9)
NFC_SCK: U1.29 (SCK), U3.1 (PB7/PB8)
unnamed: C1.1, U3.6 (NRST)
unnamed: C5.1, R7.2
unnamed: C6.1, C10.2, L1.2
unnamed: C11.1, C12.1, L2.2
unnamed: R1.1, U3.8 (PA1)
unnamed: R2.1, U3.14 (PA7)
unnamed: R3.1, U3.12 (PA5)
unnamed: R4.1, U3.13 (PA6)
unnamed: R5.2, U1.6 (NRSTPD)
OSCIN: C4.1, U1.21 (OSCIN), Y1.1
OSCOUT: C3.1, U1.22 (OSCOUT), Y1.3
PS: J1.5, J3.12, R1.2
RX: R6.2, R7.1, U1.17 (RX)
SCLK: J1.7, J3.10, R3.2
SWDCLK: J4.4, U3.19 (PA14/PA15)
SWDIO: J4.3, U3.18 (PA13)
TX1: L1.1, U1.11 (TX1)
TX2: L2.1, U1.13 (TX2)
VDD: C2.1, C9.1, C17.1, R5.1, U1.2 (PVDD), U1.3 (DVDD), U1.12 (TVDD), U1.15 (AVDD), U1.32 (EA), U2.5 (OUT), U3.4 (VDD)
VMID: C7.2, R6.1, U1.16 (VMID)
