sean618/MakerTiles/hardware/Boards/Extra/Temperature/v0.5/Temp.kicad_sch

## KiCad design hardware/Boards/Extra/Temperature/v0.5/Temp.kicad_sch (2026-06-21)

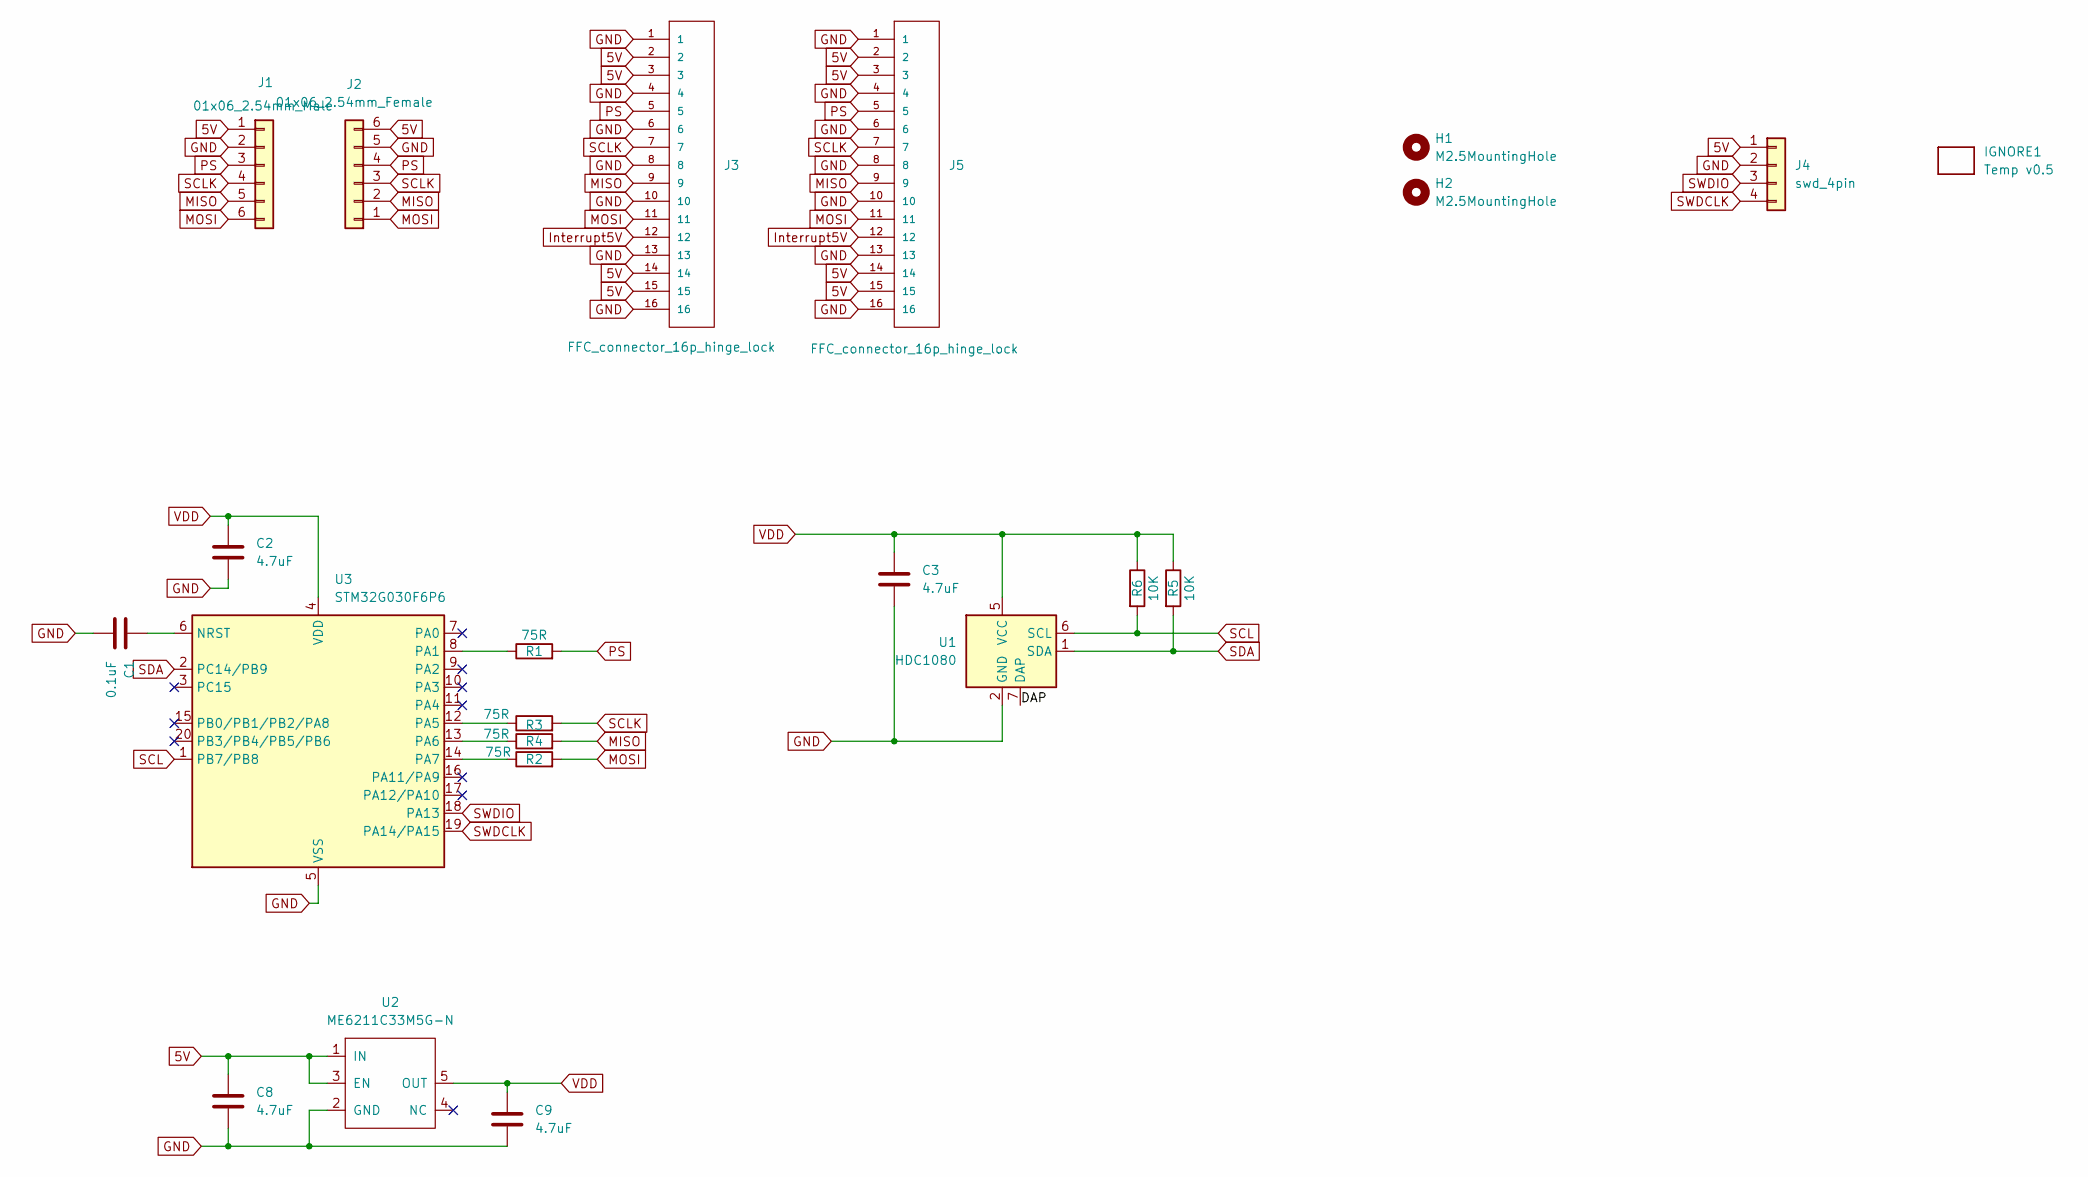
[picture p61: schematic Temp.kicad_sch]

Parts:
C1: 0.1uF; C_0402_1005Metric
C2, C3, C8, C9: 4.7uF; C_0402_1005Metric
H1, H2: M2.5MountingHole; MountingHole_2.7mm_M2.5_ISO7380
IGNORE1: Temp v0.5; BoardText
J1: 01x06_2.54mm_Male
J2: 01x06_2.54mm_Female
J3, J5: FFC_connector_16p_hinge_lock
J4: swd_4pin; swd_header
R1, R2, R3, R4: 75R; R_0402_1005Metric
R5, R6: 10K; R_0402_1005Metric
U1: HDC1080; Texas_PWSON-N6
U2: ME6211C33M5G-N; SOT-23-5
U3: STM32G030F6P6; TSSOP-20_4.4x6.5mm_P0.65mm

Connections:
5V: C8.1, J1.1, J2.6, J3.2, J3.3, J3.14, J3.15, J4.1, J5.2, J5.3, J5.14, J5.15, U2.1 (IN), U2.3 (EN)
DAP: U1.7 (DAP)
GND: C1.2, C2.2, C3.2, C8.2, C9.2, J1.2, J2.5, J3.1, J3.4, J3.6, J3.8, J3.10, J3.13, J3.16, J4.2, J5.1, J5.4, J5.6, J5.8, J5.10, J5.13, J5.16, U1.2 (GND), U2.2 (GND), U3.5 (VSS)
Interrupt5V: J3.12, J5.12
MISO: J1.5, J2.2, J3.9, J5.9, R4.2
MOSI: J1.6, J2.1, J3.11, J5.11, R2.2
unnamed: C1.1, U3.6 (NRST)
unnamed: R1.1, U3.8 (PA1)
unnamed: R2.1, U3.14 (PA7)
unnamed: R3.1, U3.12 (PA5)
unnamed: R4.1, U3.13 (PA6)
PS: J1.3, J2.4, J3.5, J5.5, R1.2
SCL: R6.2, U1.6 (SCL), U3.1 (PB7/PB8)
SCLK: J1.4, J2.3, J3.7, J5.7, R3.2
SDA: R5.2, U1.1 (SDA), U3.2 (PC14/PB9)
SWDCLK: J4.4, U3.19 (PA14/PA15)
SWDIO: J4.3, U3.18 (PA13)
VDD: C2.1, C3.1, C9.1, R5.1, R6.1, U1.5 (VCC), U2.5 (OUT), U3.4 (VDD)
