sean618/MakerTiles/firmware/Boards/Battery/Core/Inc/project.h

#ifndef PROJECT_H
#define PROJECT_H

#include "stm32g030xx.h" // GPIO defs
#include "stm32g0xx_hal.h" // Get tick, delay
#include "stm32g0xx_hal_tim.h"
#include "FieldProtocol/fpCommon.hpp"
#include "Libraries/myAssert.h"

#define ENABLE_BATTERY_MODULE

#define MAX_MICROBUS_TX_PACKETS 4
#define MAX_MICROBUS_RX_PACKETS 4

#endif
